hiperiondev/esp32idf_APRS/docs/en/internals/architecture.rst

.. _en-architecture:

============
Architecture
============

Boot sequence
=============

``app_main()`` runs on the system main task, whose stack is set by
``CONFIG_ESP_MAIN_TASK_STACK_SIZE`` and is not meant to host heavy work —
``esp_netif`` + ``esp_wifi`` + ``esp_http_server`` + cJSON can use several KB of
stack between them. So ``app_main()`` does only the three things that must
precede everything, then hands off to a dedicated task:

.. code-block:: text

   app_main()
    ├─ ptt_force_idle()          (PTT pad driven to its idle level; unconfigured from reset until here)
    ├─ nvs_flash_init()          (erase+retry on NO_FREE_PAGES / NEW_VERSION_FOUND)
    ├─ storage_init()            (mount LittleFS at /storage, auto-format on first boot)
    └─ xTaskCreate(app_task, 8192 B, prio 5)   ── and returns; FreeRTOS reclaims the main task

   app_task()
    ├─ app_config_load()                  ← one file per functionality under /storage, creating any that are missing
    ├─ cpu_freq_apply()                   ← 80/160/240 MHz from the System page
    ├─ net_state_init()                   ← "no internet yet"
    ├─ wifi_init()                        ← AP / STA / AP+STA per g_config.wifi_mode
    ├─ vTaskDelay(10 ms)                  ← yield so IDLE runs; avoids a false TWDT trip
    ├─ time_sync_start()                  ← arms the SNTP state machine (non-blocking)
    ├─ gps_apply_config()                 ← starts the GNSS reader task if enabled in config
    ├─ (confirm OTA image valid if pending-verify)
    ├─ aprs_service_start()               ← ⚠ MUST precede modem_init(): installs the RX callback
    ├─ if (audio_modem_en) modem_init()   ← ⏳ BLOCKS ~5 s calibrating the real ADC clock (once per boot)
    │      └─ aprs_service_notify_modem_ready()
    ├─ telegram_app_apply_config()        ← non-blocking; its own task waits for the network
    ├─ web_server_start_when_heap_ready() ← waits up to 5 s for a ≥24 KB largest free block, then
    │      └─ web_server_start()            starts regardless: esp_http_server, ~70 URI handlers, 20 KB stack
    └─ vTaskDelete(NULL)                  ← returns app_task's 8 KB stack to the heap

Three ordering rules are load-bearing and commented as such in the source:

#. **``aprs_service_start()`` before ``modem_init()``** — the modem starts
   delivering frames *from inside* ``modem_init()``; the RX callback must
   already be installed.
#. **Beacons start before the modem is ready** — they transmit immediately on
   entry, so ``aprs_service_send_tnc2()`` drops frames with a debug log until
   ``s_modemReady`` is set, rather than reaching the AX.25 writer before the
   AX.25 layer is initialised.
#. **The web admin server starts last** — every other service has already made
   its allocations by the time it runs, so its largest-contiguous-free-block
   check (``WEB_SERVER_MIN_LARGEST_FREE_BLOCK``, 24 KB, the httpd task's 20 KB
   stack plus headroom) sees the heap in the state the station will actually
   run in. A large total free heap does not guarantee this single allocation
   can be satisfied if the heap is fragmented, which is why the block size is
   checked rather than the total. It waits up to
   ``WEB_SERVER_HEAP_WAIT_MAX_MS`` (5 s) for a block that size to be free,
   polling every ``WEB_SERVER_HEAP_POLL_INTERVAL_MS`` (100 ms), then starts
   the server regardless of whether the threshold was reached: a reachable
   admin UI under memory pressure is more useful than none at all.

Inside ``aprs_service_start()``
===============================

.. code-block:: text

   aprs_service_start()
    ├─ trafficlog_init / lastheard_init / message_init
    ├─ message_set_tx_handler / igate_set_inet2rf_handler / igate_set_inet2rf_assoc_query
    ├─ xTaskCreate(rxTask "aprs_rx") + modem_set_rx_callback(on_rx_frame)
    │                                ← callback only queues; aprs_rx decodes and dispatches
    ├─ igate_start()                 ← always started; self-idles when nothing needs APRS-IS
    ├─ beacon_start() / weather_start() / bulletins_start() / objitems_start() / telemetry_start()
    ├─ beacon_scheduler_start()      ← ONE shared task drives all periodic TX and query answers
    └─ xTaskCreate(serviceTickTask)  ← 1 Hz: heap sample + weather refresh + message retry + time-sync SM

Task map
========

.. list-table::
   :header-rows: 1
   :widths: 20 12 8 10 22 28

   * - Task
     - Stack
     - Prio
     - Core
     - Created by
     - Role
   * - ``app_task``
     - 8192 B
     - 5
     - any
     - ``app_main``
     - boot, then deletes itself
   * - modem RX DSP
     - 4096 B
     - 10
     - **0**
     - ``AFSK_init()``
     - drains the ADC ring, runs the demodulators
   * - ``modem_svc``
     - 6144 B
     - 5
     - **0**
     - ``modem_init()``
     - drives TX (quiet time, DCD, persistence, key-up, teardown, TX time-out)
       and hands each RX frame to the callback, which only copies it into the
       ``aprs_rx`` queue; pinned to the same core as the RX DSP task, whose
       AX.25 ring it consumes
   * - ``aprs_rx``
     - 6144 B
     - 4
     - any
     - ``aprs_service_start()``
     - decodes each received frame and dispatches it: digipeater, IGate
       RF→INET, messages, queries, Winlink, Telegram routing, LAST HEARD,
       traffic log. Fed by an 8-frame queue, so a slow APRS-IS send never
       stalls transmit servicing
   * - ``modem_init``
     - 4096 B
     - high
     - **1**
     - ``AFSK_init()``
     - transient: runs the DAC sample-clock bring-up on the core that must own
       its interrupt, then deletes itself
   * - ADC DMA ISR
     - —
     - —
     - **0**
     - driver
     - conversion frames → ring buffer
   * - DAC sample clock (GPTimer, lvl 3)
     - —
     - —
     - **1**
     - ``AFSK_init()``
     - one DAC sample every 1/38400 s
   * - ``igate_task``
     - 6144 B
     - 5
     - any
     - ``igate_start()``
     - APRS-IS socket, login, RX pump, reconnect
   * - ``beacon_sched``
     - 14336 B
     - 4
     - any
     - ``beacon_scheduler_start()``
     - ONE shared task: all periodic own-station TX, plus the APRS query answers
       deferred to it
   * - ``aprs_svc_tick``
     - 10240 B
     - 4
     - any
     - ``aprs_service_start()``
     - 1 Hz: heap sample + weather refresh + message retry + time sync
   * - ``gps``
     - 4096 B
     - 4
     - any
     - ``gps_apply_config()``
     - reads the GNSS UART and parses NMEA; created only while the receiver is
       switched on, and deleted again when it is switched off
   * - ``telegram_service``
     - 8192 B
     - 5
     - any
     - ``telegram_app_apply_config()``
     - Telegram long polling over HTTPS and command dispatch; created only
       while the bot is switched on
   * - ``telegram_wk``
     - 8192 B
     - 4
     - any
     - ``telegram_app.c``
     - transient: runs one bot bring-up, teardown or send off the caller's
       stack, so a web POST never waits on TLS
   * - ``httpd``
     - 20480 B
     - —
     - any
     - ``web_server_start()``
     - web admin
   * - ``loop_diag``
     - 3072 B
     - 7
     - any
     - ``aprs_loop_test_run()``
     - transient: latches modem diagnostics for the duration of a LOOP TEST
   * - ``ota_reboot``
     - 2048 B
     - 5
     - any
     - the About page's OTA upload handler
     - transient: waits 1.5 s after a successful firmware upload — so the
       browser's XHR completes and the "rebooting..." message is actually
       seen — then calls ``esp_restart()``
   * - ``esp_timer``
     - —
     - —
     - —
     - IDF
     - Wi-Fi reconnect back-off

``beacon_sched`` and ``aprs_svc_tick`` are both created unconditionally inside
``aprs_service_start()``, i.e. before ``modem_init()``, the Telegram bot, and
``httpd`` — so their combined 24576 B is committed at boot regardless of
whether the operator has the modem or Telegram enabled for that boot. Both are
core, always-needed services, so starting them unconditionally is correct; only
their *sizes* are sized with headroom rather than trimmed to a measured
minimum, the same way ``GPS_TASK_STACK_BYTES`` and the ``httpd``
``config.stack_size`` are (see ``BEACON_SCHED_TASK_STACK_BYTES`` in
``beacon_scheduler.c`` and ``APRS_SVC_TICK_TASK_STACK_BYTES`` in
``aprs_service.c``). Both tasks log their ``uxTaskGetStackHighWaterMark()`` at
``ESP_LOGD`` every pass, which is the tool to right-size them against real
on-air traffic before lowering either constant.

Data flow
=========

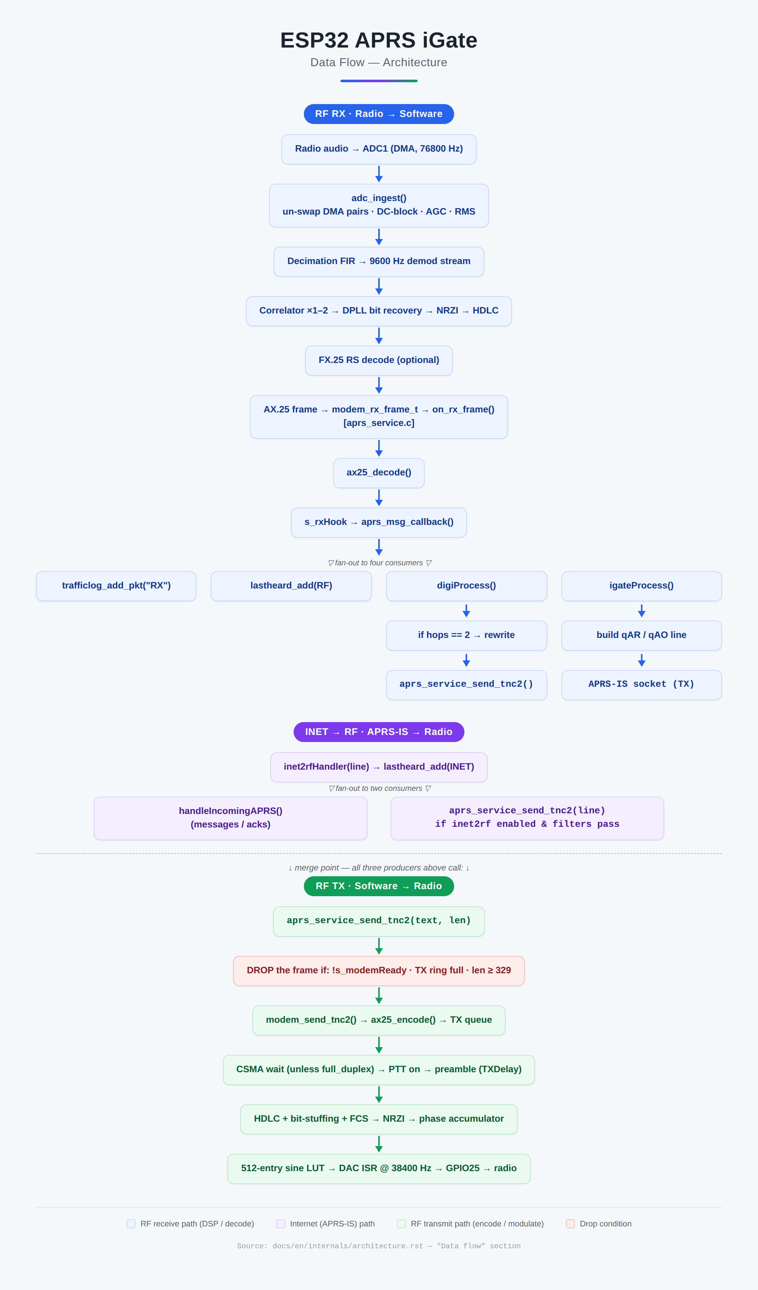
[picture p12: docs/dataflow/dataflow_en.png]
ESP32 APRS iGate data flow architecture diagram


The RF TX backlog cap
=====================

``aprs_service_send_tnc2()`` allows a small backlog rather than discarding the
moment one frame is in flight: up to ``g_config.rf_tx_buffers`` frames may sit in
the ring before a new packet is dropped. The value is read fresh on every call
(so the *TX buffers* setting applies to the very next packet, no reboot), and is
clamped to ``RF_TX_BUFFERS_MIN..RF_TX_BUFFERS_MAX`` — the max being derived from
``AX25_TX_FRAME_RING_MAX``, the ring's true usable depth, so the config layer can
never accept a value the ring could not hold. Only the beacon scheduler task is
allowed to *wait* for the ring to drain (see :ref:`en-beacons`); every other
caller drops immediately, so a busy RF leg never stalls RX decode or the APRS-IS
socket.

Building TNC2 lines
====================

Every module that assembles a TNC2 text line — ``beacon.c``, ``weather.c``,
``objects_items.c``, ``bulletins.c``, ``query.c`` and ``telemetry.c`` — follows
the same convention: the line is built into a buffer sized
``APRS_TNC2_BUF_SIZE`` (``main/include/aprs_service.h``), and a result at or
past that size, or past ``APRS_TNC2_MAX_LEN``, is refused with a warning log
rather than transmitted truncated. A half-written line is indistinguishable on air from a well-formed
one, so refusing it outright is the only outcome that never hands a receiving
station a plausible but wrong report. A new module that builds TNC2 lines
should follow the same convention.
