hiperiondev/esp32idf_APRS/docs/en/functionality/web-admin.rst

.. _en-web-admin:

=========
Web Admin
=========

The ``webconfig`` component (``components/webconfig/``) is an ``esp_http_server``
admin built from one file per page (``pages/*.c``), a route table
(``web_server.c``) and a set of shared helpers (``web_common.c``). It uses
**HTTP Basic auth** on every page — the exceptions being the static
``/style.css`` and ``/logo.png``, which carry no configuration or traffic
data — against either of two accounts, an administrator one and an optional
read-only one (see *Accounts and roles* below), plus wildcard URI matching, a
20 KB handler stack and LRU purge.

The logo at the left of the top bar is a PNG embedded in the firmware as a
``const`` array (``components/webconfig/include/web_logo.h``) and served by
``web_handle_logo()`` on ``GET /logo.png``. Keeping it in the application image
rather than in the LittleFS partition means the chrome of every page is
independent of a partition the Storage page can format, upload over and fill.
The stylesheet scales it by height alone (``height:32px;width:auto``, 26 px below
600 px), so the image's own proportions decide its width and a replacement of a
different shape needs no stylesheet change; the tag carries the PNG's intrinsic
size so the bar reserves the right width before the image arrives. The response
is cacheable for a day, since only an OTA update can change it.

Responsive layout
=================

One markup tree and one stylesheet serve desktop, tablet and phone. There is no
separate mobile page, no user-agent sniffing and no layout script: every page
carries a ``width=device-width`` viewport declaration, and ``web_handle_css()``
adapts the same components at three breakpoints.

.. list-table::
   :header-rows: 1
   :widths: 26 74

   * - Breakpoint
     - What changes
   * - **Above 900 px**
     - A fixed 220 px sidebar beside a content column capped at 1000 px.
   * - **900 px and below**
     - The sidebar becomes an off-canvas drawer opened by a burger button in
       the top bar, and the content column takes the full width. The top bar
       sticks to the top of the viewport, so the menu can be reached from
       anywhere in a long settings page without scrolling back up.
   * - **600 px and below**
     - Cards, headings and gutters tighten, and every ``.row`` of form fields
       collapses to a single column.
   * - **Coarse pointer**
     - Independently of width: buttons and menu entries grow to a 44 px touch
       target, checkboxes to 20 px, and text fields take a 16 px face — below
       that, a mobile browser zooms the page in when a field is focused and
       leaves it zoomed.

The drawer is CSS-only. ``web_send_header()`` emits a hidden checkbox as a
sibling of both the top bar and the layout, plus the burger and a backdrop that
are both labels for it, so the stylesheet reaches all three from the checkbox's
``:checked`` state. Nothing has to be initialised, nothing breaks if a script
fails to load, and an ordinary page load leaves the menu closed again.

Two details carry most of the horizontal behaviour:

* The content column is a flex item with ``min-width: 0``. Without it a flex
  item refuses to shrink below the width of its widest child, so a single wide
  table would widen the whole page instead of scrolling inside itself.
* Every table on every page is emitted inside a ``table-wrap`` frame. A table
  sizes itself to its own columns and cannot be narrowed without folding its
  cells, so the frame absorbs the difference: the eight-column telemetry and
  weather tables keep their full width and scroll sideways within the page. The
  dashboard's traffic table scrolls on both axes, since it also holds more rows
  than fit on screen.

Responses that are shown outside the admin chrome — the save interstitial, the
``401`` / ``403`` / ``429`` bodies, and a handler's page-level refusal — go
through ``web_send_standalone_page()``, which wraps a fragment in a minimal
document of its own. That document carries its own viewport declaration and its
own inline rules rather than linking ``/style.css``: it has to render the same
way when the stylesheet cannot be served, which is exactly what some of these
responses are reporting.

Why per-field helpers
=====================

HTML is emitted through small per-field helpers (``web_field_text``,
``web_field_int``, ``web_field_checkbox``, ``web_select_*``,
``web_field_symbol``, …) rather than one giant ``snprintf`` — deliberately, to
avoid ``-Werror=format-truncation`` and to keep each page readable.

The numeric helpers (``web_field_int``, ``web_field_float``) take the field's
accepted range and always emit it as the input's HTML ``min``/``max``, so every
numeric field on every page is validated by the browser before the form is
submitted. That is the first line of defence against a typo; the POST handler
still clamps what it stores, which is what holds against a crafted request.
Recurring domains (SSID, transmit interval, latitude, longitude, altitude) come
from the ``WEB_RANGE_*`` constants in ``web_common.h`` so a bound is defined
once for every page that shares it.

Contextual help
===============

Every option on every page ends its label with a small orange circled question
mark. Resting the pointer on it — or giving it keyboard focus, or tapping it on
a touch screen — opens a balloon with a short explanation of what that option
does, bounded at ``WEB_HELP_MAX_BYTES`` (253 bytes) so it stays readable at a
glance over the control it explains.

``web_help_markup()`` emits a focusable ``span.hlp`` holding the glyph and a
nested ``span.hlp-box``, and ``web_handle_css()`` draws the circle, colours it
and reveals the balloon from the marker's own ``:hover`` and ``:focus``. No
state survives a page load, and the ``:focus`` half is what makes the help
reachable without a mouse. A tap on the marker is stopped from also activating
the label it sits inside, so asking what a checkbox does never toggles it.

The balloon is drawn as a fixed layer over the whole page rather than as a box
inside the field's own card. Markers sit inside cards, accordions and table
frames, and several of those clip what leaves them — the accordion hides its
overflow so its rounded corners stay clean, and a table frame that scrolls
sideways clips vertically as well — so a balloon laid out inside one of them
would be cut off at its edge whenever the text is longer than the room left
above the field. Lifting it out of the flow is what lets every balloon be read
in full, over every card, table and control on the page.

Coordinates are the one thing the stylesheet cannot then supply, so the script
``web_send_footer()`` emits on every page provides them: it measures the marker,
centres the balloon over it, pulls it back inside whichever screen edge it would
cross, flips it under the field when there is not enough room above, and slides
the arrow along its edge so it keeps pointing at the marker after any of that.
An open balloon is placed again on scroll and on resize, the scroll listener
capturing so it also follows the log, chat and table frames that scroll inside
themselves. The handlers are bound to the document rather than to each marker,
so they equally cover rows a page's own script adds after load.

The help text is **looked up from the label, not passed in**. Pages call
``web_field_int(req, TR_F_SSID, …)`` exactly as they did before the feature
existed; ``web_help_for_label()`` matches that label against the table in
``web_help.c``, which pairs each ``TR_xxx`` label macro with its ``TR_H_xxx``
help macro. That keeps every existing call site untouched and means a label several
pages share is explained once and reads identically on all of them. An option
whose label has no row in the table simply renders without a marker.

A handful of labels are assembled at run time — ``Alias 2``, ``Callsign 3``, a
payload-type filter, a numbered path preset — and so match nothing. Those call
sites render the marker once with ``web_help_markup()`` outside their loop and
pass it to each row through the ``_h()`` variant of the helper
(``web_field_text_h``, ``web_field_int_h``, ``web_field_checkbox_plain_h``,
``web_select_open_h``).

Adding an option therefore means adding its ``TR_H_xxx`` string to all three
``lang_*.h`` files and one row to ``web_help.c``. Leaving the row out is not a
build error — the option renders with no question mark — so the table is worth
a glance whenever a page grows a field.

The pages
=========

.. list-table::
   :header-rows: 1
   :widths: 22 78

   * - Page
     - What it does
   * - **Dashboard**
     - Network Status pills (Wi-Fi, APRS-IS via ``igate_is_connected()``), a
       STATISTICS panel, a system-info strip refreshed once a second, and a live
       traffic table (DX / PACKET / DECODED / AUDIO) fed by sequence-based long
       polling. The traffic table is the only station list the page draws; the
       per-station LAST HEARD data is exposed as the ``/lastheard`` JSON feed
       and is consumed by the message gate, the ``?APRSD``/``?APRSH`` answers
       and the BrandMeister status count rather than being rendered here. DECODED holds what was read out of the payload itself - the
       packet's own timestamp, course, speed, altitude, radio range, PHG or
       DFS, and the bearing and NRQ of a DF report - and is empty for a payload
       that carries none of them. The column holds a whole summary line
       whatever the payload: the ring sizes its field from the same constant
       the formatter writes into, so a report that fills every field is shown
       entire rather than cut short.
   * - **Station**
     - The shared own-station identity read by every beacon, object and
       message: callsign, latitude, longitude, altitude (``g_config.my_*``),
       plus the station-wide on-air options - position ambiguity, the
       Maidenhead locator prefix for status reports, and the meteor-scatter
       beam heading and ERP that close them. Position can be typed in or
       taken live from the GNSS receiver via *Use GPS*, which disables the
       three fields and fills them from ``GET /gps/live`` once a second while
       checked, rounding latitude and longitude to 4 decimal places and
       altitude to 1 decimal place so the filled values always pass the
       fields' own validation.
   * - **IGate**
     - Enable, RF→INET / INET→RF, both filter bitmasks, budlist and range/prefix
       gates, callsign/SSID/passcode, four *APRS-IS Server* fieldsets (each an
       Enable checkbox plus host and port, used as a failover rotation),
       server-side filter string, the *Log after filters* switch that narrows the
       traffic table and the serial console to what the local filters accept,
       nine payload-type checkboxes per direction (the ninth, *Other*, covers
       station capabilities, user-defined formats, Agrelo direction finding,
       Maidenhead locator beacons and the reserved map feature),
       beacon on/off, position, interval, symbol picker, object, comment,
       status, PHG, and a frequency/repeater fieldset (frequency, duplex,
       offset, tone) whose block opens the beacon's comment and status text.
       *Message Gating* holds the INET→RF message criteria switch,
       the heard-locally window and the addressee hop limit. Position can be
       typed in, mirrored from *Use My Station Data* or taken live from the
       GNSS receiver via *Use GPS*; the three are mutually exclusive.
   * - **BrandMeister**
     - Interconnect enable switch, the worldwide monitor subscription, the
       Internet-only message routing switch for BrandMeister addressees, and
       four optional gateway callsigns. The monitor switch is refused while
       INET→RF gating is on and the INET→RF range filter on the *IGate* page is
       off, since APRS-IS filter terms are OR'd and nothing else would stand
       between a worldwide feed and the transmitter. A read-only status table
       reports the interconnect state, whether ``u/APBM*`` is present in the
       server filter, the range filter's setting and how many BrandMeister
       stations are currently in LAST HEARD. No DMR connection of any kind is
       involved; see :ref:`en-brandmeister`.
   * - **Digi**
     - Digipeater enable, callsign/SSID and beacon settings (position, symbol,
       interval, comment, status, path). *Data Extension* selects what the
       position beacon carries in the slot after the symbol code — PHG, RNG,
       DFS or a DF report — with the same sub-fields and the same *Use My
       Station Data* mirror the *IGate* page offers, and a frequency/repeater
       fieldset like that page's. *n-N Path Aliases* holds the four
       {alias, max N, mode} rows the digipeater repeats by, the fill-in-only
       switch, the choice of what to do with a trapped hop count and the
       *Digipeat by destination SSID (legacy)* switch, off by default. It also
       carries the four shared path presets ``path[0..3]`` that every
       transmitting service selects from. Duplicate suppression (switch, cache size
       and window) is set only on the *IGate* page. Position can also be taken live
       from the GNSS receiver via *Use GPS*, mutually exclusive with *Use My
       Station Data*.
   * - **Tracker**
     - Tracker enable, callsign/SSID, fixed interval, position, station symbol,
       comment, compressed-position, Mic-E-position (with its position-comment
       selector), PHG and altitude options. The fixed position can be typed in,
       mirrored from *Use My Station Data* or taken live from the GNSS
       receiver via *Use GPS*; the three are mutually exclusive. *Use live GPS
       fix* is separate from all three: it leaves the fixed position as the
       fallback and has each transmission read the receiver instead. The
       *SmartBeaconing* fieldset (slow/fast interval, low/high speed, turn
       angle, turn slope, minimum turn time) makes that interval
       speed-adaptive; it needs the live fix to have anything to work from.
       A status-beacon fieldset (interval and text) and a frequency/repeater
       fieldset (frequency, duplex, offset, tone) close the page.
   * - **Weather**
     - Enable, send-via-RF/-INET, timestamp, WX callsign/SSID/path, position,
       object name, comment, per-field *Averaged* checkboxes, and — for every
       on-air WX field — a **channel dropdown** populated live from the
       ``sensors_local`` registry and filtered by each driver's published
       capabilities. Live values via ``/wx/values``. Position can be typed in,
       mirrored from *Use My Station Data* or taken live from the GNSS
       receiver via *Use GPS*; the three are mutually exclusive.
   * - **Telemetry**
     - Beacon/report parameters, definition-message toggles, analog A1–A5 with
       source pickers and calibration, digital B1–B8 with source pickers and
       sense. Live values via ``/tlm/values``.
   * - **GPS**
     - *Enable GPS Receiver* is the single switch the rest of the firmware
       tests before using anything the module reports; with it off the UART is
       not installed at all and the reader task does not run. Moving it takes
       effect immediately, without a reboot. Below it, a read-only live view of
       the receiver, led by a colour-coded *Module Status* badge that turns a
       page of numbers into a single diagnosis: red *Disabled* when the switch
       is off or the UART failed to come up, red *No data (check wiring)* when
       the module is enabled but nothing has arrived on the receive pin within
       the link timeout, amber *Searching (no fix)* once sentences are
       arriving but no valid navigation solution has been reported yet, and
       green *Fix OK* once one has. Below the badge, link state, navigation
       status, fix quality and 2D/3D mode, position, altitude and geoid
       separation, ground speed, course and magnetic variation, UTC date and
       time, satellites used and in view, HDOP/PDOP/VDOP, the accepted and
       discarded sentence counters and the age of the last sentence and fix.
       The serial port and its pins are compile-time board wiring and are
       shown as text. Live values via ``/gps/values``, polled every second.
       The plain-numeric counterpart, ``/gps/live``, is what every other
       page's *Use GPS* checkbox polls to auto-fill its own position/motion
       fields (Station, IGate, Digi, Tracker, Weather); each page's script
       rounds the polled latitude, longitude and altitude to the precision
       its own fields accept (4 decimal places for position, 1 decimal place
       for altitude) before writing them in.
   * - **Telegram**
     - *Enable Telegram Bot* switches the whole subsystem; with it off nothing
       connects to Telegram and no polling task runs, and moving it takes
       effect immediately without a reboot. Below it the bot token (rendered as
       a masked field, handled like every other stored secret - see
       :ref:`en-config-allow-show-password`) and the administrator's numeric
       identifier, which is carried as a
       64-bit value and posted as text because today's Telegram user
       identifiers no longer fit in 32 bits. Below that, the Mini App address
       and the fixed-size authorized-user and allowed-group-chat tables (up to
       8 users and 4 group chats, each an identifier plus a display name).
       Everything on this page is stored in ``/storage/telegram.json``, its own
       file like every other page's, so it can also be downloaded and uploaded
       from the File Storage page. The status
       table below the form reports where the connection stands and, when it
       stands still, exactly which step failed and what to do about it - the
       settings file is missing or unparseable, the token is empty or not of
       the form ``<numbers>:<secret>``, the root certificate is not on the
       storage partition, there is no route to the Internet yet, the heap could
       not supply a TLS session, or Telegram itself answered and refused, in
       which case its own error code and wording are shown untranslated. Live
       values via ``/telegram/status``, polled every two seconds. The bot the
       page brings up answers ``/status`` with every service's on/off switch -
       IGate, digipeater, tracker, weather, telemetry, messaging, query
       responder, BrandMeister, GNSS receiver, AFSK modem, TX duty-cycle
       limiter and SNTP time sync - and ``/sensors`` with every weather field
       and telemetry channel enabled on the Weather and Telemetry pages, each
       with the sensor driver it is mapped to and its current reading. Both
       answers are built from the configuration as it stands when the command
       arrives, so a save takes effect on the next command without a restart.
   * - **Winlink**
     - The station's two Winlink roles, on one page. *Winlink Account* holds
       what a session of its own needs: the APRSLink service callsign, the
       identity the mailbox is keyed on (the base callsign, without its SSID),
       the password a login challenge is answered from, and the switches that
       decide whether a session opens by itself, how long it may live, whether
       its traffic is kept off the air and whether the beacon comment announces
       this station as a Winlink reader. The password is rendered as a masked
       field, handled like every other stored secret (see
       :ref:`en-config-allow-show-password`), and is never transmitted: a
       challenge names three character positions and only those characters are
       sent back. *Gateway for Local Stations* holds the
       single setting of the other role, relaying a neighbour's own session,
       together with a read-only view of the three IGate settings that decide
       the same question, so all four inputs to the message gate can be seen at
       once. Below the form, the session terminal: where the session stands and
       how long it has left, buttons for logging in and out and for listing
       mail, a free-form command field that takes the whole APRSLink command
       set, a three-step helper for writing a message, and the replies the
       service has sent back. Each stored reply that opens with a message
       number is a line of a mailbox listing and carries a *Read* / *Reply* /
       *Forward* / *Delete* row for that message; a *Message number* field
       under the mailbox carries the same four for a number typed by hand.
       Live values via
       ``/winlink/status`` and ``/winlink/list``, polled every three seconds;
       actions are posted to
       ``/winlink/cmd``, which is POST because it keys the transmitter.
   * - **Logs**
     - A viewer for the serial console, so what the station prints can be read
       without a cable attached. There is nothing to configure: one button,
       which reads *Start* while nothing is being captured and *Stop* while
       something is, and one window below it holding the last 50 lines. A
       console line longer than 255 characters is continued on the next row
       rather than cut, and the window scrolls in both directions - vertically
       because it holds more rows than fit on screen, horizontally because
       each line is kept whole. Pressing *Start* installs a mirror on the log
       writer; the serial output itself is unchanged either way, and the ring
       the mirror fills is allocated only while a capture is running.
       Capturing never outlives the page: the page asks the station to stop
       anything left running as it loads, so the button always comes up in its
       *Start* state; leaving it stops the capture from the browser; and a tab
       that is closed, put to sleep or cut off mid-session says nothing at
       all, which is why the mirror also stops itself once nothing has read it
       for ten seconds. Nothing is written to flash and nothing is recorded -
       only what arrives while the window is open is shown. Each line keeps
       every byte the console printed except the carriage return, so an
       ``RX:`` line shows a received frame's information field exactly as it
       arrived, Mic-E control bytes included. Live lines via
       ``/logs/read``, polled every second. The button is disabled for the
       length of a *Start* request and a status line beside it reports
       whether the station could not start capturing - the allocation for
       the window can lose out to heap pressure elsewhere on the station -
       or could not be reached at all.
   * - **Bulletins**
     - Up to five bulletins (addressee identifier and group, text, RF/INET,
       initial interval, decay ramp, expiry).
   * - **Objects and Items**
     - Up to five objects/items (name, position, symbol, course/speed, comment,
       RF/INET, interval, permanent flag, kill).
   * - **Snd/Rcv Msg**
     - The APRS inbox/compose UI (``/msgchat``): one thread of sent and
       received messages, five visible at a time and ten kept.
   * - **Message**
     - Configures the messaging engine (RF/INET enable, retry, digipeat path,
       alarm GPIO), plus the *Message Groups* fieldset: three operator-defined
       group addressees read in addition to the built-in ``ALL``/``QST``/``CQ``.
   * - **Query**
     - APRS query responder enable, which source is answered (RF / APRS-IS —
       an answer always goes back on the channel the question arrived on),
       general query types (``?APRS?``,
       and where built, ``?WX?``/``?IGATE?``), directed-query enable, extended
       directed query set, minimum reply interval (airtime/loop safety floor),
       and the periodic station-capabilities beacon: enable, interval, RF and
       APRS-IS channel selection, and any extra capability tokens to append.
   * - **Radiomodem**
     - FX.25 on receive; audio modem enable, modulation (300 / 1200 Bell202 /
       1200 V.23 / 9600 G3RUH), flat/discriminator audio input, preamble ms, TX
       tail ms, TX time-slot ms, TX buffers, extra PTT unkey hold, CSMA persistence, CSMA
       slot time, busy-channel max wait and the
       long-term duty-cycle limiter (enable plus ceiling percentage); plus an
       *Audio interface* fieldset (ADC input self-bias, receive over-range
       warning, transmit output swing, transmit sample rate, transmitter
       time-out) and the **LOOP TEST**, **RX LEVEL** and **TX TEST** buttons.
       Save re-applies the modem live — no reboot, except the audio modem
       enable and the transmit sample rate. Documented field by field in
       :ref:`en-radiomodem`.
   * - **Wireless**
     - Mode (off/STA/AP/AP+STA), AP SSID/pass/channel, 5 STA slots each with its
       own Enable checkbox, TX power in dBm, plus a live scan.
   * - **System**
     - Web login, CPU frequency (applied live) and a *Time* section: NTP
       enable, NTP hosts ×3, resync interval, and a timezone selector that sets
       the local date/time shown on the dashboard (the clock itself stays UTC).
       Also the factory-reset button.
   * - **Storage**
     - LittleFS browser: download, delete, multipart upload, usage, format.
   * - **About / Firmware**
     - Project name, version, build date/time, IDF version, running partition,
       and the **OTA Update** panel.

.. note::

   Every control on these pages drives runtime behaviour: a setting that reaches
   its page's file is read by the service that owns it. The digipeater always
   handles WIDEn-N and repeats without an added delay, so neither is offered as
   an option.

   Duplicate suppression has exactly one set of controls, on the *IGate*
   page: the *Enable duplicate suppression* switch (``dupCacheEn``) and, below
   it, *Dup cache size* (``dupCacheSize``) and *Dup cache timeout*
   (``dupCacheTimeoutMs``). They govern the digipeater as well as the IGate:
   both services share the one cache in ``components/igate``, each with its
   own scope. With the switch off, no frame is ever treated as a duplicate by
   either service, and the two numeric fields are greyed out and keep their
   stored values.

The dashboard statistics
========================

The statistics come from ``aprs_service_get_stats()``, tracked **independently**
of ``igate_en``/``digi_en``:

.. list-table::
   :header-rows: 1
   :widths: 24 76

   * - Counter
     - Meaning
   * - ``radio_rx``
     - Every frame the modem decoded off RF.
   * - ``radio_tx``
     - Every frame successfully transmitted on RF.
   * - ``rf2inet``
     - Frames the IGate actually uplinked.
   * - ``inet2rf``
     - APRS-IS lines actually transmitted on RF.
   * - ``digi``
     - Frames digipeated (path rewritten + retransmitted).
   * - ``drop`` / ``err``
     - Frames discarded / that failed to decode, at the RX/service level.
   * - ``tx_queue_depth`` / ``tx_queue_limit``
     - The current RF TX ring backlog and the effective *TX buffers* cap, so the
       dashboard reads like the console's "n/n pending" line.
   * - ``csma_busy_forced`` / ``csma_persist_forced``
     - How often a frame was transmitted anyway: over a channel still busy
       after the *Busy channel max wait*, or after eight consecutive missed
       persistence rolls on a clear channel. Shown as *CSMA FORCED
       (BUSY/PERSIST)*. These are transmissions, not drops.
   * - ``tx_duty_cycle_pct`` / ``duty_cycle_limit_pct``
     - Measured transmit duty cycle over the rolling 10-minute window against
       the configured ceiling, as *TX DUTY CYCLE*. The limit reads ``0`` when
       the limiter is off, while the measured figure is populated either way.

This is deliberate. With both features off (a common RX-only/monitor setup) the
dashboard would otherwise stay pinned at zero no matter how much traffic was
decoded.

Live feeds
==========

* ``/lastheard`` — the LAST HEARD table (JSON), fed from both RF and APRS-IS. A
  station last heard before NTP synced carries an empty ``time`` field: the
  clock was still counting from the epoch when the frame arrived, so there is no
  time of day to state and none is invented.
* ``/igate_traffic?since=<seq>`` — the traffic log delta (JSON). Each entry
  carries a direction tag (``RX``/``TX``/``DIGI``/``INET2RF``/``RX-IS``), the DX
  callsign, the raw packet, the decoded-fields summary (``dec``, empty when the
  payload carries none), and the audio level in mV RMS (or −1). With *Log after
  filters* set on the IGate page, the ``RX`` and ``RX-IS`` entries cover only the
  traffic this station's own filters accept — see :ref:`en-igate`. The body is
  streamed one entry per HTTP chunk, so a client that is far behind still gets
  every buffered line: the response has no size cap and the firmware never
  assembles the whole document in RAM. The ``seq`` it reports back is the
  sequence number of the last entry actually delivered, so the cursor can only
  advance past lines the client has received; a cursor ahead of the ring — the
  device rebooted, and numbering restarted at 1 — resends from the oldest entry
  still buffered.
* ``/dashinfo`` and ``/sidebarInfo`` — compact live info fragments, polled once
  a second by the dashboard and the sidebar respectively. ``/heapinfo`` serves
  the same free/min-free heap pair as a two-field JSON object for a client that
  wants only those two numbers.

See :ref:`en-http-routes` for the full route table.

Accounts and roles
==================

The admin UI knows two accounts, both configured on the *System* page and both
presented over the same HTTP Basic realm:

* **Administrator** — ``g_config.http_username`` / ``http_password``, the
  account the station has always had (``admin`` / ``admin`` out of the box).
  Full access.
* **Read-only** — ``g_config.http_ro_username`` / ``http_ro_password``,
  optional and unset out of the box. It exists only while its username is
  non-empty, and it can never be the administrator name: the two pairs are
  matched administrator-first, so a read-only username equal to the
  administrator one is dropped on save rather than left looking configured.

What separates the two is what a request may *do*, never what it may see. Every
page and every live JSON feed renders identically for both, so a read-only
operator has the whole station in front of them — dashboard, traffic log,
every settings page, the last-heard feed, the storage listing. What a read-only
session cannot do is change anything: no settings form saves, no file is
uploaded, downloaded, deleted or formatted, no firmware image is accepted, no
factory reset runs, nothing is transmitted and no transmitter test keys the
radio. The one thing it may operate is the log console, whose *Start* and
*Stop* switch a mirror of the station's own output and change nothing on the
station itself.

The boundary is enforced in the handlers, in ``web_common.c``:

* ``web_check_auth()`` admits either account and is what every ``GET`` page and
  live feed opens with.
* ``web_check_auth_admin()`` admits the administrator alone, answering a
  read-only session ``403 Forbidden``, and is what every writing handler opens
  with — every ``POST`` save, ``/upload``, ``/download``, ``/delete``,
  ``/format``, ``/default``, ``/ota_update``, the radio tests and the outgoing
  message routes. ``/logs/start``, ``/logs/stop`` and ``/logs/read`` are the
  deliberate exceptions and stay on ``web_check_auth()``.

The pages also *look* read-only for that role, but nothing rests on it. A
banner is rendered above every page; ``web_send_footer()`` appends a small
script that disables every form control except the navigation drawer and the
controls a page marks ``.ro-ok`` (the log console button, the dashboard's
traffic pause and clear — all browser-side view controls); and the Storage page
leaves out the upload form, the format button and the per-file download and
delete actions entirely, since an ``<a href>`` carries no disabled state for a
script to set. A control re-enabled from a browser console buys a ``403`` and
nothing else.

Secrets are masked for a read-only session regardless of the
``ALLOW_SHOW_PASSWORD`` build flag (``main/include/app_config.h``): the pages
carrying the Wi-Fi key, the APRS-IS passcode, the bot token and the
administrator password itself are readable by both roles, and a read-only
account is one that may look at the configuration, not one that may read the
keys out of it.

Login lockout policy
=====================

``web_check_auth()`` tracks failed Basic Auth attempts per source IPv4 address
in a small fixed-size table (``components/webconfig/web_common.c``). Only a
request that actually presented credentials and was rejected — a malformed
Basic payload, or a wrong username/password — counts as a failure. A request
with no ``Authorization`` header at all, or one that isn't ``Basic``, is the
challenge half of the HTTP Basic handshake that every browser performs on its
own, and is answered with a ``401`` without being charged against the budget;
this is what lets the dashboard's authenticated pollers (``/dashinfo``,
``/sidebarInfo``, ``/igate_traffic``, and the per-page feeds such as
``/wx/values`` or ``/gps/live``) sit behind a fresh login page without ever
tripping a lockout on their own.

After 5 consecutive rejected credentials from the same source, that source is
locked out and every further request gets ``429 Too Many Requests`` with a
``Retry-After`` header instead of a ``401``, for a window that starts at 5 s
and doubles on each further rejected attempt while still locked out, capped at
300 s. A window that elapses without a successful login rearms one failure
below the threshold rather than resuming from the accumulated count, so a
client that keeps retrying the same stale credentials after every window
expires re-triggers only the base 5 s lockout each time, instead of ratcheting
straight back to the 300 s cap. A successful login clears the source's slot
entirely.

Same-origin protection (CSRF)
==============================

``web_check_auth()`` also enforces a same-origin check on every ``HTTP_POST``
request, independently of whether ``g_config.http_username`` is set. The
check confirms the request's ``Origin`` header (falling back to ``Referer``)
names this device's own ``Host`` before anything else runs, and fails closed:
a request with neither header, or with a mismatching one, is rejected with
``403 Forbidden`` regardless of any credentials it carries.

This is deliberately independent of Basic Auth. Clearing the username on the
System page is a supported way to run the admin UI without a password, but
it only removes the login prompt — it does not
relax the same-origin requirement, because a browser-borne cross-site
request is a threat with or without a configured password: with no password
set there is no credential to steal, but the attacker's page can still make
the operator's own browser submit a state-changing request on their behalf.
Every state-changing route (``/ota_update``, ``/format``, ``/upload``,
``/delete``, ``/msgchat``, and every settings page's save handler) is
registered ``HTTP_POST`` for exactly this reason; no registered ``GET`` route
has a side effect, so this check never has to run against ordinary
navigation, bookmarks, or a typed-in URL.

.. seealso::

   :ref:`en-telegram` — the Telegram bot subsystem behind the *Telegram* page:
   its own configuration file, its supervised bring-up, and its built-in
   command set.
