hiperiondev/esp32idf_APRS/components/esp32idf_radioamateur_modem/test/host/README.md

# Host regression test — HDLC transmitter

🇬🇧 English · 🇪🇸 [Español](README.es.md) · 🇮🇹 [Italiano](README.it.md)

`test_ax25_tx_hdlc.c` compiles the real `src/ax25.c`, `src/crc_ccit.c` and the
FX.25 sources (`src/fx25.c`, `lwfec/rs.c`, `lwfec/gf.c`) for the host, against
the stand-in ESP-IDF headers in `stubs/`, under AddressSanitizer and
UndefinedBehaviorSanitizer.

It sends random AX.25 UI frames through `Ax25WriteTxFrame()` →
`Ax25TransmitCheck()` → `Ax25GetTxBit()` and checks every key-up:

- bit for bit against a reference HDLC encoder (frame + FCS stuffed as one
  field, including the stuffed 0 owed when a run of five 1s ends on the last
  FCS bit);
- through the in-tree receiver (`Ax25BitParse()` / `Ax25ReadNextRxFrame()`);
- through a strict receiver following Direwolf's `hdlc_rec.c` rules, which
  requires exactly seven data bits at the closing flag.
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
