hiperiondev/esp32idf_APRS/main/include/app_config.h

/**
 * @file app_config.h
 *
 * @author Emiliano Augusto Gonzalez ( lu3vea @ gmail . com)
 * @date 2026
 * @copyright GNU General Public License v3
 * @see https://github.com/hiperiondev/esp32idf_APRS
 *
 * @note
 * This is based on other projects:
 *     VP-Digi: https://github.com/sq8vps/vp-digi
 *     ESP32APRS: https://github.com/nakhonthai/ESP32APRS_Audio
 *     LibAPRS: https://github.com/markqvist/LibAPRS
 *
 *     please contact their authors for more information.
 *
 * @brief Global application configuration type (::app_config_t) and the
 * ::g_config instance, plus the compile-time module (@c ENABLE_*) and UI
 * language (@c LANGUAGE) selection macros.
 *
 * Every value the web admin shows or edits has its field here. The structure
 * persists to LittleFS as one file per web admin functionality - see
 * ::app_config_section_t for the list - under the JSON key names this header
 * documents field by field.
 *
 * The structure holds exactly the settings the firmware reads at runtime and
 * nothing else. That is a size decision as much as a tidiness one:
 * a save runs against a small, fragmented heap (see the streaming writer
 * there), so a key that no code consults is pure cost on every save.
 * Settings that are compile-time board wiring rather than operator choices are
 * therefore absent by design - the PTT pin and its active level, for instance,
 * are the ::MODEM_PTT_GPIO / ::MODEM_PTT_ACTIVE_HIGH constants and have no
 * field here.
 *
 * A section reader ignores any key it does not recognise, so a file carrying
 * keys this build has no field for still loads, and every field the file does
 * not mention keeps its default.
 *
 * Exactly one language is built into the firmware image at a time - there is no
 * runtime language switch and no other language's strings are compiled in. To
 * change the language, change @c LANGUAGE below to one of the @c LANG_* codes (or
 * override it from the build system, e.g. idf.py build -DLANGUAGE=LANG_ES, or
 * `set(LANGUAGE LANG_ES)` / target_compile_definitions in CMakeLists.txt) and
 * rebuild. See translations/translations.h for how the selection works and
 * translations/lang_en.h / translations/lang_es.h / translations/lang_it.h for the string tables.
 */

#ifndef APP_CONFIG_H
#define APP_CONFIG_H

#include <stdbool.h>
#include <stdint.h>

#include "aprs_bm.h"                     // APRS_BM_GATEWAYS_MAX / APRS_BM_GATEWAY_LEN: dimensions of the stored BrandMeister gateway list
#include "esp32idf_radioamateur_modem.h" // modem_rx_tuning_t: the stored receive-chain tuning
#include "must_check.h"                  // APRS_MUST_CHECK: the persistence entry points below may not have their result discarded

/**
 * @name Firmware UI language selection
 *
 * Exactly one language is built into the firmware image at a time - there is
 * no runtime language switch and no other language's strings are compiled in.
 * To change the language, change @c LANGUAGE to one of the @c LANG_* codes and
 * rebuild. See translations/translations.h for how the selection works and
 * translations/lang_*.h for the string tables.
 * @{
 */
#define LANG_EN 0 /**< English. */
#define LANG_ES 1 /**< Espanol (Spanish). */
#define LANG_IT 2 /**< Italiano (Italian). */

#ifndef LANGUAGE
#define LANGUAGE LANG_EN /**< Active UI language, one of the @c LANG_* codes. Overridable from the build system. */
#endif
/** @} */

/**
 * @name Compile-time module enables
 *
 * Each of these selects one web admin page / firmware feature into the build.
 * Modules that are not implemented are simply not defined here.
 * @{
 */
#define ENABLE_DASHBOARD      /**< Dashboard page. */
#define ENABLE_MSG_CHAT       /**< "Snd/Rcv Msg" chat page. */
#define ENABLE_BULLETINS      /**< APRS bulletins page. */
#define ENABLE_OBJECTS_ITEMS  /**< APRS Objects/Items page. */
#define ENABLE_STATION        /**< "My Station" page. */
#define ENABLE_RADIO_MODEM    /**< Radiomodem page. */
#define ENABLE_MESSAGE        /**< APRS Message service page. */
#define ENABLE_IGATE          /**< IGate page. */
#define ENABLE_BRANDMEISTER   /**< BrandMeister interconnect page. */
#define ENABLE_QUERY          /**< Query responder page. */
#define ENABLE_DIGIPEATER     /**< Digipeater page. */
#define ENABLE_TRACKER        /**< Tracker page. */
#define ENABLE_WEATHER        /**< Weather page. */
#define ENABLE_TELEMETRY      /**< Telemetry page. */
#define ENABLE_GPS            /**< GPS receiver page. */
#define ENABLE_TELEGRAM       /**< Telegram bot page. */
#define ENABLE_WINLINK        /**< Winlink (APRSLink) radio e-mail page. */
#define ENABLE_LOGS           /**< Console Logs page. */
#define ENABLE_SYSTEM         /**< System page. */
#define ENABLE_WIRELESS       /**< Wireless page. */
#define ENABLE_FILE_STORAGE   /**< File Storage page. */
#define ENABLE_ABOUT_FIRMWARE /**< About / Firmware page. */

/**
 * @brief Whether the web admin may hand a stored secret back to the browser in
 * clear text.
 *
 * Unlike the @c ENABLE_* switches above this one is a policy flag and is
 * spelled as a value, so it is set by editing the number rather than by
 * commenting the line out. It is @c 0 by default, which is the private
 * setting:
 *
 * - @c 0 - no secret ever leaves the device through an admin page. Every
 *   password, passcode and bearer token field is rendered holding the fixed
 *   @c WEB_PASSWORD_MASK placeholder when one is stored (and empty when none
 *   is), and the "Show password" checkbox is not emitted at all, neither on
 *   the pages nor as the script behind it. A field posted back still carrying
 *   the placeholder means "leave this secret alone"; any other value - the
 *   empty string included - replaces it, so a secret is changed and cleared
 *   exactly as it always was.
 * - @c 1 - the historical behaviour: fields are pre-filled with the stored
 *   secret and each carries a "Show password" checkbox that turns the masked
 *   input into a plain-text one.
 *
 * The one value this costs at @c 0 is the literal @c WEB_PASSWORD_MASK string
 * itself, which cannot be stored as a secret because it is indistinguishable
 * from an untouched field.
 */
#define ALLOW_SHOW_PASSWORD 0
/** @} */

/**
 * @name Winlink (APRSLink) accepted ranges
 *
 * Single source of truth for the bounds the Winlink page's form advertises and
 * for the clamps applied both in its POST handler and when the file is read,
 * so a hand-edited winlink.json cannot put a value on the device that the form
 * would have refused.
 * @{
 */
#define WL_SESSION_MAX_MIN_MIN     5    /**< Shortest local session lifetime, minutes. */
#define WL_SESSION_MAX_MIN_MAX     180  /**< Longest local session lifetime, minutes. */
#define WL_SESSION_MAX_MIN_DEFAULT 110  /**< Default local session lifetime, minutes, comfortably inside the service's own two-hour expiry. */
#define WL_POLL_MIN_MIN            0    /**< Never ask the service for a listing unprompted. */
#define WL_POLL_MIN_MAX            1440 /**< Longest interval between unprompted listings, minutes (24 h). */
/** @} */

/**
 * @brief Default APRSLink service callsign: the CMS-hosted gateway between
 * APRS and the Winlink radio e-mail system.
 */
#define WL_SERVICE_CALL_DEFAULT "WLNK-1"

/**
 * @brief Size of the comment buffers (IGate/Digipeater/Tracker/Weather):
 * 128 bytes of comment text + NUL terminator.
 */
#define COMMENT_SIZE 129
/**
 * @brief Size of the status-text buffers.
 */
#define STATUS_SIZE 50

/**
 * @brief Size of the free-form Station Capabilities token buffer: 63 bytes of
 * operator text + NUL terminator. The two mandatory tokens and the enclosing
 * "<IGATE" and ">" bytes leave this much of an information field that still
 * fits any hop count a beacon path can carry.
 */
#define QUERY_CAP_EXTRA_SIZE 64

/**
 * @brief Weather station "Sensor Mapping" rows: the canonical on-air list of
 * every quantity an APRS Weather Report can carry, one row per mappable
 * measurement.
 *
 * @details This is the on-air list defined by APRS101 ch.12 plus the APRS 1.2
 * flood proposals. Each row corresponds 1:1 to a field the WX encoder in
 * weather.c emits and is used to index the per-field mapping arrays
 * (@c wx_sensor_* in ::app_config_t).
 *
 * The list is limited to quantities that have a Weather Report token on-air.
 * Extended measurements such as UV, soil moisture, water level or battery
 * voltage have no such token and are carried as Telemetry instead, so they are
 * deliberately absent here.
 *
 * New rows go immediately before ::WX_SENSOR_NUM, which keeps every existing
 * row at the position a stored @c weather.json already uses. The loader reads
 * the persisted arrays element by element and leaves anything the stored array
 * is too short to cover at its default, so a file written by an earlier build
 * loads with the new field disabled and every other field mapped as before.
 */
typedef enum {
    WX_FIELD_WIND_DIRECTION = 0, /**< Wind direction, deg     -> "ddd/" (aprs_wind_t.direction_deg). */
    WX_FIELD_WIND_SPEED,         /**< Sustained wind, mph     -> "/sss" (aprs_wind_t.sustained_mph). */
    WX_FIELD_WIND_GUST,          /**< Peak gust, mph          -> "gXXX" (aprs_wind_t.gust_mph). */
    WX_FIELD_TEMPERATURE,        /**< Air temperature, deg F  -> "tXXX". */
    WX_FIELD_RAIN_1H,            /**< Rain last hour, 1/100 in-> "rXXX". */
    WX_FIELD_RAIN_24H,           /**< Rain last 24h, 1/100 in -> "pXXX". */
    WX_FIELD_RAIN_MIDNIGHT,      /**< Rain since midnight      -> "PXXX". */
    WX_FIELD_SNOW_24H,           /**< Snow last 24h, 1/10 in  -> "sXXX" or "sX.X" below 10 in (see aprs.org/aprs11/spec-wx.txt). */
    WX_FIELD_HUMIDITY,           /**< Relative humidity, %    -> "hXX". */
    WX_FIELD_PRESSURE,           /**< Barometric pressure     -> "bXXXXX" (tenths of mb). */
    WX_FIELD_LUMINOSITY,         /**< Solar luminosity, W/m^2 -> "LXXX"/"lXXX" (APRS 1.2). */
    WX_FIELD_FLOOD_HEIGHT_FT,    /**< Flood/water gauge, feet -> "FXXXX.X" (APRS 1.2). */
    WX_FIELD_FLOOD_HEIGHT_M,     /**< Flood/water gauge, m    -> "fXXXX.X" (APRS 1.2). */
    WX_FIELD_RAIN_RAW,           /**< Raw tip-bucket counter  -> "#XXXX" (APRS101 ch.12), un-reset running count. */
    WX_SENSOR_NUM                /**< Sentinel: number of mappable WX fields. Not a real field. */
} wx_field_id_t;

/** @brief Number of stored WiFi station (STA) profiles. */
#define WIFI_STA_NUM 5
/** @brief Number of configurable NTP host slots. */
#define NTP_HOST_NUM 3
/** @brief Minimum NTP resync interval, in seconds. */
#define NTP_RESYNC_MIN_SEC 30

/**
 * @name SoftAP channel range
 * @brief Accepted range and fallback for ::app_config_t::wifi_ap_ch.
 *
 * esp_wifi_set_config() rejects an AP channel outside this range with
 * ESP_ERR_INVALID_ARG, so the stored value is clamped both when a form is
 * saved and when wireless.json is loaded, and the AP setup in main.c never
 * treats a driver rejection as fatal.
 * @{
 */
#define WIFI_AP_CH_MIN     1  /**< Lowest usable SoftAP channel. */
#define WIFI_AP_CH_MAX     13 /**< Highest usable SoftAP channel. */
#define WIFI_AP_CH_DEFAULT 1  /**< Fallback SoftAP channel, used whenever the stored one is out of range. */
/** @} */

/**
 * @name WiFi interface selector
 * @brief Accepted values and factory value for ::app_config_t::wifi_mode.
 *
 * The stored value selects which of the two WiFi interfaces are brought up; it
 * is this project's own numbering, chosen to match the order of the Wireless
 * page's drop-down, and is mapped to the IDF's ::wifi_mode_t in main.c. The
 * factory value keeps the SoftAP up on a device that has never been
 * configured, which is the only way to reach the web admin of a station whose
 * station credentials are unknown or wrong.
 *
 * wifi_init() brings the SoftAP up for ::WIFI_MODE_CFG_OFF as well as for any
 * value above ::WIFI_MODE_CFG_MAX, so no stored value leaves a headless
 * station without a web admin to correct it from.
 * @{
 */
#define WIFI_MODE_CFG_OFF     0                   /**< The Wireless page's "off" entry. */
#define WIFI_MODE_CFG_STA     1                   /**< Station only (::WIFI_MODE_STA). */
#define WIFI_MODE_CFG_AP      2                   /**< SoftAP only (::WIFI_MODE_AP). */
#define WIFI_MODE_CFG_APSTA   3                   /**< SoftAP and station together (::WIFI_MODE_APSTA). */
#define WIFI_MODE_CFG_MAX     WIFI_MODE_CFG_APSTA /**< Highest accepted value; anything above it falls back to the SoftAP. */
#define WIFI_MODE_CFG_DEFAULT WIFI_MODE_CFG_AP    /**< Factory interface selection. */
/** @} */

/**
 * @name WiFi transmit power range
 * @brief Accepted range and factory value for ::app_config_t::wifi_power, in dBm.
 *
 * esp_wifi_set_max_tx_power() takes quarter-dBm and refuses anything below 8
 * of them, so 2 dBm is the lowest setting the driver will actually apply; a
 * lower one is rejected, logged by the driver as a warning and leaves the
 * previous power in force, which reads to an operator as "minimum power" while
 * being "no change". The upper end is the maximum the ESP32 radio is rated
 * for. The stored value is therefore clamped both when the form is saved and
 * when wireless.json is loaded, so the value main.c multiplies by four is
 * always one the driver accepts.
 * @{
 */
#define WIFI_TX_POWER_DBM_MIN     2  /**< Lowest power the WiFi driver accepts (8 quarter-dBm). */
#define WIFI_TX_POWER_DBM_MAX     20 /**< Highest power the radio is rated for. */
#define WIFI_TX_POWER_DBM_DEFAULT 20 /**< Factory WiFi transmit power. */
/** @} */

/**
 * @name APRS-IS server port range
 * @brief Accepted range and fallback for ::app_config_t::aprs_port.
 *
 * Port 0 fits in a uint16_t but is not a connectable TCP port: getaddrinfo()
 * accepts the service string "0" and the following connect() then fails, so
 * the IGate would sit in a reconnect loop reporting a destination it could
 * never have reached. The value is therefore clamped both when the form is
 * saved and when igate.json is loaded.
 * @{
 */
#define APRS_PORT_MIN     1     /**< Lowest connectable TCP port. */
#define APRS_PORT_MAX     65535 /**< Highest TCP port. */
#define APRS_PORT_DEFAULT 14580 /**< Fallback APRS-IS port (the filtered-feed port), used whenever the stored one is out of range. */
/** @} */

/**
 * @name SmartBeaconing bounds and defaults
 * @brief Accepted ranges and factory defaults for the Tracker beacon's
 * SmartBeaconing fields (::app_config_t::trk_sb_*), following the standard
 * algorithm published by Hans-Gunnar Lundahl / HamHUD (aprs.org's
 * "SmartBeaconing" description). The two-layer clamp policy every other
 * bounded field in this project follows applies here too: the web form
 * bounds what the operator can enter, and app_config_load() bounds what a
 * hand-edited tracker.json can carry into the beacon builder.
 * @{
 */
#define TRK_SB_SLOW_INTERVAL_S_MIN 30    /**< Lowest selectable slow-rate (stationary) interval, seconds. */
#define TRK_SB_SLOW_INTERVAL_S_MAX 65535 /**< Highest selectable slow-rate interval, seconds (uint16_t width). */
#define TRK_SB_FAST_INTERVAL_S_MIN 5     /**< Lowest selectable fast-rate (moving at/above the high-speed threshold) interval, seconds. */
#define TRK_SB_FAST_INTERVAL_S_MAX 65535 /**< Highest selectable fast-rate interval, seconds (uint16_t width). */
#define TRK_SB_SPEED_KMH_MIN       0     /**< Lowest selectable low/high speed threshold, km/h. */
#define TRK_SB_SPEED_KMH_MAX       999   /**< Highest selectable low/high speed threshold, km/h. */
#define TRK_SB_TURN_ANGLE_MIN      1     /**< Lowest selectable minimum turn angle, degrees. */
#define TRK_SB_TURN_ANGLE_MAX      180   /**< Highest selectable minimum turn angle, degrees. */
#define TRK_SB_TURN_SLOPE_MIN      0     /**< Lowest selectable turn slope, degrees. A slope of 0 makes the turn threshold speed-independent. */
#define TRK_SB_TURN_SLOPE_MAX      3600  /**< Highest selectable turn slope, degrees. */
#define TRK_SB_MIN_TURN_TIME_S_MIN 0     /**< Lowest selectable minimum turn time, seconds. */
#define TRK_SB_MIN_TURN_TIME_S_MAX 3600  /**< Highest selectable minimum turn time, seconds. */

#define TRK_SB_SLOW_INTERVAL_S_DEFAULT 600 /**< Factory slow-rate interval, seconds: 10 minutes, the classic SmartBeaconing "stationary" cadence. */
#define TRK_SB_FAST_INTERVAL_S_DEFAULT 60  /**< Factory fast-rate interval, seconds: 1 minute, the classic SmartBeaconing "moving fast" cadence. */
#define TRK_SB_LOW_SPEED_KMH_DEFAULT   4   /**< Factory low-speed threshold, km/h: at or below this the beacon uses the slow-rate interval. */
#define TRK_SB_HIGH_SPEED_KMH_DEFAULT  100 /**< Factory high-speed threshold, km/h: at or above this the beacon uses the fast-rate interval. */
#define TRK_SB_TURN_ANGLE_DEFAULT      25  /**< Factory minimum turn angle, degrees: the classic SmartBeaconing corner-pegging threshold at speed. */
#define TRK_SB_TURN_SLOPE_DEFAULT      255 /**< Factory turn slope, degrees: widens the turn threshold at low speed (see beacon.c's corner-pegging note). */
#define TRK_SB_MIN_TURN_TIME_S_DEFAULT 15  /**< Factory minimum turn time, seconds: the classic SmartBeaconing corner-pegging re-arm guard. */
/** @} */

/**
 * @name Mic-E position comment selection
 * @brief Accepted range and fallback for ::app_config_t::trk_mice_msg.
 *
 * The A/B/C bits of a Mic-E destination address select one of fifteen
 * position comments (APRS101 Chapter 10, "Mic-E Message Types"): seven
 * Standard values M0-M6, seven locally defined Custom values C0-C6, and
 * Emergency when all three bits are clear. This setting maps them onto a
 * single contiguous range so one @c <select> can carry it: 0-6 are the
 * Standard values in order, 7-13 the Custom ones.
 *
 * Emergency has deliberately no value here. Transmitting it asks other
 * operators, and in some regions dispatchers, to respond to a real
 * emergency, which is not something a settings page should be able to arm
 * with one mis-click and leave armed for every beacon afterwards. A received
 * Emergency is fully decoded and raised to the operator; see
 * ::aprs_mice_message_name and the receive path in aprs_service.c.
 * @{
 */
#define MICE_POS_COMMENT_CUSTOM_BASE 7  /**< First value of the Custom C0-C6 block. */
#define MICE_POS_COMMENT_MAX         13 /**< Highest selectable value (Custom C6). */
#define MICE_POS_COMMENT_DEFAULT     0  /**< Factory default: M0 Off Duty, the conventional value for a station that does not move. */
/** @} */

/**
 * @brief Number of stored APRS-IS server slots (see ::app_config_t::aprs_server).
 *
 * The IGate task cycles through the enabled slots in order and wraps back to
 * the first one, so any slot left disabled is simply skipped rather than
 * shortening the rotation to fewer than ::APRS_SERVER_NUM entries.
 */
#define APRS_SERVER_NUM 4

/**
 * @brief Factory value of every per-service path selector
 * (::app_config_t::igate_path, ::app_config_t::digi_path,
 * ::app_config_t::trk_path, ::app_config_t::wx_path).
 *
 * Those fields are bitmasks over the four shared path presets
 * ::app_config_t::path[0..3]: bit N selects preset N, and
 * aprs_path_build_suffix() silently skips a bit whose slot is empty. Only
 * ::app_config_t::path[0] carries a factory string (::PATH_PRESET_DEFAULT), so
 * bit 0 is the only selection that puts a digipeater path on the air on a
 * factory-fresh station; any other single bit would beacon with a bare
 * destination call until the operator filled the matching preset in.
 *
 * The selector is a mask over path preset slots, not over services: a bit
 * names one of the four shared presets and nothing else.
 */
#define PATH_PRESET_MASK_DEFAULT (1 << 0)

/**
 * @brief Factory string of path preset slot 0, the generic New n-N Paradigm
 * path every service selects out of the box via ::PATH_PRESET_MASK_DEFAULT.
 *
 * Named rather than written inline because two factory values are derived from
 * it: the preset slot itself, and the reach of the INET->RF message gate
 * (::app_config_t::igate_msg_max_hops), which defaults to the number of hops
 * this path travels.
 */
#define PATH_PRESET_DEFAULT "WIDE1-1,WIDE2-1"

/**
 * @name IGate [Filter] section bit flags
 * @brief Shared payload-type bits for rf2inetFilter / inet2rfFilter (see
 * aprs_filter.h). A set bit means "relay this payload type".
 * @{
 */
#define IGATE_FILT_MESSAGE   (1 << 0) /**< APRS messages. */
#define IGATE_FILT_STATUS    (1 << 1) /**< Status reports. */
#define IGATE_FILT_TELEMETRY (1 << 2) /**< Telemetry reports. */
#define IGATE_FILT_WEATHER   (1 << 3) /**< Weather reports. */
#define IGATE_FILT_OBJECT    (1 << 4) /**< Object reports. */
#define IGATE_FILT_ITEM      (1 << 5) /**< Item reports. */
#define IGATE_FILT_QUERY     (1 << 6) /**< Queries. */
#define IGATE_FILT_BUOY      (1 << 7) /**< Buoy position reports. */
#define IGATE_FILT_POSITION  (1 << 8) /**< Plain position reports. */
/**
 * @brief Payload kinds that have no bit of their own: station capabilities
 * ('<'), user-defined formats ('{'), Agrelo direction finding ('%'),
 * Maidenhead locator beacons ('[') and the reserved map feature ('&').
 *
 * They share one checkbox because each is rare on its own and none has a
 * setting a gateway operator would want to turn on or off independently of
 * the others; what matters is that they are gateable at all, since a
 * classification of 0 means "never relay" whatever the mask says. Third-party
 * traffic ('}') and test data (',') are deliberately left out of this bit and
 * keep their zero classification - re-gating third-party traffic is how IGate
 * loops start, and test data is not meant to leave the channel it was sent on.
 */
#define IGATE_FILT_OTHER (1 << 9)
/** @} */

/**
 * @name INET->RF message gating window
 * @brief Accepted range and factory default for
 * ::app_config_t::igate_local_window_sec.
 *
 * The window is how far back the IGate looks in the last-heard table when it
 * decides whether a station counts as "heard locally": an APRS message read
 * from APRS-IS is only put on the air when its addressee was heard on RF
 * inside this many seconds. One hour is the upper bound the APRS-IS IGate
 * design notes recommend, and is also the factory default; shortening it makes
 * the gateway more conservative on a busy channel.
 * @{
 */
#define IGATE_LOCAL_WINDOW_SEC_MIN     60   /**< Shortest accepted "heard locally" window, seconds. */
#define IGATE_LOCAL_WINDOW_SEC_MAX     3600 /**< Longest accepted "heard locally" window, seconds. */
#define IGATE_LOCAL_WINDOW_SEC_DEFAULT 3600 /**< Factory default "heard locally" window, seconds. */
/** @} */

/**
 * @name Gateway range-gate bounds
 * @brief Accepted range, in kilometres, for both directions' local distance
 * gate: ::app_config_t::rf2inet_range_km and ::app_config_t::inet2rf_range_km.
 *
 * The ceiling is half the Earth's circumference along a meridian - the
 * greatest distance aprs_filter_haversine_km() can ever return - so anything
 * at or above it means "no limit" as surely as the 0 sentinel does, and
 * nothing between the two is unreachable.
 * @{
 */
#define APRS_RANGE_KM_MIN 0.0f     /**< Lowest accepted range-gate radius; 0 disables the limit. */
#define APRS_RANGE_KM_MAX 20038.0f /**< Highest accepted range-gate radius, kilometres. */
/** @} */

/**
 * @name INET->RF message gating hop limit
 * @brief Accepted range for ::app_config_t::igate_msg_max_hops.
 *
 * The window above says how recently the addressee was heard; this says how far
 * away it was when it was. The IGate design notes measure a gateway's coverage
 * area in digipeater hops and ask that it be set to the minimum number of hops
 * it needs, because a station whose frames only arrive through several
 * digipeaters is very likely out of reach of a transmission from here. 0 gates
 * only to stations heard direct, which is the strictest reading of that rule;
 * 8 is the longest path AX.25 can carry at all (the same via-address limit
 * app_config_path_mask_clamp() enforces on this station's own paths) and
 * therefore the widest setting that means anything.
 *
 * The factory default is not a constant: app_config_set_defaults() takes it
 * from the hop count of the default IGate transmit path, so out of the box the
 * gateway offers to reach exactly as far as it can transmit.
 * @{
 */
#define IGATE_MSG_MAX_HOPS_MIN 0 /**< Strictest accepted hop limit: addressee must have been heard direct. */
#define IGATE_MSG_MAX_HOPS_MAX 8 /**< Widest accepted hop limit, the AX.25 via-address maximum. */
/** @} */

/**
 * @name INET->RF per-source spacing
 * @brief Accepted range and factory default for
 * ::app_config_t::inet2rf_min_interval_sec.
 *
 * The APRS-IS feed can offer traffic far faster than a 1200 Bd channel clears
 * it: one 120-byte frame occupies the air for about a second, while a single
 * server-side subscription term can deliver tens of lines per second. This
 * spacing bounds how often any one source callsign may key the transmitter
 * through the gateway, so no single station - and no single injector behind
 * it - can take the channel for itself however the payload-type filter is set.
 *
 * Message traffic is exempt: a conversation is exactly the traffic an IGate
 * exists to carry, and it is already bounded by the message gate's own
 * locally-heard test.
 * @{
 */
#define INET2RF_MIN_INTERVAL_SEC_MIN     0    /**< Shortest accepted spacing; 0 disables the limiter. */
#define INET2RF_MIN_INTERVAL_SEC_MAX     3600 /**< Longest accepted spacing, seconds. */
#define INET2RF_MIN_INTERVAL_SEC_DEFAULT 30   /**< Factory default spacing, seconds. */
/** @} */

/**
 * @brief Number of source callsigns the INET->RF spacing limiter remembers.
 *
 * One slot per callsign gated to RF, reused oldest-first once full. The ring
 * only has to cover the sources active inside one
 * ::app_config_t::inet2rf_min_interval_sec window, which on a channel shared
 * with a gateway's own beacons is a handful of stations; a source pushed out
 * of the ring by a busier one is simply free to transmit again.
 */
#define INET2RF_RATE_RING_SIZE 16

/**
 * @brief Number of addressees remembered for the associated-position rule
 * (see the message gate in aprs_service.c's inet2rfHandler()).
 *
 * Every station this gateway puts a message on the air for takes one slot; the
 * next position report seen for that station on the APRS-IS feed is gated once
 * so the local operator has something to plot, and the slot is released. The
 * ring is deliberately small: it is a courtesy follow-up for conversations
 * happening right now, not a station database.
 */
#define IGATE_MSG_ASSOC_MAX 8

/**
 * @brief Maximum number of entries in the local callsign whitelist/blacklist
 * (see g_config.budlist / aprs_filter_budlist_pass()).
 */
#define IGATE_BUDLIST_MAX 8

/**
 * @brief Maximum number of entries in the satellite/ISS digipeater gate-call
 * list (see g_config.satgate / igateProcess()'s satellite-gate check).
 */
#define IGATE_SATGATE_MAX 8

/**
 * @brief Duplicate-suppression cache bounds shared by the IGate and
 * digipeater ::dup_scope_t windows (see igate.h).
 *
 * These bounds only matter while @c app_config_t.dup_cache_en is set; with it
 * cleared no frame is ever suppressed and neither value is consulted.
 *
 * @c DUP_CACHE_SIZE_MIN/MAX bound @c app_config_t.dup_cache_size (the number
 * of recent frames kept) and @c DUP_CACHE_TIMEOUT_MS_MIN/MAX bound
 * @c app_config_t.dup_cache_timeout_ms (the window, in milliseconds, after
 * which an entry stops counting as a duplicate). The cache array itself is
 * still allocated at the fixed compile-time capacity DUP_CACHE_SIZE_MAX (see
 * igate.c); dup_cache_size only selects how much of that capacity is
 * actually used at runtime.
 * @{
 */
#define DUP_CACHE_SIZE_MAX           40     /**< Compile-time capacity of the duplicate cache array (igate.c). */
#define DUP_CACHE_SIZE_MIN           4      /**< Lowest g_config.dup_cache_size accepted from the web form / igate.json. */
#define DUP_CACHE_SIZE_DEFAULT       20     /**< Factory default for g_config.dup_cache_size. */
#define DUP_CACHE_TIMEOUT_MS_MIN     1000   /**< Lowest g_config.dup_cache_timeout_ms accepted from the web form / igate.json. */
#define DUP_CACHE_TIMEOUT_MS_MAX     120000 /**< Highest g_config.dup_cache_timeout_ms accepted from the web form / igate.json. */
#define DUP_CACHE_TIMEOUT_MS_DEFAULT 30000  /**< Factory default for g_config.dup_cache_timeout_ms, in milliseconds. */
/** @} */

/**
 * @brief Per-direction mode for the local callsign whitelist/blacklist
 * (g_config.rf2inet_budlist_mode / g_config.inet2rf_budlist_mode). Composes
 * with (ANDs against) the existing rf2inetFilter/inet2rfFilter payload-type
 * filters: a packet must pass both.
 */
typedef enum {
    BUDLIST_OFF = 0,   /**< Callsign filter disabled for this direction. */
    BUDLIST_WHITELIST, /**< Only callsigns in g_config.budlist[] are allowed through. */
    BUDLIST_BLACKLIST, /**< Callsigns in g_config.budlist[] are blocked; everyone else passes. */
} budlist_mode_t;

/**
 * @name Digipeater alias table
 * @brief Bounds and text conventions for ::app_config_t::digi_alias.
 *
 * The digipeater recognises no path aliases of its own: every alias it honours
 * is a row of this table, which is what makes the New n-N Paradigm's local
 * conventions (a fill-in ``WIDE1-1``, a two-hop ``WIDE2-2``, a regional
 * ``SSn-N``) an operator setting rather than a firmware constant.
 *
 * An alias is written as the repeater callsign without its SSID - the SSID is
 * the hop count @c N and is handled separately - and may contain
 * ::DIGI_ALIAS_WILDCARD in any position, which matches exactly one decimal
 * digit. That is how one row covers a whole family: @c "WIDE#" matches
 * @c WIDE1 through @c WIDE9 but never @c WIDE, @c WIDEN or @c WIDE12, because
 * the match also requires equal length. Rows are consulted in order and the
 * first one that matches wins, so a specific row placed above a wildcard row
 * gives that one alias its own hop limit.
 * @{
 */
#define DIGI_ALIAS_MAX 4 /**< Rows in the digipeater alias table. */
#define DIGI_ALIAS_LEN 7 /**< Storage for one alias: 6 AX.25 callsign characters + NUL. */
#define DIGI_ALIAS_WILDCARD                                                                                                                                    \
    '#'                    /**< Alias character matching exactly one decimal digit. Not a legal AX.25 callsign character, so it can never be ambiguous.        \
                            */
#define DIGI_ALIAS_MAX_N 7 /**< Highest hop limit selectable for one alias row. */
/** @} */

/**
 * @brief How one ::digi_alias_t row is repeated.
 *
 * The distinction is the one the New n-N Paradigm was introduced to make: a
 * traced hop is identifiable afterwards, a flooded hop is not.
 */
typedef enum {
    DIGI_ALIAS_OFF = 0, /**< Row unused: the alias is ignored, exactly as if it were not listed. */
    DIGI_ALIAS_TRACE, /**< Tracing: this station's callsign is inserted ahead of the remaining alias and marked used, so every hop of the path is identifiable.
                         This is what @c WIDEn-N is required to do. */
    DIGI_ALIAS_FLOOD, /**< Flooding: the hop count is decremented without inserting a callsign, so the route cannot be reconstructed. Only appropriate for a
                         regional @c SSn-N alias an operator deliberately runs untraced. */
} digi_alias_mode_t;

/**
 * @brief One digipeater path alias and the rules for repeating it.
 */
typedef struct {
    char alias[DIGI_ALIAS_LEN]; /**< Repeater callsign without SSID, ::DIGI_ALIAS_WILDCARD allowed. Empty disables the row. */
    uint8_t max_n;              /**< Highest hop count honoured for this alias, 1 to ::DIGI_ALIAS_MAX_N. A larger @c N received on air is trapped. */
    uint8_t mode;               /**< ::digi_alias_mode_t for this row. */
} digi_alias_t;

/**
 * @brief How the digipeater treats an explicit path that names this station
 *        further down than the first unused address.
 *
 * Preemptive digipeating (http://www.aprs.org/aprs12/preemptive-digipeating.txt)
 * scans from the first unused address to the end of the path for one of this
 * station's own identities, and repeats the frame on that match instead of
 * waiting to be reached one address at a time. It is what makes an explicit
 * route such as @c WIDE1-1,CITYA,WIDE2-1,CITYB work: without it a digipeater
 * named in such a path simply drops out of it, and the operator is pushed back
 * onto a @c WIDEn-N flood that loads the channel far more heavily.
 *
 * The two indicator modes differ only in what is left of the addresses that
 * were skipped, and neither applies to generic @c XXXXn-N aliases, which the
 * scan never claims.
 */
typedef enum {
    DIGI_PREEMPT_OFF = 0, /**< No scan: only the first unused address can route the frame. */
    DIGI_PREEMPT_DROP, /**< The matched address is moved to the head of the path and everything before it is discarded, so the frame goes out with the shortest
                          path that still describes what is left to do. */
    DIGI_PREEMPT_MARK, /**< The skipped addresses are kept and marked as used, so the path still shows the route that was requested. */
} digi_preempt_mode_t;

/**
 * @brief One stored WiFi station (STA) profile.
 */
typedef struct {
    bool enable;        /**< Whether this STA profile is used. */
    char wifi_ssid[33]; /**< SSID: 32 chars max (IEEE 802.11 SSID limit) + NUL. */
    char wifi_pass[64]; /**< PSK: 63 chars max (WPA/WPA2/WPA3 limit) + NUL. */
} wifi_sta_t;

/**
 * @brief One stored APRS-IS server slot for IGate failover (see
 * ::app_config_t::aprs_server and ::APRS_SERVER_NUM).
 *
 * All slots share the login identity (aprs_mycall/aprs_ssid/aprs_passcode/
 * aprs_filter) - only the destination host/port differs between them, since
 * they represent the same station connecting to alternative APRS-IS servers.
 */
typedef struct {
    bool enable;   /**< Whether this server slot takes part in the failover rotation. A disabled slot is skipped. */
    char host[20]; /**< APRS-IS server hostname or IP address for this slot. */
    uint16_t port; /**< APRS-IS server TCP port for this slot, clamped to ::APRS_PORT_MIN .. ::APRS_PORT_MAX on save and on load. */
} aprs_server_t;

/**
 * @brief The resident application configuration, loaded at boot and edited by
 * the web POST handlers.
 *
 * @details The single ::g_config instance is the live copy every subsystem
 * reads. It persists to one file per web admin functionality (see
 * ::app_config_section_t and app_config_save_sections()). Fields
 * are grouped by web admin page: system/time, "My Station" identity, WiFi,
 * IGate, Digipeater, Tracker, Weather, the AFSK/TNC modem, System/HTTP auth,
 * the audio-modem PTT timing, and Message. Access to string/array fields must
 * be serialized with app_config_lock()/app_config_unlock() (see below).
 *
 * @note Telemetry configuration is deliberately NOT here: it lives in its own
 * /storage/telemetry.json (see telemetry.h). The audio-modem PTT GPIO and its
 * active level are also not here - they are fixed compile-time constants
 * (MODEM_PTT_GPIO / MODEM_PTT_ACTIVE_HIGH); only @c ptt_min_unkey_ms is
 * user-configurable.
 */
/**
 * @brief Which 7-byte APRS Data Extension a fixed-position beacon carries in
 * the slot immediately after the symbol code (APRS101 chapter 7).
 *
 * They are mutually exclusive on air - they all occupy the same slot, the one
 * a moving station uses for CSE/SPD - so the beacon carries at most one of
 * them, selected here and gated by the beacon's own "enable data extension"
 * flag (@c app_config_t.igate_phg_enable for the IGate beacon,
 * @c app_config_t.digi_phg_enable for the digipeater beacon). The tracker
 * beacon has no selector of its own: it carries ::APRS_EXT_PHG alone, gated by
 * @c app_config_t.trk_phg_enable.
 *
 * ::APRS_EXT_DF is the one that is wider than the slot: the DF report of
 * chapter 8 puts its course/speed pair in the slot and appends the bearing
 * and NRQ bytes after it. That is why it, like PHG and DFS, cannot travel in
 * a compressed position report, and why the same chapter transmits it only
 * with the DF symbol (::APRS_DF_SYMBOL_TABLE / ::APRS_DF_SYMBOL_CODE): a
 * receiver seeing any other symbol reads the extra bytes as the start of the
 * comment field. Selecting it for a beacon whose symbol is anything else
 * leaves the slot empty.
 */
typedef enum {
    APRS_EXT_PHG = 0, /**< "PHGphgd": transmitter power, antenna height/gain and directivity. */
    APRS_EXT_RNG = 1, /**< "RNGrrrr": pre-calculated omnidirectional radio range, statute miles. */
    APRS_EXT_DFS = 2, /**< "DFSshgd": Omni-DF signal strength, with the same height/gain/directivity codes as PHG. */
    APRS_EXT_DF = 3, /**< "CSE/SPD/BRG/NRQ": DF report, the bearing to a signal and the NRQ triplet describing it (APRS101 chapter 8); transmitted only with the
                        DF symbol. */
} aprs_ext_type_t;

#define APRS_EXT_RANGE_MILES_MIN  0    /**< Lowest "RNGrrrr" pre-calculated radio range, statute miles. */
#define APRS_EXT_RANGE_MILES_MAX  9999 /**< Highest "RNGrrrr" pre-calculated radio range: the field is 4 digits wide. */
#define APRS_EXT_DFS_STRENGTH_MIN 0    /**< Lowest "DFSshgd" signal-strength code (0 = this station does NOT hear the signal). */
#define APRS_EXT_DFS_STRENGTH_MAX 9    /**< Highest "DFSshgd" signal-strength code, in S-points. */
#define APRS_EXT_DF_BEARING_MIN   0    /**< Lowest DF report bearing, degrees. */
#define APRS_EXT_DF_BEARING_MAX   359  /**< Highest DF report bearing, degrees: the field is three digits and 360 is expressed as 0. */
#define APRS_EXT_DF_NRQ_MIN       0    /**< Lowest value of each DF report NRQ digit. */
#define APRS_EXT_DF_NRQ_MAX       9    /**< Highest value of each DF report NRQ digit: N, R and Q are one decimal digit each. */

/**
 * @brief Highest beacons-per-hour value the single-character PHGR "probes"
 * rate field can carry (1.2 addition, aprs.org/aprs12/probes.txt): '0'-'9'
 * for 0-9, then 'A' upward for 10 and above, up to 'Z' for this value. A
 * beacon cadence that would compute to a higher rate is clamped to this
 * ceiling rather than wrapped into an unrelated byte.
 */
#define APRS_EXT_PHG_RATE_MAX 35

/**
 * @brief Highest position-ambiguity level selectable on the Station page
 * (0 = full precision, 4 = nearest degree). Mirrors
 * ::APRS_COORD_AMBIGUITY_MAX, kept here so the web page and the JSON clamp
 * do not have to pull in aprs_coord.h.
 */
#define POS_AMBIGUITY_MAX 4

/**
 * @name Meteor-scatter beam heading and ERP (APRS101 chapter 16)
 *
 * The two characters a status report may carry after a @c '^' as its last
 * field: the beam heading in units of 10 degrees, and a code standing for the
 * effective radiated power. Both halves have to be configured for the block to
 * be emitted at all - a heading with no power, or the reverse, says nothing.
 * @{
 */
#define STATUS_BEAM_DEG_OFF                                                                                                                                    \
    (-1) /**< ::app_config_t::status_beam_deg value meaning "no beam heading configured": 0 degrees is itself a legal heading, so "off" needs a value of its   \
            own. */
#define STATUS_BEAM_DEG_MAX  350 /**< Highest beam heading the single character can encode ('Z'); the field steps in ::STATUS_BEAM_DEG_STEP degrees. */
#define STATUS_BEAM_DEG_STEP 10  /**< Beam-heading quantisation: the character carries the heading divided by ten. */

#define STATUS_ERP_CODE_MIN   1    /**< Lowest ERP code in the chapter 16 table, character '1', standing for 10 W. */
#define STATUS_ERP_CODE_MAX   27   /**< Highest ERP code in the chapter 16 table, character 'K', standing for 7290 W. */
#define STATUS_ERP_WATTS_STEP 10   /**< Multiplier of the ERP table: the power is this many watts times the square of the code. */
#define STATUS_ERP_WATTS_MAX  7290 /**< Highest ERP the table can express, i.e. ::STATUS_ERP_WATTS_STEP times the square of ::STATUS_ERP_CODE_MAX. */
/** @} */

/**
 * @brief The whole runtime configuration of the station, in one structure.
 *
 * A single instance, ::g_config, is the live copy every subsystem reads. It is
 * populated at boot by app_config_load() - defaults first, then whatever the
 * section files override - and rewritten field by field by the web admin's
 * POST handlers, which call app_config_save_section() to persist the file they
 * edited.
 *
 * The fields are grouped in the order the web admin presents them: system and
 * "My Station" identity first, then one block per service (IGate, BrandMeister,
 * Digipeater, Tracker, Weather, Telemetry, GPS, Telegram, Winlink), then the
 * radio/modem and wireless settings. Each field's own comment names the JSON
 * key it persists under and the page it is edited on.
 *
 * @note Not every setting the firmware uses lives here: values that are board
 *       wiring rather than operator choices are compile-time constants (the
 *       modem's ADC/DAC/PTT pins, the sensor I2C bus, the GNSS UART), and the
 *       telemetry, bulletin and object/item sets have their own files and
 *       structures.
 *
 * @note Readers that need a consistent view across several fields must take
 *       ::app_config_lock, since a web save rewrites fields in place from the
 *       httpd task while the service tasks are reading them.
 */
typedef struct {
    bool synctime;        /**< Enable SNTP time sync. */
    uint8_t cpuFreq;      /**< CPU clock frequency selection (80/160/240 MHz); see cpu_freq.h. */
    uint8_t timezone_idx; /**< Selected entry in the built-in timezone table (see ::time_sync_tz_t / time_sync_tz_count() in time_sync.h), used only to
                             render local date/time in the web admin (System page select, dashboard). The system clock itself (time(NULL)/gmtime_r())
                             stays UTC everywhere else in the firmware; see time_sync.h. */

    char my_callsign[10]; /**< "My Station" callsign, entered once on the Station page and reused by every page's "Use My Station Data". */
    bool my_use_gps;      /**< "Use GPS": mirror the live GNSS fix into my_lat/my_lon/my_alt on every save and lock those fields against manual editing. */
    float my_lat;         /**< "My Station" latitude, decimal degrees. APRS defines no on-air "position unknown" coordinate, so this project treats the exact
                             pair (0.0, 0.0) - Null Island, not a real amateur station site - as its own convention for "not yet configured": every
                             position report built from it (buildPositionPacket() in beacon.c) and the Maidenhead locator of a status report
                             (buildStatusPacket()) is withheld while both my_lat and my_lon, or the per-service position that mirrors them, are still at
                             that default, rather than putting a false fix in the Gulf of Guinea on the air. Set this, or enable "Use GPS", before enabling
                             any beacon. */
    float my_lon;         /**< "My Station" longitude, decimal degrees. Same 0.0 default and the same "not yet configured" convention as
                             ::app_config_t::my_lat. */
    float my_alt;         /**< "My Station" altitude. */

    uint16_t my_phg_power;  /**< "My Station" PHG sub-field: radio TX power, Watts (persisted so the form redisplays the selections). */
    float my_phg_gain;      /**< "My Station" PHG sub-field: antenna gain, dBi. */
    uint16_t my_phg_height; /**< "My Station" PHG sub-field: antenna height. Stored in feet (the unit the APRS PHG code table itself is defined in); the Station
                               page displays/edits this in meters and converts. */
    uint8_t my_phg_dir;     /**< "My Station" PHG sub-field: directivity, 0=Omni, 1-8 = N,NE,E,SE,S,SW,W,NW. */

    uint8_t pos_ambiguity;    /**< Position ambiguity applied to every uncompressed own-station position report, 0 (full precision) to ::POS_AMBIGUITY_MAX
                                 (nearest degree). See aprs_coord_format_ambiguous(). */
    bool status_grid_en;      /**< Prefix every own-station status report with the Maidenhead grid locator of the beacon's position, its symbol table byte
                                 and its symbol code, immediately after the '>' data type identifier (APRS101 chapter 16). Takes precedence over
                                 ::status_timestamp_en: the spec allows only one of the two leading fields, so when both are set the timestamp is left
                                 out of the report. */
    bool status_timestamp_en; /**< Prefix every own-station status report with the optional "DDHHMMz" zulu timestamp (APRS101 chapter 16), immediately
                                 after the '>' data type identifier, unless ::status_grid_en is also set, in which case the grid locator is sent instead. */
    int16_t
        status_beam_deg; /**< Beam heading advertised at the end of every own-station status report, degrees, quantised to ::STATUS_BEAM_DEG_STEP and at most
                            ::STATUS_BEAM_DEG_MAX; ::STATUS_BEAM_DEG_OFF leaves the block out. Paired with ::status_erp_watts - the block needs both. */
    uint16_t status_erp_watts; /**< Effective radiated power advertised alongside ::status_beam_deg, watts, rounded to the nearest entry of the APRS101 chapter
                                  16 table (::STATUS_ERP_WATTS_STEP times the square of a code of 1 to ::STATUS_ERP_CODE_MAX); 0 leaves the block out. */
    bool my_no_archive;        /**< Prepend the APRS-IS "!x!" no-archive marker (APRS101 ch.17) to every own-station free-text field this station
                                  originates - Tracker / IGate / Digipeater position comments and status texts, the weather report comment, object and
                                  item comments and bulletin text - asking the databases behind APRS-IS not to store those packets. A station-wide
                                  privacy choice rather than a per-service one, so it lives here next to the other station-wide reporting fields, and
                                  every originator applies it through the one shared builder, aprs_free_text_build() in `main/include/aprs_free_text.h`.
                                  Message text, telemetry definition packets and query responses are deliberately outside its reach: the first is text a
                                  correspondent reads in a message addressed to them, the second is fixed-layout metadata with no free-text slot, and the
                                  third answers another station's question rather than reporting this station. Purely advisory to the archives: it does
                                  not withhold a packet from RF or from APRS-IS itself, and packets this station relays are passed through unchanged
                                  regardless of this setting - a relayed frame's marker, if any, is the originating station's own choice. */
    bool pos_dao_en; /**< Append the WGS-84 human-readable "!DAO!" precision/datum extension (aprs12/datum.txt) to every uncompressed own-station position
                        report and to the Mic-E text field, recovering the third decimal minute digit of latitude/longitude that the plain
                        "DDMM.mmN"/"DDDMM.mmW" fields and the Mic-E position bytes stop short of. See aprs_dao_build(). Only applied when pos_ambiguity is 0:
                        a station deliberately obscuring its position must not have that precision handed back via the extension. Never applied to the
                        compressed layout, which already carries full resolution. */

    uint8_t wifi_mode;                 /**< Which WiFi interfaces to bring up: one of the ::WIFI_MODE_CFG_OFF .. ::WIFI_MODE_CFG_APSTA selectors. */
    int8_t wifi_power;                 /**< WiFi transmit power in dBm, clamped to ::WIFI_TX_POWER_DBM_MIN .. ::WIFI_TX_POWER_DBM_MAX on save and on load. */
    wifi_sta_t wifi_sta[WIFI_STA_NUM]; /**< The ::WIFI_STA_NUM stored STA profiles. */
    uint8_t wifi_ap_ch;                /**< SoftAP channel, clamped to ::WIFI_AP_CH_MIN .. ::WIFI_AP_CH_MAX on save and on load. */
    char wifi_ap_ssid[33];             /**< SoftAP SSID: 32 chars max + NUL. */
    char wifi_ap_pass[64];             /**< SoftAP PSK: 63 chars max + NUL. */

    bool igate_en;                       /**< IGate service enabled. */
    bool rf2inet;                        /**< Gateway RF -> APRS-IS. */
    bool inet2rf;                        /**< Gateway APRS-IS -> RF. */
    bool igate_loc2rf;                   /**< Beacon the IGate's own position on RF. */
    bool igate_loc2inet;                 /**< Beacon the IGate's own position to APRS-IS. */
    uint16_t rf2inetFilter;              /**< RF->INET payload-type filter (IGATE_FILT_* bitmask). */
    uint16_t inet2rfFilter;              /**< INET->RF payload-type filter (IGATE_FILT_* bitmask). */
    budlist_mode_t rf2inet_budlist_mode; /**< RF->INET local callsign whitelist/blacklist mode. */
    budlist_mode_t inet2rf_budlist_mode; /**< INET->RF local callsign whitelist/blacklist mode. */
    char budlist[IGATE_BUDLIST_MAX][10]; /**< Shared callsign list (base call, no SSID) used by both directions' whitelist/blacklist. */

    char satgate[IGATE_SATGATE_MAX][10]; /**< Satellite/ISS digipeater gate-call list (base call, no SSID) checked against the repeater path in igateProcess();
                                            an empty slot is simply skipped. Web-configurable (IGate page, parallel to budlist); the factory default fills
                                            the first six slots with the common amateur satellite digipeater calls. */
    bool dup_cache_en;                   /**< Duplicate suppression enabled (IGate RF->INET and digipeater RF->RF alike). When false,
                                            isDuplicatePacketScoped() never reports a duplicate, never records a frame, and dup_cache_size /
                                            dup_cache_timeout_ms are ignored. Factory default true. */
    uint8_t dup_cache_size;              /**< Number of recent frames kept for duplicate suppression (shared by every ::dup_scope_t). Clamped to
                                            DUP_CACHE_SIZE_MIN..DUP_CACHE_SIZE_MAX; see igate.c. */
    uint32_t dup_cache_timeout_ms;       /**< Duplicate-suppression window, in milliseconds. Clamped to DUP_CACHE_TIMEOUT_MS_MIN..DUP_CACHE_TIMEOUT_MS_MAX;
                                            see igate.c. */

    bool rf2inet_range_en;  /**< Enable the local RF->INET range gate (see aprs_filter_haversine_km()). Independent of, and composed with (AND semantics),
                               rf2inetFilter/the budlist. */
    float rf2inet_range_km; /**< Max allowed distance from "My Station" (my_lat/my_lon), km. 0 = unlimited (gate has no effect even if enabled). Packets whose
                               position can't be decoded are not evaluated (pass this check). */
    bool rf2inet_prefix_en; /**< Enable the local RF->INET callsign-prefix gate. */
    char rf2inet_prefixes[40]; /**< Comma-separated callsign-prefix whitelist for rf2inet_prefix_en, e.g. "EA,EB,EC". Case-insensitive. */

    bool inet2rf_range_en;  /**< Enable the local INET->RF range gate, the mirror image of @c rf2inet_range_en. Independent of, and composed with (AND
                               semantics), inet2rfFilter/the budlist. Required before any worldwide subscription (such as the BrandMeister monitor term) may
                               be gated to the transmitter: APRS-IS server filter terms are OR'd, never AND'd, so a range restriction cannot be expressed
                               server-side alongside one. */
    float inet2rf_range_km; /**< Max allowed distance from "My Station" (my_lat/my_lon), km. 0 = unlimited (gate has no effect even if enabled). Clamped to
                               ::APRS_RANGE_KM_MIN .. ::APRS_RANGE_KM_MAX. Lines whose position can't be decoded carry no distance to measure and are
                               governed by @c inet2rf_position_required instead. */
    bool inet2rf_position_required;    /**< On by default. Refuse any non-message INET->RF line that carries no decodable position of its own - a status report,
                                          a telemetry frame, an unclassifiable payload. Independent of @c inet2rf_range_en, and the one gate that bounds a
                                          server-side subscription whose terms reach past the local area: APRS-IS filter terms are OR'd, never AND'd, so a
                                          traffic-class term such as the BrandMeister worldwide monitor (::APRS_BM_MONITOR_FILTER_TERM) delivers position-less
                                          lines from the whole network that no geographic term ever narrowed. Message traffic is exempt - a message has no
                                          position of its own and is gated on its addressee instead. */
    bool inet2rf_heard_only;           /**< On by default. Gate a non-message INET->RF line only when its source callsign was itself heard on the local RF
                                          channel inside @c igate_local_window_sec, which is the same test the message gate applies to an addressee. Traffic
                                          from a station nobody in earshot has ever heard is traffic the local channel has no use for. Message traffic is
                                          exempt: its own gate already tests the addressee. */
    uint16_t inet2rf_min_interval_sec; /**< Shortest interval between two non-message INET->RF frames gated for the same source callsign, seconds; 0 disables
                                          the limiter. Clamped to ::INET2RF_MIN_INTERVAL_SEC_MIN .. ::INET2RF_MIN_INTERVAL_SEC_MAX on save and on load.
                                          Message traffic is exempt. */

    bool bm_en;            /**< BrandMeister interconnect enabled (web admin "BrandMeister" page). Master switch: with it off, no line is classified, no BM
                              marker is recorded and message routing is untouched. Purely an APRS-IS feature - nothing here opens a DMR connection. */
    bool bm_monitor;       /**< Operator intends to run the worldwide BrandMeister monitor subscription (::APRS_BM_MONITOR_FILTER_TERM in the IGate server
                              filter). Refused by the page while @c inet2rf is on and @c inet2rf_range_en is off. */
    bool bm_msg_inet_only; /**< On by default. Send a message addressed to a station last heard as BrandMeister traffic over APRS-IS only, never on RF: such a
                              station is reachable through the network, not on the local channel. May only ever remove the RF leg, never add the Internet one.
                            */
    char bm_gateways[APRS_BM_GATEWAYS_MAX][APRS_BM_GATEWAY_LEN]; /**< Optional BrandMeister gateway/master callsigns matched against the entry station after
                                                                    the q construct (third classifier test, see aprs_bm.h). A trailing '*' matches by prefix;
                                                                    an empty list skips the test, which is the factory state. */

    bool igate_msg_gate_en;          /**< On by default. Apply the APRS-IS message-gating criteria before putting a message read from APRS-IS on the air: the
                                        addressee must have been heard on RF inside @c igate_local_window_sec over at most @c igate_msg_max_hops digipeater
                                        hops, the sender must not have been heard on RF, the sender's header must carry no TCPXX/NOGATE/RFONLY, and the
                                        addressee must not be Internet-connected. */
    uint16_t igate_local_window_sec; /**< How far back the message gate looks in the last-heard table, seconds. Clamped to ::IGATE_LOCAL_WINDOW_SEC_MIN ..
                                        ::IGATE_LOCAL_WINDOW_SEC_MAX on save and on load. */
    uint8_t igate_msg_max_hops;      /**< Longest path, in used digipeater addresses, over which the message gate still counts an addressee as reachable from
                                        here; 0 gates only to stations heard direct. Clamped to ::IGATE_MSG_MAX_HOPS_MIN .. ::IGATE_MSG_MAX_HOPS_MAX on save
                                        and on load, and defaulted to the hop count of the IGate transmit path. */
    bool inet2rf_3rdparty_unwrap_en; /**< Off by default. Selective INET->RF opt-in: unwrap one level of third-party ('}') traffic and re-classify/relay the
                                        inner packet, but ONLY when inet2rf_budlist_mode is BUDLIST_WHITELIST and the inner packet's source callsign is itself
                                        on budlist[] - see aprs_filter_classify_thirdparty_inner(). Never a general "relay all third-party" switch; misuse (or
                                        use without a whitelist) risks re-introducing an IGate loop. */
    uint8_t aprs_ssid;               /**< SSID for the IGate callsign. */
    char aprs_mycall[10];            /**< IGate callsign. */
    bool igate_use_station;          /**< "Use My Station Data": mirror My Station identity/position into the IGate fields and lock them. */
    bool igate_use_gps;              /**< "Use GPS": mirror the live GNSS fix into igate_lat/igate_lon/igate_alt on every save and lock those fields against
                                        manual editing. Mutually exclusive with igate_use_station on the page itself; both write the same three fields. */
    aprs_server_t aprs_server[APRS_SERVER_NUM]; /**< The ::APRS_SERVER_NUM stored APRS-IS server slots the IGate task fails over between; see igate.c. */
    char aprs_passcode[6];                      /**< APRS-IS login passcode. */
    char aprs_filter[128];                      /**< APRS-IS server-side filter string. Sized for several terms at once: a single range or area term already
                                                    runs past 20 characters, and a subscription that names both a local radius and a traffic class needs two
                                                    or three of them. See aprs_filter_validate_server_string(). */
    bool igate_log_after_filters;               /**< Off by default. Log display gate: while set, the "RX" and "RX-IS" entries of the web traffic log and their
                                                    matching serial console lines are only emitted for a frame/line that passes this station's own IGate
                                                    filters - the Satellite Gate List and the RF->INET set (type mask, range, prefix) plus the Callsign Filter
                                                    for RF, the INET->RF set (type mask, range) plus the Callsign Filter for APRS-IS - instead of every frame
                                                    received. Purely a display choice: a frame left out of both views is still digipeated, gated, parsed and
                                                    counted exactly as it is with this option off. See igate_log_accepts_frame() / igate_log_accepts_line(). */
    bool igate_bcn;                             /**< Enable the IGate position beacon. */
    bool igate_timestamp;                       /**< Include a timestamp in the IGate beacon. */
    float igate_lat;                            /**< IGate beacon latitude. Same "not yet configured" convention as ::app_config_t::my_lat: while
                                                    igate_lat/igate_lon are still (0.0, 0.0), the IGate position beacon and the Maidenhead locator of its
                                                    status report are withheld rather than sent. */
    float igate_lon;                            /**< IGate beacon longitude. See ::app_config_t::igate_lat. */
    float igate_alt;                            /**< IGate beacon altitude. */
    uint16_t igate_interval;                    /**< IGate beacon interval, seconds. */
    char igate_symbol[3];                       /**< IGate APRS symbol ("<table><code>" + NUL). */
    uint8_t igate_path;                         /**< IGate digipeat-path selection (bitmask over g_config.path[0..3]). */
    char igate_comment[COMMENT_SIZE];           /**< IGate beacon comment. */
    uint16_t igate_sts_interval;                /**< IGate status-beacon interval, seconds. */
    char igate_status[STATUS_SIZE];             /**< IGate status text. */
    bool igate_compress;                        /**< Use APRS compressed position format for the IGate position beacon. */
    bool igate_phg_enable;                      /**< Enable transmitting the PHG data extension in the IGate position beacon. */
    bool igate_phg_use_station; /**< "Use My Station Data": mirror the shared "My Station" PHG sub-fields into the IGate PHG fields and lock them. */
    uint16_t igate_phg_power;   /**< PHG sub-field: radio TX power, Watts (persisted so the form redisplays the selections). */
    float igate_phg_gain;       /**< PHG sub-field: antenna gain, dBi. */
    uint16_t igate_phg_height;  /**< PHG sub-field: antenna height, feet. */
    uint8_t igate_phg_dir;      /**< PHG sub-field: directivity, 0=Omni, 1-8 = N,NE,E,SE,S,SW,W,NW. */
    uint8_t igate_ext_type;     /**< Which ::aprs_ext_type_t the IGate position beacon carries when @c igate_phg_enable is set. */
    uint16_t igate_range_miles; /**< "RNGrrrr" pre-calculated radio range, statute miles (::APRS_EXT_RNG only). */
    uint8_t igate_dfs_strength; /**< "DFSshgd" signal-strength code 0-9 (::APRS_EXT_DFS only; height/gain/directivity come from the PHG sub-fields). */
    uint16_t igate_df_bearing;  /**< DF report bearing to the signal, degrees (::APRS_EXT_DF only). */
    uint8_t igate_df_nrq_n;     /**< DF report N digit: 0 = the NRQ triplet carries no meaning, 1-8 = relative number of hits per sampling period, 9 = manual
                                    report (::APRS_EXT_DF only). */
    uint8_t igate_df_nrq_r;     /**< DF report R digit: range code, standing for 2^R miles (::APRS_EXT_DF only). */
    uint8_t igate_df_nrq_q;     /**< DF report Q digit: bearing accuracy, 0 (useless) through 9 (better than one degree) (::APRS_EXT_DF only). */

    float igate_freq_mhz;       /**< Recommended travelers' voice repeater frequency this digipeater advertises, MHz; 0 => no frequency block emitted. Built
                                   with objitem_build_freq_block() and prepended as the first 10 bytes of the IGate beacon comment (freqspec.txt); the same
                                   block is also carried in the IGate status report, the spec's documented fallback for radios that decode neither the
                                   frequency Object form nor a position comment. */
    uint16_t igate_tone_tenths; /**< Repeater CTCSS subaudible tone, tenths of Hz (e.g. 1000 = 100.0 Hz); 0 => "Toff". */
    int8_t igate_duplex;        /**< Repeater duplex direction: 0 = simplex (offset omitted), +1 = "+", -1 = "-". */
    uint16_t igate_offset_khz;  /**< Repeater duplex shift magnitude, kHz (e.g. 600); used only when igate_duplex != 0. */

    bool digi_en;                            /**< Digipeater service enabled. */
    bool digi_loc2rf;                        /**< Beacon the digipeater's own position on RF. */
    bool digi_loc2inet;                      /**< Beacon the digipeater's own position to APRS-IS. */
    bool digi_timestamp;                     /**< Include a timestamp in the digipeater beacon. */
    uint8_t digi_ssid;                       /**< SSID for the digipeater callsign. */
    char digi_mycall[10];                    /**< Digipeater callsign. */
    bool digi_use_station;                   /**< "Use My Station Data": mirror My Station into the digipeater fields and lock them. */
    bool digi_use_gps;                       /**< "Use GPS": mirror the live GNSS fix into digi_lat/digi_lon/digi_alt on every save and lock those fields
                                                against manual editing. Mutually exclusive with digi_use_station on the page itself; both write the same
                                                three fields. */
    uint8_t digi_path;                       /**< Digipeater beacon digipeat-path selection (bitmask over g_config.path[0..3]). */
    digi_alias_t digi_alias[DIGI_ALIAS_MAX]; /**< The only path aliases this digipeater honours; see ::digi_alias_t. */
    bool digi_fillin_only;                   /**< Fill-in (home) digipeater role: honour only single-hop rows, so the station serves stations that cannot reach
                                                the backbone directly and leaves multi-hop traffic to the wide digipeaters. */
    bool digi_trap_n_clamp;                  /**< What to do with a hop count above the matched row's @c max_n: true clamps it down to @c max_n and repeats,
                                                false drops the frame (@c DROP_DIGI_N_TRAPPED). */
    bool digi_dest_ssid_en;                  /**< Honour the pre-New-N convention that carries the hop count in the AX.25 destination SSID (1-7) instead of in
                                                the path. Off by default: it repeats on the strength of that SSID alone, ahead of and instead of the operator's
                                                alias table, so it is only appropriate where a legacy neighbour still needs it. */
    uint8_t digi_preempt;                    /**< ::digi_preempt_mode_t: whether the path is scanned past its first unused address for one of this station's own
                                                identities, and what is left of the addresses skipped when it is. ::DIGI_PREEMPT_OFF by default. */
    bool digi_bcn;                           /**< Enable the digipeater position beacon. */
    bool digi_compress;                      /**< Use APRS compressed position format for the digipeater position beacon. */
    float digi_lat;                          /**< Digipeater beacon latitude. Same "not yet configured" convention as ::app_config_t::my_lat: while
                                                digi_lat/digi_lon are still (0.0, 0.0), the Digipeater position beacon and the Maidenhead locator of its
                                                status report are withheld rather than sent. */
    float digi_lon;                          /**< Digipeater beacon longitude. See ::app_config_t::digi_lat. */
    float digi_alt;                          /**< Digipeater beacon altitude. */
    uint16_t digi_interval;                  /**< Digipeater beacon interval, seconds. */
    char digi_symbol[3];                     /**< Digipeater APRS symbol. */
    char digi_comment[COMMENT_SIZE];         /**< Digipeater beacon comment. */
    uint16_t digi_sts_interval;              /**< Digipeater status-beacon interval, seconds. */
    char digi_status[STATUS_SIZE];           /**< Digipeater status text. */

    bool digi_phg_enable;      /**< Enable transmitting a data extension in the digipeater position beacon; @c digi_ext_type picks which one. PHG is the
                                  extension a digipeater is expected to publish (APRS101 chapter 7), since it is the coverage circle other stations reason
                                  about when they choose a path. */
    bool digi_phg_use_station; /**< "Use My Station Data": mirror the shared "My Station" PHG sub-fields into the digipeater PHG fields and lock them. */
    uint16_t digi_phg_power;   /**< PHG sub-field: radio TX power, Watts (persisted so the form redisplays the selections). */
    float digi_phg_gain;       /**< PHG sub-field: antenna gain, dBi. */
    uint16_t digi_phg_height;  /**< PHG sub-field: antenna height, feet. */
    uint8_t digi_phg_dir;      /**< PHG sub-field: directivity, 0=Omni, 1-8 = N,NE,E,SE,S,SW,W,NW. */
    uint8_t digi_ext_type;     /**< Which ::aprs_ext_type_t the digipeater position beacon carries when @c digi_phg_enable is set. */
    uint16_t digi_range_miles; /**< "RNGrrrr" pre-calculated radio range, statute miles (::APRS_EXT_RNG only). */
    uint8_t digi_dfs_strength; /**< "DFSshgd" signal-strength code 0-9 (::APRS_EXT_DFS only; height/gain/directivity come from the PHG sub-fields). */
    uint16_t digi_df_bearing;  /**< DF report bearing to the signal, degrees (::APRS_EXT_DF only). */
    uint8_t digi_df_nrq_n;     /**< DF report N digit: 0 = the NRQ triplet carries no meaning, 1-8 = relative number of hits per sampling period, 9 = manual
                                   report (::APRS_EXT_DF only). */
    uint8_t digi_df_nrq_r;     /**< DF report R digit: range code, standing for 2^R miles (::APRS_EXT_DF only). */
    uint8_t digi_df_nrq_q;     /**< DF report Q digit: bearing accuracy, 0 (useless) through 9 (better than one degree) (::APRS_EXT_DF only). */

    float digi_freq_mhz;       /**< Recommended travelers' voice repeater frequency this digipeater advertises, MHz; 0 => no frequency block emitted. See
                                  igate_freq_mhz; freqspec.txt calls this out as specifically the digipeater's responsibility. */
    uint16_t digi_tone_tenths; /**< Repeater CTCSS subaudible tone, tenths of Hz; 0 => "Toff". */
    int8_t digi_duplex;        /**< Repeater duplex direction: 0 = simplex, +1 = "+", -1 = "-". */
    uint16_t digi_offset_khz;  /**< Repeater duplex shift magnitude, kHz; used only when digi_duplex != 0. */

    bool trk_en;           /**< Tracker service enabled. */
    bool trk_loc2rf;       /**< Beacon the tracker position on RF. */
    bool trk_loc2inet;     /**< Beacon the tracker position to APRS-IS. */
    bool trk_timestamp;    /**< Include a timestamp in the tracker beacon. */
    uint8_t trk_ssid;      /**< SSID for the tracker callsign. */
    char trk_mycall[10];   /**< Tracker callsign. */
    bool trk_use_station;  /**< "Use My Station Data": mirror My Station into the tracker fields and lock them. */
    bool trk_use_gps;      /**< "Use GPS": mirror the live GNSS fix into trk_lat/trk_lon/trk_alt on every save and lock those fields against manual editing.
                              Mutually exclusive with trk_use_station on the page itself; both write the same three fields. */
    bool trk_use_live_gps; /**< "Use live GPS fix": read the GNSS receiver at every beacon transmission instead of at save time. When set and
                              ::gps_snapshot reports a valid fix, the tracker beacon carries the live latitude/longitude/altitude/course/speed instead of
                              trk_lat/trk_lon/trk_alt; a disabled receiver or a momentary loss of fix falls back to those fixed values for that beacon,
                              same as when this is off. Independent of trk_use_gps, which only copies the fix into the fixed fields once, on save. */
    uint8_t trk_path;      /**< Tracker digipeat-path selection (bitmask over g_config.path[0..3]). */
    float trk_lat;         /**< Tracker beacon latitude. Same "not yet configured" convention as ::app_config_t::my_lat, applied to whichever position the
                              beacon actually transmits: the live GNSS fix while trk_use_live_gps is on and current, this fixed value otherwise. While that
                              position is (0.0, 0.0), the Tracker position beacon and the Maidenhead locator of its status report are withheld rather than
                              sent. */
    float trk_lon;         /**< Tracker beacon longitude. See ::app_config_t::trk_lat. */
    float trk_alt;         /**< Tracker beacon altitude. */
    uint16_t trk_interval; /**< Fixed tracker beacon period in seconds (see beacon.c). */
    bool trk_compress;     /**< Use APRS compressed position format. */
    bool trk_altitude;     /**< Include altitude in the beacon. */
    bool trk_phg_enable;   /**< Carry the "PHGphgd" data extension in the tracker beacon, built from the station-wide @c my_phg_* antenna data. In the Mic-E
                                layout the token rides in the text field, which is where APRS 1.2 puts an ordinary position comment field. */
    bool trk_mice;         /**< Use Mic-E position encoding (APRS101 ch.10) instead of uncompressed/compressed; excludes trk_timestamp. */
    uint8_t trk_mice_msg;  /**< Mic-E position comment: 0-6 = Standard M0-M6, 7-13 = Custom C0-C6. See ::MICE_POS_COMMENT_MAX. */
    char trk_symbol[3];    /**< Tracker APRS symbol. */
    char trk_comment[COMMENT_SIZE]; /**< Tracker beacon comment. */
    uint16_t trk_sts_interval;      /**< Tracker status-beacon interval, seconds. */
    char trk_status[STATUS_SIZE];   /**< Tracker status text. */

    float trk_freq_mhz;       /**< Recommended travelers' voice repeater frequency this station advertises, MHz; 0 => no frequency block emitted. See
                                 igate_freq_mhz. */
    uint16_t trk_tone_tenths; /**< Repeater CTCSS subaudible tone, tenths of Hz; 0 => "Toff". */
    int8_t trk_duplex;        /**< Repeater duplex direction: 0 = simplex, +1 = "+", -1 = "-". */
    uint16_t trk_offset_khz;  /**< Repeater duplex shift magnitude, kHz; used only when trk_duplex != 0. */

    bool trk_sb_enable; /**< Enable SmartBeaconing (Hans-Gunnar Lundahl / HamHUD algorithm): the Tracker beacon interval varies between trk_sb_slow_interval
                              and trk_sb_fast_interval with current speed, and a heading change beyond the corner-pegging threshold forces an early beacon.
                              Only has an effect while trk_use_live_gps is also set - SmartBeaconing has no speed/course input without a live GNSS fix, and
                              falls back to the fixed trk_interval cadence whenever one is not currently available. See trackerBeaconService() in
                              main/beacon.c. */
    uint16_t trk_sb_slow_interval;  /**< SmartBeaconing slow-rate interval, seconds: the beacon period used at or below trk_sb_low_speed_kmh (including
                                          stationary). */
    uint16_t trk_sb_fast_interval;  /**< SmartBeaconing fast-rate interval, seconds: the beacon period used at or above trk_sb_high_speed_kmh. */
    uint16_t trk_sb_low_speed_kmh;  /**< SmartBeaconing low-speed threshold, km/h: at or below this speed the interval is trk_sb_slow_interval. */
    uint16_t trk_sb_high_speed_kmh; /**< SmartBeaconing high-speed threshold, km/h: at or above this speed the interval is trk_sb_fast_interval. Between the
                                          two thresholds the interval is linearly interpolated. */
    uint16_t trk_sb_turn_angle;     /**< SmartBeaconing corner-pegging minimum turn angle, degrees: the heading change (at or above the high-speed threshold)
                                          that forces an early beacon. */
    uint16_t trk_sb_turn_slope;     /**< SmartBeaconing corner-pegging turn slope, degrees: added to trk_sb_turn_angle, scaled inversely with current speed, so
                                          the effective turn threshold widens at low speed - see the corner-pegging note in beacon.c. */
    uint16_t trk_sb_min_turn_time;  /**< SmartBeaconing minimum turn time, seconds: the shortest gap allowed between two corner-pegged beacons, so a
                                          stationary or slow-moving station with a noisy course reading cannot re-trigger corner-pegging every pass. */

    bool gps_en; /**< GNSS receiver enabled. When false the receiver's UART is never installed, the reader task does not run and every consumer of
                      ::gps_snapshot sees "no receiver". This is the single switch the rest of the firmware tests before using anything the module reports. */

    bool wx_en;                           /**< Weather service enabled. */
    bool wx_2rf;                          /**< Transmit the WX report on RF. */
    bool wx_2inet;                        /**< Transmit the WX report to APRS-IS. */
    bool wx_timestamp;                    /**< Include a timestamp in the WX report. */
    uint8_t wx_ssid;                      /**< SSID for the WX callsign. */
    char wx_mycall[10];                   /**< WX callsign. */
    bool wx_use_station;                  /**< "Use My Station Data": mirror My Station into the WX fields and lock them. */
    bool wx_use_gps;                      /**< "Use GPS": mirror the live GNSS fix into wx_lat/wx_lon on every save and lock those fields against manual
                                             editing. Mutually exclusive with wx_use_station on the page itself; both write the same two fields. */
    uint8_t wx_path;                      /**< WX digipeat-path selection (bitmask over g_config.path[0..3]). */
    float wx_lat;                         /**< WX report latitude. Same "not yet configured" convention as ::app_config_t::my_lat, but the weather report has
                                             a positionless layout to fall back to (build_wx_packet() in weather.c) instead of being withheld outright: while
                                             wx_lat/wx_lon are still (0.0, 0.0) the report carries no position field. */
    float wx_lon;                         /**< WX report longitude. See ::app_config_t::wx_lat. */
    uint16_t wx_interval;                 /**< WX report interval, seconds. */
    char wx_object[10];                   /**< WX object name (if beaconing as an object). */
    char wx_comment[COMMENT_SIZE];        /**< WX report comment. */
    bool wx_sensor_enable[WX_SENSOR_NUM]; /**< Per-field enable, indexed by ::wx_field_id_t. */
    bool wx_sensor_avg[WX_SENSOR_NUM];    /**< Per-field averaging enable, indexed by ::wx_field_id_t. */
    uint8_t wx_sensor_ch[WX_SENSOR_NUM];  /**< Per-field source sensor channel, indexed by ::wx_field_id_t (::SENSOR_LOCAL_CH_NONE = "(none)"); persisted by
                                             driver name. */

    bool audio_modem_en;      /**< Enable the audio ADC/DAC AFSK modem. */
    bool audio_lpf;           /**< Flat (discriminator) audio input. Set when the receive audio comes from a data/discriminator jack, which is unfiltered and
                                 carries no de-emphasis, and cleared when it comes from a speaker or headphone output, which is already de-emphasized. Selects
                                 the prefilter tilt and slicer weight tables of the demodulator presets (see modem_rx_eq_preset_t) and, for the legacy
                                 set, which fixed prefilter demodulator 0 runs. Stored under the JSON key "audioLPF". */
    uint16_t preamble;        /**< TXDelay (preamble) length, ms. */
    uint16_t tx_tail;         /**< TXTail length, ms: how long the transmitter stays keyed, sending flags, after the closing flag of each frame, so the
                                 radio's audio chain and its switch back to receive do not cut the end of the frame. Web-configurable (Radiomodem page),
                                 applied live via aprs_service_apply_modem_config(). Range RF_TX_TAIL_MS_MIN..RF_TX_TAIL_MS_MAX (aprs_service.h), default
                                 RF_TX_TAIL_MS_DEFAULT. Stored under the JSON key "rfTxTail". */
    uint8_t afsk_modem_type;  /**< Audio AFSK modulation (::modem_mode_t: 0=AFSK300, 1=Bell202, 2=V.23, 3=G3RUH); used for both RX and TX. */
    uint8_t fx25_mode;        /**< FX.25 mode: 0=off, 1=RX only, 2=RX+TX. */
    uint16_t tx_timeslot;     /**< CSMA quiet time, ms: how long a queued frame waits before channel access begins at all. The interval between the individual
                                 persistence rolls that follow is csma_slot_ms, not this value. */
    uint16_t csma_slot_ms;    /**< CSMA slot time, ms (standard AX.25/KISS "SlotTime"): the interval between persistence rolls on a clear channel and between
                                 re-checks of a busy one. Web-configurable (Radiomodem page), applied live via aprs_service_apply_modem_config(). Range
                                 CSMA_SLOT_MS_MIN..CSMA_SLOT_MS_MAX (aprs_service.h), default CSMA_SLOT_MS_DEFAULT. Stored under the JSON key "csmaSlotTime". */
    uint16_t csma_busy_max_s; /**< Longest time, s, a queued frame waits for a busy channel to clear before it is transmitted anyway, measured from the first
                                 busy slot; 0 waits for as long as the channel stays busy, as a standard KISS TNC does. A frame sent this way is counted as
                                 the first CSMA figure on the dashboard. Web-configurable (Radiomodem page), applied live. Range
                                 CSMA_BUSY_MAX_S_MIN..CSMA_BUSY_MAX_S_MAX (aprs_service.h), default CSMA_BUSY_MAX_S_DEFAULT. Stored under the JSON key
                                 "csmaBusyMax". */
    uint8_t csma_persist;     /**< CSMA/p-persistent channel-access probability (standard AX.25/KISS "Persist"): once the quiet time has elapsed and the
                                 channel is heard clear, the modem transmits immediately with probability csma_persist/256 on every slot and otherwise waits
                                 one more csma_slot_ms before rolling again. 255 transmits on the first clear slot every time (equivalent to plain
                                 non-persistent CSMA); lower values spread contending stations' key-ups further apart. Eight consecutive missed rolls on a
                                 clear channel transmit anyway so a frame is never held indefinitely, which at the default of 63 happens on roughly one
                                 key-up in ten and is reported as the second CSMA figure on the dashboard. A busy slot restarts that count. Web-configurable
                                 (Radiomodem page, Audio/AFSK section), applied live via aprs_service_apply_modem_config(). Range 1..255. */

    uint8_t rf_tx_buffers; /**< Max frames allowed to sit in the RF TX ring before aprs_service_send_tnc2() starts discarding new packets. Web-configurable and
                              applied live (read on every transmit). Range RF_TX_BUFFERS_MIN..RF_TX_BUFFERS_MAX (aprs_service.h), default 1. */

    bool duty_cycle_en;     /**< Long-term TX duty-cycle limiter enabled. Off by default. When on, aprs_service.c holds back non-critical RF TX (own-station
                                beacons, objects/items, weather, telemetry, bulletins, and the bulk IGate INET->RF relay) once this station's own measured
                                transmit airtime over its rolling window reaches duty_cycle_pct; APRS messages/acks and digipeat repeats are always exempt.
                                Independent of, and in addition to, the CSMA channel-access checks (tx_timeslot/csma_persist above), which only prevent
                                collisions and have no memory of this station's own past transmissions. */
    uint8_t duty_cycle_pct; /**< Duty-cycle ceiling, as a percentage of the rolling window aprs_service.c measures it over, enforced only while
                                duty_cycle_en is on. Web-configurable and applied live (read on every non-critical transmit, no reboot needed). Range
                                DUTY_CYCLE_PCT_MIN..DUTY_CYCLE_PCT_MAX (aprs_service.h), default 25. */

    char ntp_host[NTP_HOST_NUM][20]; /**< Up to ::NTP_HOST_NUM NTP server hostnames. */
    uint16_t ntp_resync_sec;         /**< NTP resync interval, seconds (floored at ::NTP_RESYNC_MIN_SEC). */

    char http_username[32];    /**< Web admin HTTP Basic auth username. Grants the administrator role: every page, every form and every file operation. */
    char http_password[64];    /**< Web admin HTTP Basic auth password, paired with ::app_config_t::http_username. */
    char http_ro_username[32]; /**< Web read-only HTTP Basic auth username, or the empty string when no read-only account exists. Grants the read-only role:
                                  every page renders, no form saves, no file is uploaded or downloaded, and only the log console can be started and stopped. */
    char http_ro_password[64]; /**< Web read-only HTTP Basic auth password, paired with ::app_config_t::http_ro_username. */
    char path[4][72];          /**< The four shared digipeat-path presets selected by the per-service path bitmasks. */

    uint16_t ptt_min_unkey_ms; /**< Extra minimum PTT-off (unkeyed) hold time between transmissions, ms, on top of the fixed one-service-tick (~10 ms) release
                                  the modem always applies. 0 disables the extra hold. Web-configurable and applied live via aprs_service_apply_modem_config().
                                  Range 0..5000 ms. */

    bool adc_self_bias;          /**< Bias the receive audio pin from the ADC pad's own pull-up and pull-down in series, for an AC-coupled input whose interface
                                    carries no bias network. Off by default, which is what an interface board with its own bias divider needs - the internal
                                    pulls would load it. Only GPIO32/33 carry internal pull resistors. Web-configurable (Radiomodem page, Audio interface
                                    section), applied live via aprs_service_apply_modem_config(). */
    bool rx_clip_warn;           /**< Log a rate-limited warning whenever a processed block of receive samples reaches the ends of the ADC's conversion range.
                                    Off by default. Worth enabling on an interface without input clamp diodes, where an over-range block also means the pin is
                                    being driven past the supply rails. Web-configurable and applied live. */
    uint8_t dac_amplitude_pct;   /**< Peak-to-peak swing of the transmit audio output, as a percentage of the full 0..3.3 V range. Web-configurable and applied
                                    live. Range DAC_AMPL_PCT_MIN..DAC_AMPL_PCT_MAX (aprs_service.h), default MODEM_DAC_AMPLITUDE_PCT. The 30 to 40 dB of
                                    attenuation a microphone input needs belongs in an external attenuator: the 8-bit DAC draws a sine period with fewer and
                                    fewer codes as this is lowered. */
    uint32_t dac_samplerate;     /**< Transmit sample rate, Hz: DAC_SAMPLERATE_LOW or DAC_SAMPLERATE_HIGH (aprs_service.h). The higher rate moves the DAC
                                    reconstruction images an octave further from the audio band, which is worth its extra interrupt rate when the interface
                                    carries no reconstruction low-pass filter. Web-configurable, applied at the next reboot: the sample-clock period and every
                                    phase step derived from it are programmed while the modem is stopped. */
    uint32_t tx_max_keyed_ms;    /**< Transmitter time-out, ms, or 0 to disable it. When a key-up lasts longer than this the modem releases PTT, stops the
                                    modulator and discards the transmission, so a stalled transmit path cannot hold the channel. Off by default.
                                    Web-configurable and applied live. Range TX_MAX_KEYED_MS_MIN..TX_MAX_KEYED_MS_MAX (aprs_service.h). */
    modem_rx_tuning_t rx_tuning; /**< Receive-chain tuning: demodulator preset and custom tilts, prefilter band and length, receive gate, high-pass, gain
                                    control and bit repair. Web-configurable (Radiomodem page, Receive demodulator section) and applied live via
                                    aprs_service_apply_modem_config(). Stored in radio.json under the rx* keys and clamped with
                                    modem_rx_tuning_sanitize() on load and on Save; default MODEM_RX_TUNING_DEFAULT(). */

    bool msg_enable;       /**< APRS Message service enabled. */
    char msg_mycall[10];   /**< Message service callsign. */
    bool msg_use_station;  /**< "Use My Station Data": mirror My Station callsign into @c msg_mycall and lock it. */
    uint8_t msg_path;      /**< Message digipeat-path selection (bitmask over g_config.path[0..3]). */
    bool msg_rf;           /**< Send messages on RF. */
    bool msg_inet;         /**< Send messages to APRS-IS. */
    uint8_t msg_retry;     /**< Number of message retries before giving up. */
    uint16_t msg_interval; /**< Message retry interval, seconds. */
    bool msg_alarm_enable; /**< "Message Alarm": drive a GPIO on incoming message (disabled by default). */
    int8_t msg_alarm_gpio; /**< Message-alarm GPIO; -1 = disabled/unset (see message_alarm_gpio_is_valid()). */

    bool wl_enable;              /**< Winlink client enabled. */
    char wl_service_call[10];    /**< APRSLink service callsign the commands are addressed to. Defaults to "WLNK-1". */
    char wl_password[17];        /**< Winlink account password. Never transmitted: only the characters a challenge names are quoted back. */
    bool wl_use_msg_call;        /**< Use @c msg_mycall as the Winlink identity, instead of @c wl_mycall. */
    char wl_mycall[10];          /**< Winlink identity when @c wl_use_msg_call is off. The service keys the mailbox on its base callsign. */
    bool wl_auto_login;          /**< Open a session automatically when a command is queued while idle. */
    uint16_t wl_session_max_min; /**< Local session lifetime, minutes. Kept below the service's own expiry so this station gives a session up first. */
    uint16_t wl_poll_min;        /**< Interval between unprompted listings of pending mail, minutes. 0 never asks. */
    bool wl_comment_en;          /**< Append the Winlink notification marker to the beacon comment, so the service knows this station reads its mail. */
    bool wl_inet_only;           /**< Keep traffic addressed to the service off the air while this station has an APRS-IS uplink. */
    bool wl_gate_exempt;         /**< Let a reply from the service reach RF even when its addressee is also seen on APRS-IS (see messageGatePass()). */

    char msg_group[3][10]; /**< Up to 3 operator-defined message group names (APRS101 ch.14 "Message Groups"), in addition to the built-in "ALL"/"QST"/"CQ"
                               set every station reads. Each slot holds a bare group name, upper case, up to 9 characters wide (the addressee field width);
                               an empty slot ("") is unused. A message addressed to one of these names is stored and shown like any other, but - same as
                               "ALL"/"QST"/"CQ" - is never acknowledged, retransmitted or auto-replied to, since a group name is not this station's own
                               callsign. */

    bool query_en;                   /**< Query responder master enable. */
    bool query_rf;                   /**< Answer queries heard on RF; the answer goes back out on RF. */
    bool query_inet;                 /**< Answer queries read from the APRS-IS feed; the answer goes back to APRS-IS. */
    bool query_aprs_en;              /**< Enable "?APRS?" responses. */
    bool query_wx_en;                /**< Enable "?WX?" responses. */
    bool query_igate_en;             /**< Enable "?IGATE?" responses. */
    bool query_directed_en;          /**< Enable directed "CALL:?query?" responses. */
    bool query_ext_en;               /**< Enable the extended directed query set (?APRSD/?APRSH/?APRSM/?APRSO/?APRSP/?APRSS/?APRST/?PING?). */
    uint16_t query_min_interval_sec; /**< Per-type broadcast query rate limit, seconds (floored at 5). */

    bool query_cap_beacon_en;        /**< Transmit the Station Capabilities line periodically, not only in reply to "?IGATE?". Disabled by default. */
    uint32_t query_cap_interval_sec; /**< Interval between periodic Station Capabilities beacons, seconds. */
    bool query_cap_rf;               /**< Send the periodic capabilities beacon on RF. */
    bool query_cap_inet;             /**< Send the periodic capabilities beacon to APRS-IS. */
    char query_cap_extra[QUERY_CAP_EXTRA_SIZE]; /**< Free-form capability tokens appended to the two mandatory ones; empty leaves the line as the
                                                   specification's minimum. Sanitized of CR/LF and of the ',' and '>' bytes that delimit the line itself. */

} app_config_t;

/** @name Periodic Station Capabilities beacon
 *  Bounds for the optional periodic transmission of the
 *  "<IGATE,MSG_CNT=n,LOC_CNT=n>" line. APRS101 chapter 15 allows a station to
 *  send its capabilities at any time; the floor keeps a mistyped interval from
 *  spending the channel on a packet nobody asked for.
 *  @{
 */
#define QUERY_CAP_INTERVAL_S_MIN     300   /**< Shortest interval between periodic capabilities beacons. */
#define QUERY_CAP_INTERVAL_S_MAX     86400 /**< Longest interval between periodic capabilities beacons: 24 h, which is why the field is a uint32_t. */
#define QUERY_CAP_INTERVAL_S_DEFAULT 1800  /**< Interval a station gets when it enables the beacon without choosing one. */
/** @} */

/**
 * @brief Global live configuration instance (loaded at boot, edited by web
 * handlers, saved to flash).
 */
extern app_config_t g_config;

/**
 * @brief Fill @p c with the same defaults esp32idf_APRS ships with.
 * @param c Destination configuration (must be non-NULL).
 */
void app_config_set_defaults(app_config_t *c);

/**
 * @brief One stored configuration section: the settings of a single web admin
 * functionality, and the file on LittleFS that holds exactly those.
 *
 * @details The sidebar of the web admin is the index of this list: every page
 * that owns persistent settings has one entry here and one file of its own
 * under /storage, named after the page. A page's save handler rewrites only
 * its own file (app_config_save_section()), so a change to the digipeater
 * never rewrites the IGate's settings and a file that fails to write cannot
 * take another functionality's configuration down with it.
 *
 * The values themselves stay in the one resident ::app_config_t: this
 * enumeration partitions the persistence, not the structure, so every
 * subsystem still reads ::g_config exactly as before.
 *
 * The order is the order app_config_load() reads the files in, and it matters
 * in one place: ::APP_CONFIG_SECTION_BRANDMEISTER re-applies the worldwide
 * monitor interlock against the INET->RF gating that
 * ::APP_CONFIG_SECTION_IGATE carries, so the IGate file is read first.
 *
 * Pages with no persistent settings of their own (Dashboard, Snd/Rcv Msg,
 * Console Logs, File Storage, About) have no entry, and the four subsystems
 * that keep their own structures rather than fields of ::app_config_t
 * (bulletins, objects/items, telemetry, Telegram) own their files directly -
 * see bulletins.h, objects_items.h, telemetry.h and telegram_app.h.
 */
typedef enum {
    APP_CONFIG_SECTION_SYSTEM = 0,   /**< System page -> /storage/system.json. */
    APP_CONFIG_SECTION_STATION,      /**< My Station page -> /storage/station.json. */
    APP_CONFIG_SECTION_WIRELESS,     /**< Wireless page -> /storage/wireless.json. */
    APP_CONFIG_SECTION_RADIO,        /**< Radiomodem page -> /storage/radio.json. */
    APP_CONFIG_SECTION_IGATE,        /**< IGate page -> /storage/igate.json. */
    APP_CONFIG_SECTION_BRANDMEISTER, /**< BrandMeister page -> /storage/brandmeister.json. */
    APP_CONFIG_SECTION_DIGIPEATER,   /**< Digipeater page -> /storage/digi.json, including the four shared path presets edited there. */
    APP_CONFIG_SECTION_TRACKER,      /**< Tracker page -> /storage/tracker.json. */
    APP_CONFIG_SECTION_WEATHER,      /**< Weather page -> /storage/weather.json. */
    APP_CONFIG_SECTION_GPS,          /**< GPS page -> /storage/gps.json. */
    APP_CONFIG_SECTION_MESSAGE,      /**< Message page -> /storage/message.json. */
    APP_CONFIG_SECTION_WINLINK,      /**< Winlink page -> /storage/winlink.json (the account settings; the mailbox is winlink_mail.json). */
    APP_CONFIG_SECTION_QUERY,        /**< Query page -> /storage/query.json. */
    APP_CONFIG_SECTION_NUM           /**< Sentinel: number of stored sections. Not a section. */
} app_config_section_t;

/** @brief Select-mask bit of one ::app_config_section_t, for app_config_save_sections(). */
#define APP_CONFIG_SECTION_BIT(section) (1u << (section))

/** @brief Mask selecting every section, i.e. the whole stored configuration. */
#define APP_CONFIG_SECTIONS_ALL ((1u << APP_CONFIG_SECTION_NUM) - 1u)

/**
 * @brief Full path of one section's file on LittleFS.
 *
 * @param section Section to name.
 * @return The path, or NULL if @p section is not a valid section.
 */
const char *app_config_section_path(app_config_section_t section);

/**
 * @brief Load every section file into ::g_config.
 *
 * The factory defaults are applied to the whole structure first, then each
 * section file is read over them, so a key a file does not carry keeps its
 * documented default. A file that is absent, empty or unparseable is rewritten
 * from those defaults before this returns - which is what guarantees that
 * every functionality has a file on flash from the first boot onward, without
 * an operator ever having to visit its page.
 *
 * A read that fails for want of memory is the one case that writes nothing:
 * the file is very probably intact, so the whole load reports failure and
 * leaves flash untouched rather than overwriting a good configuration on the
 * strength of a failed allocation. main.c retries once before falling back to
 * the factory set.
 *
 * @return true if the configuration is now consistent on flash, false if a
 *         section could not be read this pass or a rewrite failed.
 */
bool app_config_load(void);

/**
 * @brief Rewrite the files of the sections selected by @p mask from
 * ::g_config.
 *
 * @details Every selected file is written to its own temp file and renamed
 * over the live one, so each lands atomically. A page's save handler passes
 * only what it edits; a handler that mirrors "My Station" data into other
 * services' fields passes every section it touched, since a partial save would
 * leave the station's identity split across files that no longer agree.
 *
 * Every selected section is attempted even after one has failed, so a single
 * full filesystem does not leave the remaining files holding settings the
 * operator has already replaced in RAM.
 *
 * @param mask Bitwise OR of ::APP_CONFIG_SECTION_BIT() values, or
 *             ::APP_CONFIG_SECTIONS_ALL.
 * @return true if every selected file now holds its new content.
 *
 * @note Declared ::APRS_MUST_CHECK: a call site that discards the result
 * reports success to the user for a write that may never have reached
 * flash, so ignoring it fails the build.
 */
bool app_config_save_sections(uint32_t mask) APRS_MUST_CHECK;

/**
 * @brief Rewrite one section's file from ::g_config.
 *
 * @param section Section to persist.
 * @return true on success; false if @p section is not a valid section or the
 *         write failed.
 *
 * @note Declared ::APRS_MUST_CHECK, for the reason given on
 * app_config_save_sections().
 */
bool app_config_save_section(app_config_section_t section) APRS_MUST_CHECK;

/**
 * @brief Rewrite every section's file from ::g_config.
 *
 * Used where the whole configuration changed at once - the factory reset, and
 * the boot fallback that puts the factory set on flash after a failed load.
 * A page's save handler should name what it edited instead.
 *
 * @return true if every file now holds its new content.
 *
 * @note Declared ::APRS_MUST_CHECK, for the reason given on
 * app_config_save_sections().
 */
bool app_config_save(void) APRS_MUST_CHECK;

/**
 * @brief Wipe the configuration back to factory defaults and persist.
 * @return true on success.
 */
bool app_config_factory_reset(void);

/**
 * @brief Acquire the ::g_config concurrency lock.
 *
 * @details ::g_config is written field-by-field by the web POST handlers (a
 * single settings save rewrites many fields, several of them strings/arrays,
 * one at a time) while long-running tasks (beacon builders, IGate login,
 * digipeater, message, weather) read those same fields. A reader that samples
 * a string mid-strcpy can see a torn or transiently non-NUL-terminated value
 * and walk off the end of the buffer. This lock serializes those two sides.
 *
 * It is DISTINCT from the internal save mutex (held across the whole flash
 * serialization): this one is a strict LEAF lock, held only long enough to
 * copy the needed fields into locals - never across a blocking call, I/O,
 * transmit, or another lock. Writers hold it around the block that mutates
 * ::g_config (releasing it before the save/restart); readers of
 * string/array fields hold it just long enough to memcpy a local snapshot.
 * Scalar (single-word) fields are word-atomic on this MCU and may be read
 * lock-free. The lock is created lazily on first use, so there is no
 * init-order dependency.
 */
void app_config_lock(void);

/**
 * @brief Release the ::g_config concurrency lock acquired with
 * app_config_lock().
 */
void app_config_unlock(void);

/**
 * @brief Count the AX.25 path hops that @p pathBitmask would produce from
 * @p pathPreset[0..3].
 *
 * Each selected preset slot may itself hold several comma-separated hops
 * (e.g. "WIDE1-1,WIDE2-1" counts as 2, not 1), so simply counting set bits
 * undercounts the real on-air path length. Empty/unselected slots contribute
 * 0. This is the single source of truth for "how many hops does this
 * bitmask produce", shared by the webconfig POST handlers (which enforce it
 * at save time via app_config_path_mask_clamp()) and
 * aprs_path_build_suffix() (which enforces it again at transmit time, for
 * every service that originates traffic), so the two can never drift out of
 * sync.
 *
 * @param pathBitmask Bitmask over @p pathPreset (bit N selects pathPreset[N]).
 * @param pathPreset  The four shared path presets, i.e. a copy of/reference
 *                    to ::g_config.path[0..3] taken while holding
 *                    app_config_lock().
 * @return Total number of comma-separated hops the selection would emit.
 */
uint8_t app_config_path_hop_count(uint8_t pathBitmask, const char pathPreset[4][72]);

/**
 * @brief Count the AX.25 path hops one preset string produces.
 *
 * A preset holds a comma-separated path (e.g. @c "WIDE1-1,WIDE2-1" is 2 hops,
 * not 1), so this is the per-slot half of app_config_path_hop_count(), which
 * calls it once per selected slot. Available on its own so a hop count can be
 * taken from a path that is not (yet) in a ::app_config_t, such as
 * ::PATH_PRESET_DEFAULT while the factory defaults are still being filled in.
 *
 * @param preset One path preset string; NULL or empty counts as 0 hops.
 * @return Number of comma-separated hops in @p preset.
 */
uint8_t app_config_path_preset_hops(const char *preset);

/**
 * @brief Clamp @p pathBitmask so the path it produces never exceeds AX.25's
 * 8-via limit.
 *
 * Bits are kept low-to-high (preset 1, then 2, then 3, then 4) only as long
 * as adding the next preset's hops would not push the running total past 8;
 * any bit that would exceed the budget, and every bit after it, is dropped.
 * If @p pathBitmask already produces 8 or fewer hops it is returned
 * unchanged. A dropped bit is logged as a warning so an over-long save is
 * visible in the device log even though the web form has no
 * validation-error plumbing to surface it to the browser.
 *
 * @param pathBitmask Raw bitmask read back from the web form (or NVS/restore).
 * @param pathPreset  The four shared path presets (see
 *                    app_config_path_hop_count()).
 * @return @p pathBitmask, with the minimum number of high bits cleared to
 *         bring the total hop count to 8 or fewer.
 */
uint8_t app_config_path_mask_clamp(uint8_t pathBitmask, const char pathPreset[4][72]);

/**
 * @brief Strip from a free-form Station Capabilities token string every byte
 * that would break the line carrying it.
 *
 * The capabilities line is a comma-separated list enclosed in "<" and ">", so
 * a ',' or '>' typed by the operator would either invent a token or close the
 * list early; CR and LF would end the frame itself. Each of them is removed
 * in place, leaving the rest of the text as typed.
 *
 * Called by both clamp layers - the web POST handler and the Query section
 * reader - so a hand-edited query.json is held to the same rule as the form.
 *
 * @param extra NUL-terminated buffer, edited in place. NULL is a no-op.
 */
void app_config_query_cap_extra_sanitize(char *extra);

#endif // APP_CONFIG_H
