hiperiondev/esp32idf_APRS/components/sensors_local/sensors_local.c

// @file sensors_local.c
//
// @author Emiliano Augusto Gonzalez ( lu3vea @ gmail . com)
// @date 2026
// @copyright GNU General Public License v3
// @see https://github.com/hiperiondev/esp32idf_APRS
//
// @note
// This is based on other projects:
//     VP-Digi: https://github.com/sq8vps/vp-digi
//     ESP32APRS: https://github.com/nakhonthai/ESP32APRS_Audio
//     LibAPRS: https://github.com/markqvist/LibAPRS
//
//     please contact their authors for more information.
//
// @brief Run-time registry of dynamically loaded local sensor drivers and the
//        common ::sensors_local_save aggregation entry. See sensors_local.h.

#include "sensors_local.h"

#include <stdlib.h>
#include <string.h>

#include "esp_log.h"
#include "freertos/FreeRTOS.h"
#include "freertos/semphr.h"

static const char *TAG = "sensors_local";

// --------------------------------------------------------------------------
// The "dynamic functions pointer" table: a heap array of driver pointers that
// grows on demand. Each slot points at a caller-owned sensor_local_driver_t
// (a bundle of function pointers), never a copy.
//
// REGISTRATION LIFETIME CONTRACT: drivers register (via the AUTOREGISTER
// constructors) during the single-threaded boot/init phase, and the registry
// only ever grows. Callers therefore rely on a registered driver pointer
// staying valid and stable for the program's lifetime: sensors_local_get()
// hands back a bare pointer, and sensors_local_init_all()/sensors_local_save()
// snapshot pointers under the lock and then use them after releasing it. Both
// assumptions would have to be revisited (e.g. refcounting the driver objects)
// before any removal path could be added.
// --------------------------------------------------------------------------
static sensor_local_driver_t **s_registry = NULL; // < Dynamic array of driver pointers.
static size_t s_count = 0;                        // < Number of live entries.
static size_t s_capacity = 0;                     // < Allocated slots in s_registry.

// Upper bound on drivers serviced in one sensors_local_init_all() or
// sensors_local_save() pass. Sized well above any realistic local-sensor
// count; the snapshot lets the (blocking) bus I/O run without the registry
// lock held.
#define SENSORS_LOCAL_MAX_SNAPSHOT 32

// Guards the registry. Created in sensors_local_init(); NULL means "not yet
// created", which happens during the C-constructor phase (single threaded,
// scheduler not running) where locking is neither possible nor needed.
static SemaphoreHandle_t s_lock = NULL;

static inline void registry_lock(void) {
    if (s_lock != NULL)
        xSemaphoreTake(s_lock, portMAX_DELAY);
}

static inline void registry_unlock(void) {
    if (s_lock != NULL)
        xSemaphoreGive(s_lock);
}

// Find index of a driver by name. Caller must hold the lock. Returns SIZE_MAX
// when not present.
static size_t registry_index_of(const char *name) {
    for (size_t i = 0; i < s_count; i++) {
        if (s_registry[i] != NULL && s_registry[i]->name != NULL && strcmp(s_registry[i]->name, name) == 0)
            return i;
    }
    return (size_t)-1;
}

// Lazily run a driver's init() exactly once. Must be called either with the
// registry lock held, or on a stable snapshot pointer with no concurrent
// (un)registration (see the registration-lifetime contract above); it mutates
// only the driver's own initialized/failed flags, not the registry array.
static esp_err_t ensure_initialized(sensor_local_driver_t *d) {
    if (d->failed)
        return ESP_FAIL;
    if (d->initialized)
        return ESP_OK;

    if (d->init != NULL) {
        esp_err_t err = d->init(d);
        if (err != ESP_OK) {
            d->failed = true;
            ESP_LOGW(TAG, "driver '%s' init failed: %s", d->name ? d->name : "?", esp_err_to_name(err));
            return err;
        }
    }
    d->initialized = true;
    return ESP_OK;
}

esp_err_t sensors_local_init(void) {
    if (s_lock == NULL) {
        s_lock = xSemaphoreCreateMutex();
        if (s_lock == NULL) {
            ESP_LOGE(TAG, "could not create registry mutex");
            return ESP_ERR_NO_MEM;
        }
    }
    ESP_LOGI(TAG, "initialised (%u driver(s) already registered)", (unsigned)s_count);
    return ESP_OK;
}

esp_err_t sensors_local_register(sensor_local_driver_t *driver) {
    if (driver == NULL || driver->save == NULL || driver->name == NULL || driver->name[0] == '\0') {
        ESP_LOGE(TAG, "rejected malformed driver descriptor");
        return ESP_ERR_INVALID_ARG;
    }

    // Every driver must declare what kind of sensor it is (Weather,
    // Telemetry, or any future ::sensor_local_data_kind_t bit) so that
    // consumers of the registry - e.g. the Weather "Sensor Mapping" channel
    // picker - can filter it by type instead of listing every registered
    // sensor regardless of what it actually produces.
    if (driver->capabilities == SENSOR_LOCAL_DATA_NONE) {
        ESP_LOGE(TAG,
                 "rejected driver '%s': capabilities not set (must declare SENSOR_LOCAL_DATA_WEATHER and/or "
                 "SENSOR_LOCAL_DATA_TELEMETRY, or a future sensor kind)",
                 driver->name);
        return ESP_ERR_INVALID_ARG;
    }

    registry_lock();

    if (registry_index_of(driver->name) != (size_t)-1) {
        registry_unlock();
        ESP_LOGE(TAG, "driver '%s' already registered", driver->name);
        return ESP_ERR_INVALID_STATE;
    }

    if (s_count == s_capacity) {
        size_t new_cap = (s_capacity == 0) ? 4 : s_capacity * 2;
        sensor_local_driver_t **grown = realloc(s_registry, new_cap * sizeof(*grown));
        if (grown == NULL) {
            registry_unlock();
            ESP_LOGE(TAG, "out of memory growing registry to %u", (unsigned)new_cap);
            return ESP_ERR_NO_MEM;
        }
        s_registry = grown;
        s_capacity = new_cap;
    }

    driver->initialized = false;
    driver->failed = false;
    s_registry[s_count++] = driver;

    registry_unlock();
    ESP_LOGI(TAG, "registered driver '%s' (caps=0x%02x)", driver->name, (unsigned)driver->capabilities);
    return ESP_OK;
}

size_t sensors_local_count(void) {
    registry_lock();
    size_t n = s_count;
    registry_unlock();
    return n;
}

sensor_local_driver_t *sensors_local_get(size_t index) {
    registry_lock();
    sensor_local_driver_t *d = (index < s_count) ? s_registry[index] : NULL;
    registry_unlock();
    return d;
}

// Sensor-channel persistence: config stores driver names, runtime uses registry
// positions (see the contract in sensors_local.h). Both directions resolve
// under the registry lock; the returned name is owned by the driver descriptor,
// which outlives every caller.
const char *sensors_local_channel_name(uint8_t ch) {
    if (ch == SENSOR_LOCAL_CH_NONE)
        return "";
    registry_lock();
    const char *name = ((size_t)ch < s_count && s_registry[ch] != NULL && s_registry[ch]->name != NULL) ? s_registry[ch]->name : "";
    registry_unlock();
    return name;
}

uint8_t sensors_local_channel_from_name(const char *name) {
    if (name == NULL || name[0] == '\0')
        return SENSOR_LOCAL_CH_NONE;
    registry_lock();
    size_t idx = registry_index_of(name);
    registry_unlock();
    // A registry big enough to reach the "(none)" sentinel would make the two
    // indistinguishable, so anything from there up is reported as unmapped.
    if (idx == (size_t)-1 || idx >= SENSOR_LOCAL_CH_NONE)
        return SENSOR_LOCAL_CH_NONE;
    return (uint8_t)idx;
}

esp_err_t sensors_local_init_all(void) {
    // Snapshot the driver pointers under the lock, then release it BEFORE
    // running any init(), for the same reason as sensors_local_save() below:
    // a driver's init() does blocking bus I/O (e.g. BME280 I2C conversions
    // take tens of ms) and holding the registry lock across the whole sweep
    // would stall every other registry caller for the sum of them. Driver
    // objects are stable for the program's lifetime (see the note at the top
    // of this file), so the snapshotted pointers stay valid.
    sensor_local_driver_t *sel[SENSORS_LOCAL_MAX_SNAPSHOT];
    size_t sel_n = 0;
    bool truncated = false;

    registry_lock();
    for (size_t i = 0; i < s_count; i++) {
        if (s_registry[i] == NULL)
            continue;
        if (sel_n >= SENSORS_LOCAL_MAX_SNAPSHOT) {
            // More drivers than the snapshot can hold: this pass cannot cover
            // them all, so the caller must not be told it succeeded.
            truncated = true;
            break;
        }
        sel[sel_n++] = s_registry[i];
    }
    registry_unlock();

    if (truncated)
        ESP_LOGE(TAG, "more than %d drivers registered; the rest are not initialised this pass", SENSORS_LOCAL_MAX_SNAPSHOT);

    // A driver that fails is logged and skipped so the others still come up,
    // but the aggregate return says whether every driver did initialise.
    esp_err_t result = truncated ? ESP_FAIL : ESP_OK;

    for (size_t i = 0; i < sel_n; i++) {
        if (ensure_initialized(sel[i]) != ESP_OK)
            result = ESP_FAIL; // already logged; keep going
    }
    return result;
}

esp_err_t sensors_local_save(weather_telemetry_data_t *data, sensor_local_data_kind_t kind) {
    if (data == NULL) {
        ESP_LOGE(TAG, "sensors_local_save: NULL data container");
        return ESP_ERR_INVALID_ARG;
    }
    if (kind == SENSOR_LOCAL_DATA_NONE)
        return ESP_OK;

    // Snapshot the matching driver pointers under the lock, then release it
    // BEFORE touching the hardware. ensure_initialized()/d->save() do blocking
    // bus I/O (e.g. BME280 I2C conversions take tens of ms); holding the
    // registry lock across them would stall every other registry caller
    // (sensors_local_count/get from the web sensor page, etc.) for the whole
    // transaction. Driver objects are stable for the program's lifetime
    // (drivers only (un)register during single-threaded boot - see the note at
    // the top of this file), so the snapshotted pointers stay valid.
    sensor_local_driver_t *sel[SENSORS_LOCAL_MAX_SNAPSHOT];
    size_t sel_n = 0;
    bool truncated = false;

    registry_lock();
    for (size_t i = 0; i < s_count; i++) {
        sensor_local_driver_t *d = s_registry[i];
        if (d == NULL || (d->capabilities & (uint32_t)kind) == 0)
            continue;
        if (sel_n >= SENSORS_LOCAL_MAX_SNAPSHOT) {
            // More capable drivers than the snapshot can hold: the pass cannot
            // cover them all, so the caller must not be told it succeeded.
            truncated = true;
            break;
        }
        sel[sel_n++] = d;
    }
    registry_unlock();

    if (truncated)
        ESP_LOGE(TAG, "more than %d capable drivers registered; the rest are not serviced this pass", SENSORS_LOCAL_MAX_SNAPSHOT);

    // Outcome of the whole pass, same convention as sensors_local_init_all():
    // a driver that fails is logged and skipped so the others still run, but
    // the aggregate return says whether every selected driver did contribute.
    esp_err_t result = truncated ? ESP_FAIL : ESP_OK;

    for (size_t i = 0; i < sel_n; i++) {
        sensor_local_driver_t *d = sel[i];

        if (ensure_initialized(d) != ESP_OK) {
            result = ESP_FAIL; // already logged; keep going
            continue;
        }

        // Only ask the driver for the families it actually advertises.
        sensor_local_data_kind_t ask = (sensor_local_data_kind_t)(d->capabilities & (uint32_t)kind);

        esp_err_t err = d->save(d, data, ask);
        if (err != ESP_OK) {
            ESP_LOGW(TAG, "driver '%s' save failed: %s", d->name ? d->name : "?", esp_err_to_name(err));
            result = ESP_FAIL;
        }
    }
    return result;
}

esp_err_t sensors_local_save_one(size_t index, weather_telemetry_data_t *data, sensor_local_data_kind_t kind) {
    if (data == NULL || kind == SENSOR_LOCAL_DATA_NONE)
        return ESP_ERR_INVALID_ARG;

    // Snapshot the single driver pointer under the lock (see the locking note
    // on sensors_local_save() above), then do the (possibly blocking) init and
    // read outside it.
    registry_lock();
    sensor_local_driver_t *d = (index < s_count) ? s_registry[index] : NULL;
    registry_unlock();

    if (d == NULL)
        return ESP_ERR_NOT_FOUND;

    esp_err_t err = ensure_initialized(d);
    if (err != ESP_OK)
        return err;

    sensor_local_data_kind_t ask = (sensor_local_data_kind_t)(d->capabilities & (uint32_t)kind);
    if (ask == SENSOR_LOCAL_DATA_NONE)
        return ESP_ERR_INVALID_ARG; // driver doesn't support any of the requested kinds

    return d->save(d, data, ask);
}
