hiperiondev/esp32idf_APRS/components/esp32idf_radioamateur_modem/src/afsk.c

// @file afsk.c
//
// @author Emiliano Augusto Gonzalez ( lu3vea @ gmail . com)
// @date 2026
// @copyright GNU General Public License v3
// @see https://github.com/hiperiondev/esp32idf_APRS
//
// @note
// This is based on other projects:
//     VP-Digi: https://github.com/sq8vps/vp-digi
//     ESP32APRS: https://github.com/nakhonthai/ESP32APRS_Audio
//     LibAPRS: https://github.com/markqvist/LibAPRS
//
//     please contact their authors for more information.
//
// @brief ESP-IDF hardware abstraction layer implementation for the AFSK modem:
// free-running continuous ADC (DMA) receive path, GPTimer-driven one-shot DAC
// transmit path, and PTT / TX / RX GPIO handling.

#include <inttypes.h>
#include <math.h>
#include <stdlib.h>
#include <string.h>

#include "driver/dac_oneshot.h"
// driver/gpio.h for gpio_config()/gpio_set_level()/gpio_num_t, used by the
// MODEM_PTT_GPIO / MODEM_LED_TX_GPIO / MODEM_LED_RX_GPIO blocks below. Those
// three pins default to -1 in esp32idf_radioamateur_modem_config.h, so each
// #if MODEM_*_GPIO >= 0 block that touches the GPIO API is compiled in only
// when its pin is assigned a real value - as this project does for PTT, from
// the top-level CMakeLists.txt.
//
// MODEM_PTT_GPIO in particular is a fixed, compile-time-only board wiring
// choice - an internal radiomodem feature, exactly like MODEM_ADC_GPIO /
// MODEM_DAC_GPIO - and is not exposed as a runtime/web-admin setting.
#include "driver/gpio.h"
#include "driver/gptimer.h"
// driver/rtc_io.h for rtc_gpio_pullup_en()/rtc_gpio_pulldown_en(): the ADC pad's
// internal bias, selectable at runtime through afskSetAdcSelfBias(), is an RTC
// IO feature and is not reachable through the ordinary GPIO driver.
#include "driver/rtc_io.h"
#include "esp_adc/adc_cali.h"
#include "esp_adc/adc_cali_scheme.h"
#include "esp_adc/adc_continuous.h"
#include "esp_attr.h"
// esp_private/esp_gpio_reserve.h for esp_gpio_revoke(). gpio_config() claims
// every pin it configures, and warns when it finds one already claimed. The
// PTT pad is deliberately configured twice - once by the application as early
// as it can, to keep the keying line from floating out of reset, and once here
// when the modem starts - so this file hands the claim back before taking it
// again. The header is an internal one, so its absence is tolerated: without
// it the second configuration still applies, it merely logs a conflict.
#if __has_include("esp_private/esp_gpio_reserve.h")
#include "esp_private/esp_gpio_reserve.h"
#define AFSK_HAVE_GPIO_RESERVE 1
#endif
#include "esp_idf_version.h"
#include "esp_log.h"
#include "esp_timer.h"
#include "freertos/FreeRTOS.h"
#include "freertos/task.h"
// hal/gpio_ll.h provides gpio_ll_set_level(): a direct out-register write,
// always-inline and therefore IRAM-safe. gpio_set_level() from driver/gpio.h
// lives in flash, so it must never be called from setPtt()/LED_Status2(),
// which run in the DAC ISR while the flash cache can be disabled by a
// concurrent flash read.
#include "hal/gpio_ll.h"
#include "sdkconfig.h"
#include "soc/soc_caps.h"

#include "afsk.h"
#include "ax25.h"
#include "esp32idf_radioamateur_modem_config.h"
#include "impulse_blanker.h"
#include "modem.h"
#include "rx_agc.h"
#include "rx_dc_block.h"
#include "rx_hpf.h"

#ifdef ENABLE_FX25
#include "fx25.h"
#endif

static const char *TAG = "afsk";

// ------------------------------------------------------------------
// RX sample ring buffer
// ------------------------------------------------------------------

// Reassembly buffer between adc_ingest() and AFSK_Poll(). Both run in
// afsk_rx_task, so this is a plain single-threaded queue; it exists only
// because adc_continuous_read() may hand back a partial frame and AFSK_Poll()
// wants whole MODEM_BLOCK_SIZE blocks.
//
// The sample copy runs entirely at task priority, out of interrupt context:
// the ADC callback does nothing but count samples (see adc_conv_done_cb), and
// afsk_rx_task blocks in adc_continuous_read() and does the work where taking
// as long as it likes costs the modulator nothing. Keeping the copy off the
// DAC clock's interrupt level (level 3) matters: a contiguous blackout of that
// timer longer than about 4-6 sample periods (~100-150 us) freezes the
// modulator mid-symbol at every baud rate, because the phase accumulator and
// the symbol counter both stop and the resulting step in the waveform is not
// something a tracking loop can follow. A uniform rate of missed DAC alarms,
// by contrast, is harmless - the demodulator's DPLL tracks it and every frame
// still decodes.
//
// MODEM_RX_FIFO_SIZE must be a power of two so the index is a mask, not a
// modulo of a wrapping counter.
_Static_assert((MODEM_RX_FIFO_SIZE & (MODEM_RX_FIFO_SIZE - 1)) == 0, "MODEM_RX_FIFO_SIZE must be a power of two");

#define RB_MASK (MODEM_RX_FIFO_SIZE - 1)

typedef struct {
    int16_t buffer[MODEM_RX_FIFO_SIZE];
    volatile uint32_t head; // written by adc_ingest() only
    volatile uint32_t tail; // written by AFSK_Poll() only
} RingBuffer;

static RingBuffer s_fifo;

// Deferred flush. AFSK_FlushFifo() is called from the service task and from
// afskSetModem(), neither of which is the consumer; letting them write tail
// directly would put two writers on it and break the single-consumer invariant.
// They raise a flag instead and AFSK_Poll() does the work between blocks.
static volatile bool s_flushReq = false;

// Deferred carrier-detect reset. The DCD state belongs to the demodulators and
// is only written from afsk_rx_task, so the transmit teardown in
// AFSK_ServiceTx(), which runs in the service task, raises this flag and
// AFSK_Poll() calls ModemResetDcd() between blocks.
static volatile bool s_dcdResetReq = false;

static inline void rb_init(RingBuffer *rb) {
    rb->head = 0;
    rb->tail = 0;
}

static inline uint32_t rb_size(const RingBuffer *rb) {
    return rb->head - rb->tail; // unsigned: correct across the wrap
}

static bool rb_pop(RingBuffer *rb, int16_t *data) {
    uint32_t tail = rb->tail;

    if ((rb->head - tail) == 0)
        return false;

    *data = rb->buffer[tail & RB_MASK];
    __sync_synchronize(); // read the sample before publishing the new tail
    rb->tail = tail + 1;
    return true;
}

void AFSK_FlushFifo(void) {
    s_flushReq = true;
}

// ------------------------------------------------------------------
// State
// ------------------------------------------------------------------

static adc_continuous_handle_t s_adc = NULL;
static adc_cali_handle_t s_cali = NULL;
static dac_oneshot_handle_t s_dac = NULL;
static gptimer_handle_t s_dacTimer = NULL;
static TaskHandle_t s_rxTask = NULL;
static volatile bool s_rxStop = false;   // asks afsk_rx_task to exit
static volatile bool s_rxExited = false; // set by afsk_rx_task on the way out
// Receive-task hold used by afskSetModem(). The requester raises
// s_rxPauseReq; afsk_rx_task acknowledges with s_rxPaused at the top of its
// loop, between two conversion frames, and waits there until the request is
// withdrawn. A task held this way is never in the middle of demodulating or of
// writing a frame into the AX.25 receive ring, which is what the rebuild
// relies on.
static volatile bool s_rxPauseReq = false;
static volatile bool s_rxPaused = false;

// Transmit state shared by the service task and the DAC ISR, which runs on
// the other core. Stores are release and loads acquire (see setTransmit()):
// the order in which a key-down publishes them is what the service task
// relies on to never key up inside the previous key-down.
static volatile bool s_txActive = false;
static volatile bool s_txStopPending = false;
static volatile bool s_fullDuplex = true;
static bool s_dacTimerRunning = false;
static bool s_inited = false;

static volatile uint32_t s_adcSamples = 0; // total samples produced by the ADC
static volatile uint32_t s_fifoDrops = 0;  // samples dropped on a full RX FIFO
static volatile uint32_t s_poolOvf = 0;    // ADC driver pool overflow events
static float s_dacAlarmRateHz = 0.0f;      // rate the alarm really fires at

// Diagnostic capture tap (raw ADC samples, still used by main/aprs_service.c).
//
// The buffer is owned by this file and never handed out: afskDiagCaptureRaw()
// copies out of it once the capture window closes. The producer runs in
// afsk_rx_task (possibly on the other core) and the consumer in the caller's
// task, so a caller-supplied destination pointer could be revoked in the
// instructions between the producer's bounds test and its store. With a
// statically owned buffer there is no pointer to revoke: the only shared state
// is the arm/disarm length, and a store that slips through after disarming
// still lands inside s_capBuf.
#define AFSK_DIAG_CAP_SAMPLES 512

// Blocking timeout of one adc_continuous_read() call, in milliseconds. It is a
// safety net rather than a rate limit: at the configured sample rate a frame is
// always ready far sooner, and the bounded wait is what lets the receive task
// notice a stop request.
#define ADC_READ_TIMEOUT_MS 100

static int16_t s_capBuf[AFSK_DIAG_CAP_SAMPLES];
static volatile int s_capRawLen = 0; // > 0 arms the tap; also the write bound
static volatile int s_capRawIdx = 0;

static float s_audio[MODEM_BLOCK_SIZE];
static float s_agcGain = 1.0f;

static int s_offset = 0; // DC offset of the input, in mV
static int s_mVrms = 0;  // last RMS reading, in mV
static uint8_t s_dcdCnt = 0;
static bool s_gateOpen = false; // receive gate state of the previous block

// Raw ADC extremes of the last completed block, before DC removal, AGC and
// decimation. Written by AFSK_Poll() and read by afskGetRawMinMax() from
// another task; both halves are 16 bit, so a reader can only ever observe one
// block boundary in the middle of the pair, which is what a level display of
// this kind is expected to tolerate.
static int16_t s_rawMin = 0;
static int16_t s_rawMax = 0;

// Over-range reporting. s_clipWarn is the operator's selection; s_clipNextWarnMs
// is the millisecond timestamp before which no further warning is emitted, kept
// as a deadline rather than a countdown so the comparison stays correct across
// the 32-bit wrap. The raw thresholds are AFSK_RAW_CLIP_LOW/HIGH in afsk.h.
static bool s_clipWarn = false;
static uint32_t s_clipNextWarnMs = 0;
#define CLIP_WARN_HOLD_MS 5000

// Tone-band level meter: two identical second-order band-passes in cascade on
// the decimated signal, centred at the geometric mean of 900 and 2600 Hz with
// Q = 0.9, and the millivolts one ADC count is worth, taken from the
// calibration curve when the ADC starts.
#define BAND_METER_LO_HZ 900.0f
#define BAND_METER_HI_HZ 2600.0f
#define BAND_METER_Q     0.9f
static float s_bandB0, s_bandB2, s_bandA1, s_bandA2;
static float s_bandX1[2], s_bandX2[2], s_bandY1[2], s_bandY2[2];
static float s_mvPerCount = 0.806f;
static int s_bandMvRms = 0;

// Receive DSP load: wall-clock time AFSK_Poll() spends on each block, against
// the MODEM_BLOCK_SIZE / MODEM_ADC_SAMPLERATE seconds of audio the block
// holds. The window figures (sum, count, peak) are cleared by the receive task
// itself on the first block after afskGetDspLoad() asks for it, so the reader
// never writes them; the maximum only restarts with afskResetRxCounters().
#define DSP_BLOCK_US ((uint32_t)((1000000ULL * MODEM_BLOCK_SIZE) / MODEM_ADC_SAMPLERATE))
static volatile uint32_t s_dspBusySumUs = 0;
static volatile uint32_t s_dspBlocks = 0;
static volatile uint32_t s_dspPeakUs = 0;
static volatile uint32_t s_dspMaxUs = 0;
static volatile bool s_dspWindowReset = false;

// Receive capture (afskCaptureStart()): a ring of records written by the
// receive task and read by one other task. s_capHead counts records written,
// s_capTail records read; each side only moves its own counter, so the ring
// needs no lock. s_capRing is published last on start and cleared first on
// stop, and the ring is freed only after the receive task has had time to
// finish any block that still holds the old pointer.
static afsk_capture_block_t *volatile s_capRing = NULL;
static uint32_t s_capSlots = 0;
static volatile uint32_t s_capHead = 0;
static volatile uint32_t s_capTail = 0;
static uint32_t s_capSeq = 0;
static volatile uint32_t s_capDropped = 0;

static void capture_block(const float *audio, int16_t rawMin, int16_t rawMax, uint32_t busyUs, bool gateOpen, bool blanked);

// A window nobody reads is restarted after one hour of blocks, which keeps the
// busy-time sum far inside 32 bits at any load.
#define DSP_WINDOW_MAX_BLOCKS ((uint32_t)(3600ULL * MODEM_ADC_SAMPLERATE / MODEM_BLOCK_SIZE))

// DAC sample rate the modulator is programmed for. Fixed while the modem runs:
// AFSK_init() turns it into the sample-clock alarm period and ModemInit() turns
// it into the tone phase steps and the baud-rate divider, so it is only writable
// while the hardware is stopped.
static uint32_t s_dacRate = MODEM_DAC_SAMPLERATE;

// Selection state of the ADC pad's internal input bias.
static bool s_adcSelfBias = false;

// DC tracker of the raw ADC stream, used to re-centre the samples before
// demodulation (see rx_dc_block.h).
static rx_dc_block_t s_dcBlock;

// DAC idle/centre code and amplitude scaling.
//
// IRAM_ATTR: called directly from dac_timer_isr(), which is itself IRAM_ATTR.
// A plain "static inline" is only a hint - at CONFIG_COMPILER_OPTIMIZATION_DEBUG
// (-Og), GCC frequently declines it, and an un-inlined static function is
// placed in flash by default. That introduces the exact XIP-fetch jitter the
// other ISR-path functions on the transmit side (dac_write_isr() here,
// calculateCRC() in ax25.c) are IRAM_ATTR to avoid.
#define DAC_MID 128

// Peak-to-peak swing of the DAC output, in percent of the full range. Written
// only by afskSetDacAmplitude() (task context) and read by dac_scale() in the
// DAC timer ISR: a single-byte load, so the ISR either sees the old value or
// the new one and never a torn intermediate. A change therefore takes effect
// on the next sample, without stopping the modulator.
static uint8_t s_dacAmplitudePct = MODEM_DAC_AMPLITUDE_PCT;

static inline uint8_t IRAM_ATTR dac_scale(uint8_t s) {
    int v = DAC_MID + (((int)s - DAC_MID) * (int)s_dacAmplitudePct) / 100;
    if (v < 0)
        v = 0;
    if (v > 255)
        v = 255;
    return (uint8_t)v;
}

// ------------------------------------------------------------------
// Receive front end: gate, gain control, high-pass, resampler
// ------------------------------------------------------------------

// Gain control: the law and its constants are in rx_agc.h, shared with the
// PC replay.

// Receive gate. s_gateOnMv is the opening threshold (0 = no gate), compared
// with the tone-band level of each block; the gate closes below half of it,
// and s_dcdCnt counts blocks above the threshold. The
// pending values are written by afskSetRxFrontEnd() and copied into the live
// ones by afskSetModem() while the receive task is held.
static uint16_t s_gateOnMv = 10;
static uint16_t s_gateOffMv = 5;
static uint16_t s_pendGateMv = 10;

// Impulse blanker on the raw ADC stream of the AFSK profiles (see
// impulse_blanker.h). s_pendBlank is written by afskSetRxFrontEnd() and
// copied into s_blankOn by afskSetModem() while the receive task is held.
static impulse_blanker_t s_blanker;
static bool s_blankOn = true;
static bool s_pendBlank = true;

// Receive gain: automatic, or fixed at s_fixedGain.
static bool s_agcFixed = false;
static float s_fixedGain = 1.0f;
static bool s_pendAgcFixed = false;
static int8_t s_pendFixedGainDb = 0;

// Fourth-order Butterworth high-pass on the decimated AFSK signal (see
// rx_hpf.h); s_pendHpfHz is its corner as stored by afskSetRxFrontEnd().
static uint16_t s_pendHpfHz = 0;
static rx_hpf_t s_hpf;

// Decimated blocks received while the gate was closed, oldest first once the
// ring has wrapped. When the gate opens these are demodulated ahead of the
// block that opened it, so the start of a transmission - the blocks that
// were needed to decide the gate should open - still reaches the
// demodulators. RX_HOLD_BLOCKS matches the number of blocks the gate needs.
#define RX_HOLD_BLOCKS   3
#define RX_DECIM_SAMPLES (MODEM_BLOCK_SIZE / MODEM_RESAMPLE_RATIO)
static float s_hold[RX_HOLD_BLOCKS][RX_DECIM_SAMPLES];
static uint8_t s_holdHead = 0;  // slot the next closed block is written to
static uint8_t s_holdCount = 0; // valid slots

// @brief Track the input level on the block about to be demodulated.
//
// Measures the in-band (decimated, for the AFSK profiles) signal rather than
// the raw ADC stream, so out-of-band noise - the bulk of a discriminator
// output's energy above 5 kHz - does not set the gain. Only called while the
// gate is open. See rx_agc.h for the law and for why a block below
// AGC_SQUELCH_RMS holds the gain.
static void update_agc(const float *buf, size_t len) {
    s_agcGain = rx_agc_update(s_agcGain, buf, len);
}

// @brief Build the tone-band meter coefficients and clear its state.
//
// Constant-peak-gain band-pass from the bilinear transform, at the demodulator
// sample rate the decimated signal runs at.
static void band_meter_setup(void) {
    const float f0 = sqrtf(BAND_METER_LO_HZ * BAND_METER_HI_HZ);
    const float w0 = 2.0f * (float)M_PI * f0 / (float)MODEM_DEMOD_SAMPLERATE;
    const float alpha = sinf(w0) / (2.0f * BAND_METER_Q);
    const float a0 = 1.0f + alpha;

    s_bandB0 = alpha / a0;
    s_bandB2 = -alpha / a0;
    s_bandA1 = -2.0f * cosf(w0) / a0;
    s_bandA2 = (1.0f - alpha) / a0;
    memset(s_bandX1, 0, sizeof(s_bandX1));
    memset(s_bandX2, 0, sizeof(s_bandX2));
    memset(s_bandY1, 0, sizeof(s_bandY1));
    memset(s_bandY2, 0, sizeof(s_bandY2));
}

// @brief RMS of a decimated block through the tone-band meter, in ADC counts.
//
// Reads buf without changing it; only the meter's own filter state advances.
static float band_meter_run(const float *buf, int len) {
    float sumSq = 0.0f;

    for (int i = 0; i < len; i++) {
        float v = buf[i];
        for (int st = 0; st < 2; st++) {
            float y = s_bandB0 * v + s_bandB2 * s_bandX2[st] - s_bandA1 * s_bandY1[st] - s_bandA2 * s_bandY2[st];
            s_bandX2[st] = s_bandX1[st];
            s_bandX1[st] = v;
            s_bandY2[st] = s_bandY1[st];
            s_bandY1[st] = y;
            v = y;
        }
        sumSq += v * v;
    }

    return (len > 0) ? sqrtf(sumSq / (float)len) * 2048.0f : 0.0f;
}

// @brief Hand one block to the demodulators at the current gain.
//
// demodulate() is documented for <= 13 bit input, and filterRun() accumulates
// coeff*sample in an int32 across up to MODEM_RX_BPF_TAPS_MAX taps. Clamping
// here keeps both safe no matter what the gain or a hot input does.
static void demod_feed(const float *buf, int len) {
    const float scale = s_agcGain * 2048.0f;

    for (int i = 0; i < len; i++) {
        float v = buf[i] * scale;
        if (v > 2047.0f)
            v = 2047.0f;
        else if (v < -2047.0f)
            v = -2047.0f;
        MODEM_DECODE((int16_t)v, (uint16_t)s_mVrms);
    }
}

// @brief Keep a decimated block received while the gate was closed.
static void hold_push(const float *buf, int len) {
    memcpy(s_hold[s_holdHead], buf, (size_t)len * sizeof(float));
    s_holdHead = (uint8_t)((s_holdHead + 1) % RX_HOLD_BLOCKS);
    if (s_holdCount < RX_HOLD_BLOCKS)
        s_holdCount++;
}

// @brief Demodulate the held blocks, oldest first, and empty the ring.
static void hold_flush(int len) {
    uint8_t slot = (uint8_t)((s_holdHead + RX_HOLD_BLOCKS - s_holdCount) % RX_HOLD_BLOCKS);

    for (uint8_t n = 0; n < s_holdCount; n++) {
        demod_feed(s_hold[slot], len);
        slot = (uint8_t)((slot + 1) % RX_HOLD_BLOCKS);
    }
    s_holdCount = 0;
}

// Anti-alias FIR for the MODEM_ADC_SAMPLERATE -> 9600 Hz decimation.
//
// What sets the requirement is where the out-of-band noise lands after the
// decimation, not the 4800 Hz Nyquist frequency. At 9600 Hz everything
// between 7000 and 12200 Hz folds straight onto the 900-2600 Hz band the
// demodulators work in - 7400 Hz onto the 2200 Hz space tone, 8400 Hz onto the
// 1200 Hz mark tone - and the demodulators' own band-pass runs after the
// decimation, so it cannot tell the folded noise from signal. A discriminator
// output makes this the dominant noise term: FM noise density rises with the
// square of the frequency, so the 7-12 kHz region carries far more noise than
// the tone band does.
//
// The filter is therefore a Blackman-windowed sinc with its cutoff at 3500 Hz,
// normalized to unity gain at DC: -0.5 dB at 1200 Hz, -1.8 dB at 2200 Hz,
// -2.7 dB at 2600 Hz, and at least 44 dB of rejection from 7000 Hz upwards
// (54 dB at 7400 Hz). A band-pass after the decimation removes what remains
// between 2600 and 4800 Hz; the 1.4 dB of tilt between the two tones is well
// inside what the demodulator set absorbs.
//
// The rejection depends on the length of the filter in samples, which is why
// every ratio has its own set: at 76800 Hz it takes 48 taps, at 38400 Hz the
// same response needs 24. Host simulation of the whole receive chain with
// discriminator noise puts the decoder within the frame-count scatter of
// Direwolf's multi-slicer demodulator down to 6 dB of in-band SNR with the
// 48-tap set, where an 8:1 filter with 10 dB of rejection at 7400 Hz already
// fails at 9 dB.
//
// Only every MODEM_RESAMPLE_RATIO-th output is computed, so the cost is
// FILTER_TAPS multiplies per 9600 Hz output sample.
#if MODEM_RESAMPLE_RATIO == 8
#define FILTER_TAPS 48
static const float resample_coeffs[FILTER_TAPS] = {
    0.000000000f,  0.000003683f,  -0.000012507f, -0.000096507f, -0.000300537f, -0.000670188f, -0.001227254f, -0.001947246f, -0.002735303f, -0.003406689f,
    -0.003679415f, -0.003185913f, -0.001507891f, 0.001766157f,  0.006966981f,  0.014265589f,  0.023604266f,  0.034653204f,  0.046805534f,  0.059217534f,
    0.070892558f,  0.080798540f,  0.088001577f,  0.091793827f,  0.091793827f,  0.088001577f,  0.080798540f,  0.070892558f,  0.059217534f,  0.046805534f,
    0.034653204f,  0.023604266f,  0.014265589f,  0.006966981f,  0.001766157f,  -0.001507891f, -0.003185913f, -0.003679415f, -0.003406689f, -0.002735303f,
    -0.001947246f, -0.001227254f, -0.000670188f, -0.000300537f, -0.000096507f, -0.000012507f, 0.000003683f,  0.000000000f,
};
#elif MODEM_RESAMPLE_RATIO == 4
#define FILTER_TAPS 24
static const float resample_coeffs[FILTER_TAPS] = {
    0.000000000f, -0.000056586f, -0.000751303f, -0.002751272f, -0.005664650f, -0.006679907f, -0.000180160f, 0.020181109f,
    0.057093324f, 0.105480602f,  0.152206614f,  0.181122228f,  0.181122228f,  0.152206614f,  0.105480602f,  0.057093324f,
    0.020181109f, -0.000180160f, -0.006679907f, -0.005664650f, -0.002751272f, -0.000751303f, -0.000056586f, 0.000000000f,
};
#elif MODEM_RESAMPLE_RATIO == 1
#define FILTER_TAPS 1
static const float resample_coeffs[FILTER_TAPS] = { 1.0f };
#else
#error "No decimation FIR for this MODEM_RESAMPLE_RATIO. Design one with at least 40 dB of rejection from 7000 Hz upwards at the new input rate."
#endif

#if FILTER_TAPS > 1
// The last FILTER_TAPS - 1 raw samples of the previous block, prepended
// ahead of this one so the filter has real data to draw on instead of
// zeros at the join. A decimator fed block-by-block must carry this
// history between calls.
static float s_resampleTail[FILTER_TAPS - 1];

// Staging area for the two history runs resample_audio() reads (see below).
// Static rather than automatic: at 48 taps it is 376 bytes, which the receive
// task's stack does not need to carry.
static float s_resampleHist[2 * (FILTER_TAPS - 1)];
#endif

// The decimator filters buf[] into the front of buf[] itself: output i lands in
// buf[i] while the taps read the window that ends at buf[i *
// MODEM_RESAMPLE_RATIO]. Almost none of that overlaps, and the proof is worth
// spelling out because it is what keeps a whole block out of .bss.
//
// The samples output i reads from buf[] sit at indices
// [i * MODEM_RESAMPLE_RATIO - (FILTER_TAPS - 1) .. i * MODEM_RESAMPLE_RATIO].
// Take one such index r with r >= FILTER_TAPS - 1 and suppose the loop had
// already overwritten it, that is r < i. The lower bound with
// MODEM_RESAMPLE_RATIO >= 2 gives r >= 2i - (FILTER_TAPS - 1), and r < i gives
// 2i > 2r, so r > 2r - (FILTER_TAPS - 1), i.e. r < FILTER_TAPS - 1 - which
// contradicts the assumption. So every read that CAN land on an already-written
// slot lies below index FILTER_TAPS - 1, and there are at most FILTER_TAPS - 1
// of them, whatever the filter length.
//
// The filter therefore needs two short runs of history and no full-block copy:
// the previous block's tail (s_resampleTail) and this block's own leading
// FILTER_TAPS - 1 samples. They are staged together in s_resampleHist[] so that
// the tap index k walks the conceptual [ previous tail ][ this block ] sequence
// with a single bound test; everything from index FILTER_TAPS - 1 upwards is
// read straight out of buf[], still raw.
_Static_assert(MODEM_RESAMPLE_RATIO >= 2 || FILTER_TAPS == 1,
               "In-place decimation needs MODEM_RESAMPLE_RATIO >= 2: at ratio 1 a multi-tap filter reads its own output.");
_Static_assert(MODEM_BLOCK_SIZE >= 2 * (FILTER_TAPS - 1), "MODEM_BLOCK_SIZE must hold the leading and trailing history runs without them overlapping.");
_Static_assert((MODEM_BLOCK_SIZE % MODEM_RESAMPLE_RATIO) == 0, "MODEM_BLOCK_SIZE must be a whole number of decimated samples.");

static void resample_audio(float *buf) {
#if FILTER_TAPS > 1
    // [ previous block's tail ][ this block's first FILTER_TAPS - 1 samples ]
    float *hist = s_resampleHist;
    memcpy(hist, s_resampleTail, sizeof(s_resampleTail));
    memcpy(hist + (FILTER_TAPS - 1), buf, (FILTER_TAPS - 1) * sizeof(float));

    // Take this block's own tail now, before the decimation loop runs. The
    // loop only ever writes the first MODEM_BLOCK_SIZE / MODEM_RESAMPLE_RATIO
    // slots and so cannot reach these, but reading them up front means the
    // tail no longer depends on where the write pointer stops.
    for (int t = 0; t < FILTER_TAPS - 1; t++)
        s_resampleTail[t] = buf[MODEM_BLOCK_SIZE - (FILTER_TAPS - 1) + t];
#endif

    for (int i = 0; i < MODEM_BLOCK_SIZE / MODEM_RESAMPLE_RATIO; i++) {
        float sum = 0;
#if FILTER_TAPS > 1
        // k indexes the conceptual [ tail ][ block ] sequence; hist[] holds
        // its first 2 * (FILTER_TAPS - 1) entries.
        const int k0 = i * MODEM_RESAMPLE_RATIO;
        int j = 0;
        for (; (j < FILTER_TAPS) && (k0 + j < 2 * (FILTER_TAPS - 1)); j++)
            sum += hist[k0 + j] * resample_coeffs[j];
        const float *in = &buf[k0 - (FILTER_TAPS - 1)];
        for (; j < FILTER_TAPS; j++)
            sum += in[j] * resample_coeffs[j];
#else
        sum = buf[i] * resample_coeffs[0]; // MODEM_RESAMPLE_RATIO == 1, reads and writes the same slot
#endif
        buf[i] = sum;
    }
}

// ------------------------------------------------------------------
// LEDs / PTT
// ------------------------------------------------------------------

static uint8_t r_old = 0, g_old = 0, b_old = 0;
static int64_t rgbTimeout = 0;

// PTT pin is a fixed compile-time constant (::MODEM_PTT_GPIO, an internal
// radiomodem feature - like ::MODEM_ADC_GPIO / ::MODEM_DAC_GPIO it is not
// runtime/web-admin selectable). Its active level is likewise fixed at
// compile time (::MODEM_PTT_ACTIVE_HIGH) and is not a user-facing polarity
// toggle - AFSK_setPttActiveHigh() is only ever called with that same
// compile-time value, from modem_init()/modem_set_modem(), including once
// live per Radio-page Save (aprs_service_apply_modem_config()) as part of
// re-applying the whole modem config.
//
// s_pttActiveHigh is read from setPtt(), which runs from the DAC timer ISR
// (IRAM_ATTR, fires continuously during TX) - so any change to it from task
// context must be made atomic with respect to that ISR. s_pttMux guards
// exactly that variable; it must never be held around gpio_set_level(), which
// is not guaranteed ISR-safe on this target.
//
// DRAM_ATTR: setPtt() reads s_pttGpio from the cache-safe DAC ISR. A plain
// static const lands in flash .rodata, and although the optimizer usually
// folds the value into the code, nothing guarantees it at -Og; kept in DRAM,
// the load stays valid while the flash cache is disabled.
static const DRAM_ATTR int8_t s_pttGpio = MODEM_PTT_GPIO;
static bool s_pttActiveHigh = MODEM_PTT_ACTIVE_HIGH ? true : false;
// When set, setPtt() drives the idle level whatever it is asked for (see
// afskSetPttInhibit()). Guarded by s_pttMux together with s_pttActiveHigh, so
// setPtt() snapshots both in one critical section.
static bool s_pttInhibit = false;
static portMUX_TYPE s_pttMux = portMUX_INITIALIZER_UNLOCKED;

bool afsk_gpio_is_output_capable(int8_t gpio) {
    if (gpio == -1)
        return true; // "disabled" is always accepted
    if (gpio < 0 || gpio > 39)
        return false;
    if (gpio >= 34 && gpio <= 39)
        return false; // input-only, cannot drive an output
    if (gpio >= 6 && gpio <= 11)
        return false; // internal SPI flash/PSRAM, not brought out
    return true;
}

bool afsk_ptt_gpio_is_valid(int8_t gpio) {
    if (gpio == -1)
        return true; // "disabled" is always accepted
    if (!afsk_gpio_is_output_capable(gpio))
        return false;
    if (gpio == MODEM_ADC_GPIO || gpio == MODEM_DAC_GPIO)
        return false; // already used by the audio front end
    return true;
}

void AFSK_setPttActiveHigh(bool active_high) {
    // setPtt() (IRAM ISR, driven by the DAC timer during TX) reads
    // s_pttActiveHigh on every bit and calls gpio_set_level() on the fixed
    // s_pttGpio pin - it does not know a Save is in progress. The pin itself
    // never changes (it is the compile-time ::MODEM_PTT_GPIO constant), so
    // there is no pin swap to sequence here: only the polarity is updated,
    // under the same spinlock setPtt() uses.
    //
    // The idle level is re-driven here only when nothing is transmitting. The
    // DAC-timer ISR already owns the pin throughout TX and re-asserts the
    // correct level (active or idle, per the current s_pttActiveHigh) on every
    // sample via setPtt(), so while TX is active the write is skipped and any
    // change is applied by setPtt() itself on the very next bit.
    portENTER_CRITICAL(&s_pttMux);
    s_pttActiveHigh = active_high;
    portEXIT_CRITICAL(&s_pttMux);

    if (s_inited && s_pttGpio >= 0 && !getTransmit())
        gpio_set_level((gpio_num_t)s_pttGpio, active_high ? 0 : 1);
}

void afskSetPttInhibit(bool inhibit) {
    bool activeHigh;

    portENTER_CRITICAL(&s_pttMux);
    s_pttInhibit = inhibit;
    activeHigh = s_pttActiveHigh;
    portEXIT_CRITICAL(&s_pttMux);

    // Setting the inhibit releases a line that is keyed right now. The DAC
    // ISR only drives the pin at key-up and key-down, so without this write a
    // transmission already under way would stay on the air until it ended.
    // Clearing it writes nothing: the next key-up drives the line itself.
    if (inhibit && s_inited && s_pttGpio >= 0)
        gpio_set_level((gpio_num_t)s_pttGpio, activeHigh ? 0 : 1);
}

// IRAM_ATTR: reachable from dac_timer_isr() (IRAM ISR) via setPtt(), which
// runs setPtt(false) directly from Ax25GetTxBit() at key-down. If this ever
// executes while a concurrent flash op (e.g. LittleFS reading bulletins.json)
// has cache disabled, a flash-resident function here panics with
// "Cache disabled but cached memory region accessed".
void IRAM_ATTR LED_Status2(uint8_t r, uint8_t g, uint8_t b) {
    int64_t now = esp_timer_get_time() / 1000;

    if (r == r_old && g == g_old && b == b_old) {
        // Same state as last time: nothing to drive, just keep pushing the
        // "quiet" window out so a burst of identical calls (e.g. once per
        // transmitted bit) does not repeatedly touch the GPIOs. This must
        // NOT gate genuine transitions below - see the note there.
        rgbTimeout = now + 100;
        return;
    }

    // A genuine state change (this is what setPtt() uses to reflect PTT
    // on/off). A real transition is always applied: packets are transmitted
    // one at a time with a real PTT-off in between (see Ax25TransmitCheck()),
    // and back-to-back packets in a burst can toggle PTT on/off/on again well
    // within 100 ms, so this LED (and anything wired the same way, e.g. a PTT
    // relay) must follow the real GPIO, which is driven separately by
    // setPtt(). Only the 100 ms window before the NEXT transition is rate-
    // limited, and only for repeats of this same new state.
    rgbTimeout = now + 100;
    r_old = r;
    g_old = g;
    b_old = b;

#if MODEM_LED_TX_GPIO >= 0
    gpio_ll_set_level(&GPIO, (uint32_t)MODEM_LED_TX_GPIO, r > 0);
#endif
#if MODEM_LED_RX_GPIO >= 0
    gpio_ll_set_level(&GPIO, (uint32_t)MODEM_LED_RX_GPIO, g > 0);
#endif
}

// IRAM_ATTR: called from dac_timer_isr() -> MODEM_BAUDRATE_TIMER_HANDLER() ->
// Ax25GetTxBit() at key-down (setPtt(false)), same ISR context as the rest of
// the TX path. Must stay flash-cache-safe for the same reason as
// LED_Status2() above.
void IRAM_ATTR setPtt(bool state) {
    // s_pttGpio is a compile-time constant (::MODEM_PTT_GPIO), so only the
    // polarity and the inhibit need to be snapshotted under the spinlock
    // AFSK_setPttActiveHigh() and afskSetPttInhibit() use - short enough to be
    // fine from IRAM/ISR context, and it can never observe a half-applied
    // change. The TX LED follows the line as actually driven.
    portENTER_CRITICAL_ISR(&s_pttMux);
    bool activeHigh = s_pttActiveHigh;
    bool keyed = state && !s_pttInhibit;
    portEXIT_CRITICAL_ISR(&s_pttMux);

    if (s_pttGpio >= 0)
        gpio_ll_set_level(&GPIO, (uint32_t)s_pttGpio, activeHigh ? keyed : !keyed);
    if (keyed)
        LED_Status2(255, 0, 0);
    else
        LED_Status2(0, 0, 0);
}

bool IRAM_ATTR getTransmit(void) {
    return __atomic_load_n(&s_txActive, __ATOMIC_ACQUIRE);
}

bool AFSK_TxTeardownPending(void) {
    return __atomic_load_n(&s_txStopPending, __ATOMIC_ACQUIRE);
}

// @brief Key up / key down.
//
// setTransmit(true) is only ever reached from ModemTransmitStart(), i.e. task
// context, so the timer may be started here. setTransmit(false) is reached from
// the DAC ISR via Ax25GetTxBit() -> ModemTransmitStop(), so it must do nothing
// more than lower a flag; AFSK_ServiceTx() finishes the job from a task.
void IRAM_ATTR setTransmit(bool val) {
    if (val) {
        if (!getTransmit()) {
            __atomic_store_n(&s_txStopPending, false, __ATOMIC_RELEASE);
            // Release: the transmit state the caller prepared (stage, first
            // byte, CRC seed) is visible to the DAC ISR before it sees the
            // transmitter active.
            __atomic_store_n(&s_txActive, true, __ATOMIC_RELEASE);
            if (s_dacTimer && !s_dacTimerRunning) {
                gptimer_start(s_dacTimer);
                s_dacTimerRunning = true;
            }
        }
    } else {
        // The pending teardown is raised before the transmitting flag is
        // cleared, never after. Whoever sees the transmitter idle therefore
        // also sees the teardown it still owes, so Ax25TransmitCheck() cannot
        // take the gap between the two for a finished key-down and key up a
        // new frame whose setTransmit(true) this call would then undo.
        __atomic_store_n(&s_txStopPending, true, __ATOMIC_RELEASE);
        __atomic_store_n(&s_txActive, false, __ATOMIC_RELEASE);
        // Drop the PTT GPIO right here, at key-down. This is the only teardown
        // step that is safe to run from the DAC ISR: setPtt() is IRAM_ATTR and
        // does nothing heavier than a spinlock-guarded gpio_set_level() (the
        // status LED it also touches is compiled out when MODEM_LED_*_GPIO are
        // -1). The rest of the teardown - stopping the DAC sample timer,
        // parking the DAC, flushing the RX FIFO - is NOT ISR-safe and stays
        // deferred to AFSK_ServiceTx() via s_txStopPending above.
        //
        // The pin drop must NOT be deferred with it: AFSK_ServiceTx() runs at
        // most once per service-task period (>= 1 tick) and behind an unbounded
        // RX-drain loop, so deferring the pin would leave the PTT line
        // physically asserted for up to a whole tick after the transmitter had
        // already stopped modulating (s_txActive == false), letting "PTT OFF
        // (unkeyed)" be reached while the pin was still keyed. Releasing it
        // here keeps the physical PTT in lock-step with key-down. The
        // idempotent setPtt(false) in AFSK_ServiceTx() re-asserts the idle
        // level as a belt-and-suspenders measure.
        setPtt(false);
    }
}

void afskSetFullDuplex(bool enable) {
    s_fullDuplex = enable;
    Ax25Config.fullDuplex = enable ? 1 : 0;
}

bool afskGetFullDuplex(void) {
    return s_fullDuplex;
}

void afskSetRxFrontEnd(uint16_t gateMv, uint16_t hpfHz, bool agcFixed, int8_t fixedGainDb, bool impulseBlank) {
    s_pendBlank = impulseBlank;
    s_pendGateMv = gateMv;
    s_pendHpfHz = hpfHz;
    s_pendAgcFixed = agcFixed;
    s_pendFixedGainDb = fixedGainDb;
}

uint32_t afskGetFifoDrops(void) {
    return s_fifoDrops;
}

uint32_t afskGetPoolOverflows(void) {
    return s_poolOvf;
}

void afskResetRxCounters(void) {
    s_fifoDrops = 0;
    s_poolOvf = 0;
    s_dspMaxUs = 0;
    s_blanker.repaired = 0;
}

uint32_t afskGetImpulsesRepaired(void) {
    return s_blanker.repaired;
}

// @brief Busy time of one block, in microseconds, as thousandths of the
//        block's audio duration, saturated to the uint16_t range.
static uint16_t dsp_permille(uint32_t busyUs) {
    uint64_t v = ((uint64_t)busyUs * 1000u) / DSP_BLOCK_US;
    return (uint16_t)((v > UINT16_MAX) ? UINT16_MAX : v);
}

void afskGetDspLoad(uint16_t *meanPermille, uint16_t *peakPermille, uint16_t *maxPermille) {
    uint32_t blocks = s_dspBlocks;
    uint32_t sum = s_dspBusySumUs;
    uint32_t peak = s_dspPeakUs;
    uint32_t max = s_dspMaxUs;

    s_dspWindowReset = true;

    // A block held up by a reconfiguration of the modem can read far above
    // real time; the figures saturate rather than wrap.
    if (meanPermille)
        *meanPermille = dsp_permille((blocks > 0) ? sum / blocks : 0);
    if (peakPermille)
        *peakPermille = dsp_permille(peak);
    if (maxPermille)
        *maxPermille = dsp_permille(max);
}

esp_err_t afskSetDacSampleRate(uint32_t rate) {
    if (s_inited)
        return ESP_ERR_INVALID_STATE;

    // The modulator puts one symbol edge on a whole number of DAC samples at
    // every supported baud rate, and ModemInit() derives the divider by integer
    // division, so a rate that is not a multiple of 9600 desynchronizes the
    // 9600 Bd profile and a rate that is not a multiple of 1200 desynchronizes
    // the AFSK ones.
    if ((rate == 0) || ((rate % 9600) != 0) || ((rate % 1200) != 0))
        return ESP_ERR_INVALID_ARG;

    s_dacRate = rate;
    return ESP_OK;
}

uint32_t afskGetDacSampleRate(void) {
    return s_dacRate;
}

void afskSetDacAmplitude(uint8_t pct) {
    if (pct < 1)
        pct = 1;
    else if (pct > 100)
        pct = 100;

    s_dacAmplitudePct = pct;
}

uint8_t afskGetDacAmplitude(void) {
    return s_dacAmplitudePct;
}

esp_err_t afskSetAdcSelfBias(bool enable) {
#if (MODEM_ADC_GPIO == 32) || (MODEM_ADC_GPIO == 33)
    esp_err_t err;

    if (enable) {
        err = rtc_gpio_pullup_en((gpio_num_t)MODEM_ADC_GPIO);
        if (err == ESP_OK)
            err = rtc_gpio_pulldown_en((gpio_num_t)MODEM_ADC_GPIO);
    } else {
        err = rtc_gpio_pullup_dis((gpio_num_t)MODEM_ADC_GPIO);
        if (err == ESP_OK)
            err = rtc_gpio_pulldown_dis((gpio_num_t)MODEM_ADC_GPIO);
    }

    if (err != ESP_OK) {
        ESP_LOGE(TAG, "ADC input self-bias on GPIO%d: %s", MODEM_ADC_GPIO, esp_err_to_name(err));
        return err;
    }

    s_adcSelfBias = enable;
    ESP_LOGI(TAG, "ADC input self-bias %s on GPIO%d", enable ? "enabled" : "disabled", MODEM_ADC_GPIO);
    return ESP_OK;
#else
    // GPIO34-39 are input-only pads and carry no pull resistors at all, so an
    // AC-coupled input on one of them can only be biased externally.
    if (!enable) {
        s_adcSelfBias = false;
        return ESP_OK;
    }

    ESP_LOGE(TAG, "ADC input self-bias is not available on GPIO%d: that pad has no internal pull resistors", MODEM_ADC_GPIO);
    return ESP_ERR_NOT_SUPPORTED;
#endif
}

bool afskGetAdcSelfBias(void) {
    return s_adcSelfBias;
}

void afskSetClipWarn(bool enable) {
    s_clipWarn = enable;
}

void afskGetRawMinMax(int16_t *min, int16_t *max) {
    if (min)
        *min = s_rawMin;
    if (max)
        *max = s_rawMax;
}

uint16_t afskGetRms(void) {
    return (uint16_t)s_mVrms;
}

uint16_t afskGetBandRms(void) {
    return (uint16_t)s_bandMvRms;
}

uint32_t afskGetAdcSampleCount(void) {
    return s_adcSamples;
}

int afskGetDcOffset(void) {
    return s_offset;
}

float afskGetAgcGain(void) {
    return s_agcGain;
}

float afskGetDacAlarmRate(void) {
    return s_dacAlarmRateHz;
}

int afskDiagCaptureRaw(int16_t *dst, int n, uint32_t timeout_ms) {
    if ((dst == NULL) || (n <= 0))
        return 0;
    if (n > AFSK_DIAG_CAP_SAMPLES)
        n = AFSK_DIAG_CAP_SAMPLES;

    s_capRawIdx = 0;
    s_capRawLen = n; // arms the tap

    uint32_t waited = 0;
    while ((s_capRawIdx < n) && (waited < timeout_ms)) {
        vTaskDelay(pdMS_TO_TICKS(5) ? pdMS_TO_TICKS(5) : 1);
        waited += 5;
    }

    // Disarm first, then let one FIFO drain pass go by before reading the
    // sample count, so a producer already past its bounds test has finished
    // its store and the copy below sees a settled buffer.
    s_capRawLen = 0;
    vTaskDelay(pdMS_TO_TICKS(5) ? pdMS_TO_TICKS(5) : 1);

    int got = s_capRawIdx;
    if (got > n)
        got = n;
    if (got > 0)
        memcpy(dst, s_capBuf, (size_t)got * sizeof(s_capBuf[0]));
    return got;
}

// ------------------------------------------------------------------
// DAC timer ISR
// ------------------------------------------------------------------

// Why the sample ISR writes the DAC register directly.
//
// dac_oneshot_output_voltage() is ISR safe in the sense that matters for
// correctness - a NULL check and one register write inside
// DAC_RTC_ENTER_CRITICAL_SAFE(), no logging - but it lives in FLASH. Every call
// from this ISR is a potential instruction-cache miss, and an XIP fetch off the
// SPI flash costs tens of microseconds. That is not a rate error: the GPTimer
// alarm is scheduled on an absolute count, so a late ISR emits one sample late
// and the next is back on schedule. It is pure jitter on the transmitted edge,
// which is why stage 2 reports "missed alarms +0.00 %" while also reporting a
// 38 us worst-case gap against a 26.0 us period - about 12 us of excess.
//
// 12 us is 1.4 % of a Bell202 symbol and the AFSK profiles never notice it. It
// is 12 % of a G3RUH symbol (104 us, four DAC samples), and a symbol edge that
// moves by 12 % of a symbol is a bit error waiting for the descrambler to
// triple it. Host simulation puts the cost at roughly one frame in eight at 12
// us, against zero for every AFSK profile.
//
// dac_ll_update_output_value() is a static inline in a HAL header, so it
// compiles into this IRAM_ATTR ISR and the flash round trip disappears. Only
// this ISR touches the DAC while the timer is running - AFSK_ServiceTx() writes
// the idle code only after TX has stopped - so dropping the driver's critical
// section here does not race anything.
#if CONFIG_IDF_TARGET_ESP32
#include "hal/dac_ll.h"
static inline void IRAM_ATTR dac_write_isr(uint8_t code) {
    dac_ll_update_output_value(MODEM_DAC_CHANNEL, code);
}
#else
static inline void dac_write_isr(uint8_t code) {
    dac_oneshot_output_voltage(s_dac, code);
}
#endif

static bool IRAM_ATTR dac_timer_isr(gptimer_handle_t timer, const gptimer_alarm_event_data_t *edata, void *user_ctx) {
    (void)timer;
    (void)edata;
    (void)user_ctx;

    if (getTransmit()) {
        uint8_t sinwave = MODEM_BAUDRATE_TIMER_HANDLER();
        // The key-down happens inside the handler. From then on the DAC
        // belongs to AFSK_ServiceTx(), which parks it at mid-scale, so the
        // sample computed on the way out is not written.
        if (getTransmit())
            dac_write_isr(dac_scale(sinwave));
    }
    return false;
}

// @brief Deferred TX teardown. Must run in task context.
void AFSK_ServiceTx(void) {
    if (!AFSK_TxTeardownPending())
        return;

    // The teardown is raised before the transmitting flag is cleared, so on
    // the other core the DAC ISR may still be finishing the key-down. It is
    // left to complete; the next service tick carries out the teardown.
    if (getTransmit())
        return;

    // s_txStopPending is cleared only after the teardown work below (and
    // setPtt(false) in particular) has run. Every reader of "is teardown
    // done" - ModemTxTeardownPending() / AFSK_TxTeardownPending(), which gate
    // the next key-up in Ax25TransmitCheck() - takes s_txStopPending == false
    // as proof that the sample clock is stopped and the PTT GPIO released.
    // Clearing the flag last means nothing can observe "teardown done" before
    // that is true.

    if (s_dacTimer && s_dacTimerRunning) {
        gptimer_stop(s_dacTimer);
        s_dacTimerRunning = false;
    }
    if (s_dac)
        dac_oneshot_output_voltage(s_dac, DAC_MID); // park the output at mid-scale

    // Half duplex only: the samples captured while we were keyed up are our own
    // transmission leaking back in, so throw them away. In full duplex the tail
    // of our own frame is still in the FIFO and must be demodulated - that is
    // exactly what the GPIO ADC -> GPIO DAC loopback test relies on.
    //
    // The carrier detect is cleared with it for the same reason: adc_ingest()
    // kept every sample of the key-up away from the demodulators, so their DCD
    // still describes the channel as it was before this station keyed up. In
    // full duplex the demodulators heard the whole transmission and their DCD
    // is current, and resetting it would disturb the frame still being
    // decoded from the FIFO.
    if (!s_fullDuplex) {
        AFSK_FlushFifo();
        s_dcdResetReq = true;
    }

    setPtt(false);
    __atomic_store_n(&s_txStopPending, false, __ATOMIC_RELEASE); // only now is teardown actually complete
    ESP_LOGD(TAG, "TX stopped");
}

// ------------------------------------------------------------------
// ADC
// ------------------------------------------------------------------

// @brief ADC conversion-done callback.
//
// This runs in interrupt context and is therefore allowed to do exactly one
// thing: count. Every microsecond spent here is a microsecond the DAC timer may
// not get, and the modulator cannot survive a blackout longer than about 100 us
// (see the ring buffer notes at the top of this file). Copying the samples out
// is left to afsk_rx_task, which runs at task level.
//
// The count is kept here rather than in adc_ingest() on purpose: it must report
// the true hardware rate to modem_measure_adc_rate() even if the DSP task
// falls behind and the driver drops a frame from the pool.
static bool IRAM_ATTR adc_conv_done_cb(adc_continuous_handle_t handle, const adc_continuous_evt_data_t *edata, void *user_data) {
    (void)handle;
    (void)user_data;
    s_adcSamples += edata->size / SOC_ADC_DIGI_RESULT_BYTES;
    return false;
}

// @brief ADC pool-overflow callback: the driver discarded conversion frames
//        because afsk_rx_task did not read them in time. Counted only.
static bool IRAM_ATTR adc_pool_ovf_cb(adc_continuous_handle_t handle, const adc_continuous_evt_data_t *edata, void *user_data) {
    (void)handle;
    (void)edata;
    (void)user_data;
    s_poolOvf++;
    return false;
}

// The ESP32 hands back the two results in each 32-bit DMA word in the wrong
// order, and the FIFO must undo it.
//
// On this chip the ADC is clocked through I2S0, which packs two 16-bit results
// into one 32-bit DMA word and writes them out low half last. The sample stream
// therefore arrives with every adjacent PAIR exchanged: t1 t0 t3 t2 t5 t4. It is
// a fixed, known reordering, not a rate error.
//
// The three AFSK profiles are immune to it. They are demodulated at 9600 Hz, so
// the MODEM_ADC_SAMPLERATE -> 9600 decimation FIR averages each swapped pair
// back together before the correlator ever sees it: exchanging two samples
// inside a filter window does not change the window's output by anything the
// correlator can measure.
//
// G3RUH is not decimated - it cannot be, its own bandwidth IS the anti-alias
// cutoff - so it is handed the raw stream, MODEM_ADC_SAMPLERATE / 9600 samples
// per symbol, with nothing in between to average the swap away. Whether that is survivable
// depends on where the DMA word boundary happens to fall relative to the symbol
// boundary:
//
//   pairs inside a symbol   [t0 t1][t2 t3]  -> harmless, both samples belong
//                                              to the same symbol
//   pairs across a symbol   t0[t1 t2][t3 t4] -> fatal: the last sample of one
//                                              symbol and the first of the next
//                                              trade places, so every symbol
//                                              edge moves by +/-1 sample = +/-90
//                                              degrees of symbol clock, and the
//                                              DPLL is chasing an edge that
//                                              zig-zags either side of where the
//                                              symbol actually changed
//
// Nothing aligns those two boundaries. The DMA frame start bears no relation to
// the transmitter's symbol phase, and the ADC and DAC timers are independent
// and differ by a few hundredths of a percent, so the alignment slips one
// sample every few tens of milliseconds and walks through the fatal phase
// several times during a single frame.
// One burst of bad bits is enough to fail the FCS, so without the un-swap the
// G3RUH profile decodes nothing while the AFSK profiles are unaffected.
//
// Un-swap here, at ingest, so everything downstream - every demodulator, the
// AGC, the DC tracker and afskDiagCaptureRaw() - sees samples in true time
// order. Doing it here rather than in the G3RUH branch keeps stage 3 of the
// diagnostics honest: it measures this FIFO's output, so if the un-swap is ever
// wrong or is skipped on a future target, stage 3 reports "pair-swapped"
// instead of leaving G3RUH to fail silently.
//
// ESP32 only. The S2/S3 ADC does not go through I2S and returns 4-byte results
// in order.
#if CONFIG_IDF_TARGET_ESP32
#define MODEM_ADC_DMA_PAIR_SWAP 1
#else
#define MODEM_ADC_DMA_PAIR_SWAP 0
#endif

// @brief Parse one conversion frame into the sample FIFO. Task context.
#if MODEM_ADC_DMA_PAIR_SWAP
// adc_continuous_read() may hand back a partial frame (see the reassembly
// note above afsk_rx_task), which can make `entries` below odd. A leftover
// last entry is not passed through on its own: its real word partner is the
// FIRST entry of the NEXT call, which has not arrived yet. It is held in
// s_pendingSwap and paired with that entry when the next read comes in, so
// the un-swap always follows the true DMA word boundary across reads instead
// of slipping by one sample on an odd-length read.
static bool s_havePendingSwap = false;
static adc_digi_output_data_t s_pendingSwap;
#endif

// Feed one raw sample to the diagnostic tap. The index is read once into a
// local so the bounds test and the store use the same value, and the bound is
// s_capRawLen, which never exceeds AFSK_DIAG_CAP_SAMPLES: the store is in range
// even if the consumer disarms the tap in between.
static inline void diag_capture_push(int16_t raw) {
    int idx = s_capRawIdx;

    if (idx < s_capRawLen) {
        s_capBuf[idx] = raw;
        s_capRawIdx = idx + 1;
    }
}

static void adc_ingest(const uint8_t *buf, uint32_t size) {
    // Half duplex: do not fill the FIFO while transmitting, otherwise the
    // garbage captured during TX corrupts the demodulator state when drained.
    if (!s_fullDuplex && getTransmit())
        return;

    uint32_t head = s_fifo.head;
    const uint32_t entries = size / SOC_ADC_DIGI_RESULT_BYTES;
    uint32_t start = 0;

#if MODEM_ADC_DMA_PAIR_SWAP
    if (s_havePendingSwap) {
        // s_pendingSwap is the LATER sample of a word whose EARLIER sample
        // is the first entry of this call (if any arrived at all). Emit
        // them in true chronological order: earlier, then later.
        if (entries > 0) {
            adc_digi_output_data_t *earlier = (adc_digi_output_data_t *)&buf[0];

            if (earlier->type1.channel == MODEM_ADC_CHANNEL) {
                if ((head - s_fifo.tail) < MODEM_RX_FIFO_SIZE) {
                    int16_t raw = (int16_t)earlier->type1.data;
                    s_fifo.buffer[head & RB_MASK] = raw;
                    s_fifo.head = ++head;
                    diag_capture_push(raw);
                } else {
                    s_fifoDrops++;
                }
            }
            if (s_pendingSwap.type1.channel == MODEM_ADC_CHANNEL) {
                if ((head - s_fifo.tail) < MODEM_RX_FIFO_SIZE) {
                    int16_t raw = (int16_t)s_pendingSwap.type1.data;
                    s_fifo.buffer[head & RB_MASK] = raw;
                    s_fifo.head = ++head;
                    diag_capture_push(raw);
                } else {
                    s_fifoDrops++;
                }
            }
            start = 1; // buf[0] already consumed above
        }
        // If entries == 0 the pending entry simply waits for the next call;
        // it is not dropped.
        s_havePendingSwap = false;
    }
#endif

    for (uint32_t i = start; i < entries; i++) {
        uint32_t n = i;

#if MODEM_ADC_DMA_PAIR_SWAP
        // rel is this entry's position measured from the last confirmed
        // word boundary (start), not from the start of the raw buffer, so
        // a partial previous call can never desync the pairing.
        uint32_t rel = i - start;

        if ((rel & 1u) == 0u) {
            if (i + 1 < entries) {
                n = i + 1;
            } else {
                // Genuinely unpaired tail: hold it for the next call rather
                // than emitting it unswapped.
                s_pendingSwap = *(const adc_digi_output_data_t *)&buf[i * SOC_ADC_DIGI_RESULT_BYTES];
                s_havePendingSwap = true;
                continue;
            }
        } else {
            n = i - 1;
        }
#endif

        adc_digi_output_data_t *p = (adc_digi_output_data_t *)&buf[n * SOC_ADC_DIGI_RESULT_BYTES];

        if (p->type1.channel != MODEM_ADC_CHANNEL)
            continue;

        if ((head - s_fifo.tail) >= MODEM_RX_FIFO_SIZE) {
            s_fifoDrops++; // overrun: drop rather than corrupt
            continue;
        }

        int16_t raw = (int16_t)p->type1.data;
        s_fifo.buffer[head & RB_MASK] = raw;
        s_fifo.head = ++head;

        diag_capture_push(raw);
    }
}

static esp_err_t adc_start_continuous(void) {
    // conv_frame_size is NOT MODEM_BLOCK_SIZE, on purpose. It is the length
    // of the memcpy the IDF's ADC ISR performs inside portENTER_CRITICAL_ISR(),
    // and therefore the length of time the DAC sample clock is masked on that
    // core - see the ring buffer notes at the top of this file. Small frames,
    // deep pool; AFSK_Poll() reassembles MODEM_BLOCK_SIZE blocks from the
    // FIFO downstream.
    uint32_t conv_frame_size = (uint32_t)MODEM_ADC_CONV_FRAME_BYTES;

    adc_continuous_handle_cfg_t handleCfg = {
        .max_store_buf_size = conv_frame_size * MODEM_ADC_POOL_FRAMES,
        .conv_frame_size = conv_frame_size,
    };
#if ESP_IDF_VERSION >= ESP_IDF_VERSION_VAL(5, 2, 0)
    handleCfg.flags.flush_pool = true;
#endif

    esp_err_t err = adc_continuous_new_handle(&handleCfg, &s_adc);
    if (err != ESP_OK) {
        ESP_LOGE(TAG, "adc_continuous_new_handle: %s", esp_err_to_name(err));
        return err;
    }

    adc_digi_pattern_config_t pattern = {
        .atten = MODEM_ADC_ATTEN,
        .channel = MODEM_ADC_CHANNEL,
        .unit = ADC_UNIT_1,
        .bit_width = SOC_ADC_DIGI_MAX_BITWIDTH,
    };

    adc_continuous_config_t cfg = {
        .sample_freq_hz = (uint32_t)MODEM_ADC_SAMPLERATE * MODEM_ADC_RATE_NUM / MODEM_ADC_RATE_DEN,
        .conv_mode = ADC_CONV_SINGLE_UNIT_1,
        .format = ADC_DIGI_OUTPUT_FORMAT_TYPE1,
        .pattern_num = 1,
        .adc_pattern = &pattern,
    };

    err = adc_continuous_config(s_adc, &cfg);
    if (err != ESP_OK) {
        ESP_LOGE(TAG, "adc_continuous_config: %s", esp_err_to_name(err));
        return err;
    }
    ESP_LOGI(TAG, "ADC1 CH%d (GPIO%d) requested %" PRIu32 " Hz -> nominal %d Hz", (int)MODEM_ADC_CHANNEL, MODEM_ADC_GPIO, cfg.sample_freq_hz,
             MODEM_ADC_SAMPLERATE);
    // Print the frame size in the unit that matters. The driver's ISR copies
    // this many bytes with interrupts masked to level 3; if the DAC clock ever
    // shares this core again, that is its worst-case freeze.
    ESP_LOGI(TAG, "ADC DMA: %d samples/frame (%d B, %.2f ms), pool %d frames (%.1f ms), ISR on core %d", MODEM_ADC_CONV_FRAME, MODEM_ADC_CONV_FRAME_BYTES,
             1000.0 * MODEM_ADC_CONV_FRAME / (double)MODEM_ADC_SAMPLERATE, MODEM_ADC_POOL_FRAMES,
             1000.0 * MODEM_ADC_CONV_FRAME * MODEM_ADC_POOL_FRAMES / (double)MODEM_ADC_SAMPLERATE, MODEM_ADC_ISR_CORE);

    adc_continuous_evt_cbs_t cbs = { .on_conv_done = adc_conv_done_cb, .on_pool_ovf = adc_pool_ovf_cb };
    err = adc_continuous_register_event_callbacks(s_adc, &cbs, NULL);
    if (err != ESP_OK) {
        ESP_LOGE(TAG, "adc_continuous_register_event_callbacks: %s", esp_err_to_name(err));
        return err;
    }

    adc_cali_line_fitting_config_t caliCfg = {
        .unit_id = ADC_UNIT_1,
        .atten = MODEM_ADC_ATTEN,
        .bitwidth = ADC_BITWIDTH_12,
    };
    err = adc_cali_create_scheme_line_fitting(&caliCfg, &s_cali);
    if (err != ESP_OK) {
        ESP_LOGE(TAG, "adc_cali_create_scheme_line_fitting: %s", esp_err_to_name(err));
        return err;
    }

    // Slope of the calibration line, for the tone-band meter, which works in
    // ADC counts. Measured between two codes well inside the linear part of
    // the range.
    int mvLo = 0, mvHi = 0;
    if ((adc_cali_raw_to_voltage(s_cali, 1000, &mvLo) == ESP_OK) && (adc_cali_raw_to_voltage(s_cali, 3000, &mvHi) == ESP_OK) && (mvHi > mvLo))
        s_mvPerCount = (float)(mvHi - mvLo) / 2000.0f;

    return adc_continuous_start(s_adc);
}

// ------------------------------------------------------------------
// RX DSP
// ------------------------------------------------------------------

void AFSK_Poll(void) {
    int16_t adc = 0;
    int mV = 0;
    long mVsum = 0;
    int mVsumCount = 0;

    for (;;) {
        // Only the consumer may move tail, so a flush requested by another task
        // is executed here, between blocks.
        if (s_flushReq) {
            s_flushReq = false;
            s_fifo.tail = s_fifo.head;
        }
        if (s_dcdResetReq) {
            s_dcdResetReq = false;
            ModemResetDcd();
        }

        if (rb_size(&s_fifo) < (uint32_t)MODEM_BLOCK_SIZE)
            break;

        const int64_t blockStartUs = esp_timer_get_time();

        mVsum = 0;
        mVsumCount = 0;

        int16_t rawMin = INT16_MAX;
        int16_t rawMax = INT16_MIN;

        // The blanker only runs for the decimated profiles: G3RUH's baseband
        // changes too fast between conversions for a glitch to stand out.
        const bool blank = s_blankOn && (ModemConfig.modem != MODEM_MODEM_G3RUH) && (MODEM_RESAMPLE_RATIO > 1);
        const uint32_t repairedBefore = s_blanker.repaired;

        // The RMS/level measurement only needs a fraction of the samples.
        int m = ((MODEM_RESAMPLE_RATIO > 1) || (ModemConfig.modem == MODEM_MODEM_G3RUH)) ? 4 : 1;

        for (int x = 0; x < MODEM_BLOCK_SIZE; x++) {
            if (!rb_pop(&s_fifo, &adc))
                break;

            // Glitches are removed before anything else sees the sample: the
            // DC tracker, the level and headroom figures, and the decimator
            // that would spread a glitch over the whole tone band.
            adc = impulse_blanker_step(&s_blanker, adc, blank);

            if (adc < rawMin)
                rawMin = adc;
            if (adc > rawMax)
                rawMax = adc;

            const float adcVal = rx_dc_block_step(&s_dcBlock, adc);

            if (x % m == 0) {
                adc_cali_raw_to_voltage(s_cali, adc, &mV);
                mV -= s_offset;
                mVsum += (long)mV * mV; // Vrms = sqrt(1/n * sum(Vi^2))
                mVsumCount++;
            }

            s_audio[x] = adcVal / 2048.0f;
        }

        adc_cali_raw_to_voltage(s_cali, rx_dc_block_level(&s_dcBlock), &s_offset);

        if (rawMin <= rawMax) {
            s_rawMin = rawMin;
            s_rawMax = rawMax;

            if (s_clipWarn && ((rawMax >= AFSK_RAW_CLIP_HIGH) || (rawMin <= AFSK_RAW_CLIP_LOW))) {
                uint32_t now = (uint32_t)(esp_timer_get_time() / 1000);

                // Signed difference against a deadline, so the hold survives the
                // wrap of the millisecond counter.
                if ((int32_t)(s_clipNextWarnMs - now) <= 0) {
                    s_clipNextWarnMs = now + CLIP_WARN_HOLD_MS;
                    ESP_LOGW(TAG, "RX audio is over-range (raw %d..%d of 0..4095) - lower the receive level trimmer or the transceiver volume", rawMin, rawMax);
                }
            }
        }

        if (mVsumCount > 0)
            s_mVrms = (int)sqrtf((float)(mVsum / mVsumCount));

        // G3RUH is the one profile that is NOT decimated.
        //
        // The AFSK profiles are demodulated at MODEM_DEMOD_SAMPLERATE (9600 Hz),
        // so the MODEM_ADC_SAMPLERATE stream is low-pass filtered and decimated
        // by MODEM_RESAMPLE_RATIO first. G3RUH runs at 9600 Bd: decimating to
        // 9600 Hz would leave exactly one sample per symbol, which gives the
        // DPLL nothing to recover a clock from and puts the symbol rate at
        // Nyquist. Its demodulator is built for the raw MODEM_ADC_SAMPLERATE
        // stream instead - MODEM_RESAMPLE_RATIO samples per symbol, which is
        // what N9600 and the lpf9600 coefficients in modem.c are cut for.
        //
        // The anti-alias filter and the high-pass are skipped with it,
        // deliberately: the decimator's 3500 Hz cutoff sits well inside
        // G3RUH's own bandwidth, and a baseband NRZ signal carries energy
        // down to DC.
        //
        // The decimator and the high-pass run on every block, gate open or
        // not, so their history is current whenever the gate opens.
        const bool decimate = (ModemConfig.modem != MODEM_MODEM_G3RUH) && (MODEM_RESAMPLE_RATIO > 1);
        const int count = decimate ? RX_DECIM_SAMPLES : MODEM_BLOCK_SIZE;

        if (decimate) {
            resample_audio(s_audio);
            rx_hpf_run(&s_hpf, s_audio, count);
            s_bandMvRms = (int)(band_meter_run(s_audio, count) * s_mvPerCount + 0.5f);
        } else {
            s_bandMvRms = s_mVrms;
        }

        // The gate follows the tone band, so hum or bass alone cannot hold it
        // open and a quiet tone under a loud low end still opens it.
        if (s_gateOnMv > 0) {
            if (s_bandMvRms > (int)s_gateOnMv) {
                if (s_dcdCnt < 100)
                    s_dcdCnt++;
            } else if (s_bandMvRms < (int)s_gateOffMv) {
                if (s_dcdCnt > 0)
                    s_dcdCnt--;
            }
        }

        bool signalPresent = (s_gateOnMv == 0) || (s_dcdCnt > 3) || (ModemConfig.modem == MODEM_MODEM_G3RUH);

        // The demodulators only update their carrier detect on the samples
        // they are fed. Once the gate closes they are fed nothing, so a lock
        // taken on the last blocks before it closed - often the noise that
        // follows a transmission while the gate level decays - would
        // otherwise keep reporting a busy channel for as long as it stays
        // quiet.
        if (s_gateOpen && !signalPresent)
            ModemResetDcd();
        s_gateOpen = signalPresent;

        if (signalPresent) {
            // Track the level only while there is something to track, and
            // before feeding, so the block that opened the gate is already
            // demodulated at the new gain.
            if (!s_agcFixed)
                update_agc(s_audio, (size_t)count);

            if (decimate && (s_holdCount > 0))
                hold_flush(count);
            demod_feed(s_audio, count);
        } else if (decimate) {
            hold_push(s_audio, count);
        }

        if (s_dspWindowReset || (s_dspBlocks >= DSP_WINDOW_MAX_BLOCKS)) {
            s_dspWindowReset = false;
            s_dspBusySumUs = 0;
            s_dspBlocks = 0;
            s_dspPeakUs = 0;
        }
        uint32_t busyUs = (uint32_t)(esp_timer_get_time() - blockStartUs);
        s_dspBusySumUs += busyUs;
        s_dspBlocks++;
        if (busyUs > s_dspPeakUs)
            s_dspPeakUs = busyUs;
        if (busyUs > s_dspMaxUs)
            s_dspMaxUs = busyUs;

        if (decimate)
            capture_block(s_audio, rawMin, rawMax, busyUs, signalPresent, s_blanker.repaired != repairedBefore);
    }
}

esp_err_t afskCaptureStart(uint32_t slots) {
    if ((slots < 4) || (slots > 1000))
        return ESP_ERR_INVALID_ARG;
    if ((s_capRing != NULL) || (ModemConfig.modem == MODEM_MODEM_G3RUH) || (MODEM_RESAMPLE_RATIO <= 1))
        return ESP_ERR_INVALID_STATE;

    afsk_capture_block_t *ring = (afsk_capture_block_t *)malloc(slots * sizeof(afsk_capture_block_t));
    if (ring == NULL)
        return ESP_ERR_NO_MEM;

    s_capSlots = slots;
    s_capHead = 0;
    s_capTail = 0;
    s_capSeq = 0;
    s_capDropped = 0;
    __atomic_store_n(&s_capRing, ring, __ATOMIC_RELEASE);
    return ESP_OK;
}

bool afskCaptureRead(afsk_capture_block_t *out) {
    afsk_capture_block_t *ring = __atomic_load_n(&s_capRing, __ATOMIC_ACQUIRE);
    if (ring == NULL)
        return false;

    uint32_t tail = s_capTail;
    if (__atomic_load_n(&s_capHead, __ATOMIC_ACQUIRE) == tail)
        return false;

    memcpy(out, &ring[tail % s_capSlots], sizeof(*out));
    __atomic_store_n(&s_capTail, tail + 1, __ATOMIC_RELEASE);
    return true;
}

uint32_t afskCaptureStop(void) {
    afsk_capture_block_t *ring = __atomic_exchange_n(&s_capRing, NULL, __ATOMIC_ACQ_REL);
    if (ring != NULL) {
        // One block takes at most a few milliseconds; this covers a block
        // that picked up the pointer just before it was cleared.
        vTaskDelay(pdMS_TO_TICKS(100));
        free(ring);
    }
    return s_capDropped;
}

// @brief Append the block just processed to the receive capture, if one runs.
static void capture_block(const float *audio, int16_t rawMin, int16_t rawMax, uint32_t busyUs, bool gateOpen, bool blanked) {
    afsk_capture_block_t *ring = __atomic_load_n(&s_capRing, __ATOMIC_ACQUIRE);
    if (ring == NULL)
        return;

    uint32_t seq = s_capSeq++;
    uint32_t head = s_capHead;
    if ((head - __atomic_load_n(&s_capTail, __ATOMIC_ACQUIRE)) >= s_capSlots) {
        s_capDropped++;
        return;
    }

    afsk_capture_block_t *rec = &ring[head % s_capSlots];
    rec->seq = seq;
    rec->raw_min = rawMin;
    rec->raw_max = rawMax;
    rec->busy_us = (uint16_t)((busyUs > UINT16_MAX) ? UINT16_MAX : busyUs);
    rec->flags = (uint8_t)((gateOpen ? AFSK_CAPTURE_FLAG_GATE_OPEN : 0) | (blanked ? AFSK_CAPTURE_FLAG_BLANKED : 0) |
                           (((rawMax >= AFSK_RAW_CLIP_HIGH) || (rawMin <= AFSK_RAW_CLIP_LOW)) ? AFSK_CAPTURE_FLAG_CLIP : 0));
    float g = s_agcGain * 16.0f + 0.5f;
    rec->agc_x16 = (uint8_t)((g > 255.0f) ? 255.0f : g);
    for (int i = 0; i < AFSK_CAPTURE_SAMPLES; i++) {
        float v = audio[i] * 16384.0f;
        rec->samples[i] = (int16_t)((v > 32767.0f) ? 32767.0f : ((v < -32768.0f) ? -32768.0f : v));
    }
    __atomic_store_n(&s_capHead, head + 1, __ATOMIC_RELEASE);
}

static void afsk_rx_task(void *arg) {
    (void)arg;

    // One conversion frame - MODEM_ADC_CONV_FRAME samples, not a whole DSP
    // block. adc_continuous_read() hands back at most one frame per call, and
    // AFSK_Poll() below only acts once MODEM_BLOCK_SIZE samples have
    // accumulated in the FIFO, so a short read costs nothing but a loop.
    // Static rather than automatic so that a conversion frame never has to be
    // carried on this task's stack.
    static uint8_t convBuf[MODEM_ADC_CONV_FRAME_BYTES];

    while (!s_rxStop) {
        // Hold point for afskSetModem(): here, between two conversion frames,
        // nothing of the demodulators or of the AX.25 receive ring is in use.
        // Leaving it goes back through the loop head, so a request raised
        // again in the meantime is honoured before any sample is processed.
        if (__atomic_load_n(&s_rxPauseReq, __ATOMIC_ACQUIRE)) {
            __atomic_store_n(&s_rxPaused, true, __ATOMIC_RELEASE);
            while (__atomic_load_n(&s_rxPauseReq, __ATOMIC_ACQUIRE) && !s_rxStop)
                vTaskDelay(1);
            __atomic_store_n(&s_rxPaused, false, __ATOMIC_RELEASE);
            continue;
        }

        uint32_t got = 0;

        // Blocks on the driver's own pool. Its ISR fills that pool with an
        // xRingbufferSendFromISR() whose critical section is bounded by
        // MODEM_ADC_CONV_FRAME rather than by the DSP block size, and runs on
        // MODEM_ADC_ISR_CORE, which is not where the DAC clock lives. Nothing
        // of ours runs at interrupt level, so however long the DSP below takes,
        // the DAC timer keeps its cadence. The 100 ms timeout is both a safety
        // net and what lets s_rxStop be noticed within a bounded time.
        esp_err_t err = adc_continuous_read(s_adc, convBuf, sizeof(convBuf), &got, ADC_READ_TIMEOUT_MS);
        if (err != ESP_OK || got == 0)
            continue;

        adc_ingest(convBuf, got);
        AFSK_Poll();
    }

    // Exit under our own power. This task blocks inside the ADC driver's ring
    // buffer, and vTaskDelete()ing a task that is blocked on a ring buffer
    // leaves that ring buffer's internal lists pointing at freed TCB memory.
    // AFSK_deinit() therefore asks this task to stop and waits, rather than
    // deleting it from the outside.
    s_rxExited = true; // AFSK_deinit() clears s_rxTask; do not race it here
    vTaskDelete(NULL);
}

// ------------------------------------------------------------------
// Modem profile
// ------------------------------------------------------------------

// @brief Hold afsk_rx_task at the top of its loop and wait until it is there.
//
// The wait is bounded by one ADC read timeout plus one DSP block. A task that
// has already left its loop is not waited for.
static void rxPause(void) {
    if (s_rxTask == NULL)
        return;
    __atomic_store_n(&s_rxPauseReq, true, __ATOMIC_RELEASE);
    while (!__atomic_load_n(&s_rxPaused, __ATOMIC_ACQUIRE) && !s_rxExited)
        vTaskDelay(1);
}

// @brief Let afsk_rx_task continue after rxPause().
static void rxResume(void) {
    __atomic_store_n(&s_rxPauseReq, false, __ATOMIC_RELEASE);
}

void afskSetModem(uint8_t val, bool flatAudio, uint16_t timeSlot, uint16_t preamble, uint16_t txTail, uint8_t fx25Mode, uint16_t minUnkeyMs) {
    // afsk_rx_task runs continuously on its own (possibly pinned) core,
    // calling AFSK_Poll() -> MODEM_DECODE() -> demodulate() -> filterRun()
    // on whatever is currently in demodState[], and Ax25BitParse() writes the
    // frames it completes into the AX.25 receive ring. ModemInit() below does
    // a memset() of demodState[] followed by piecemeal reassignment of each
    // filter's coeffs/taps, and Ax25Init() resets the ring indices. A receive
    // task running concurrently could observe a torn DemodState (a stale
    // nonzero `taps` paired with a just-cleared NULL `coeffs` crashes
    // filterRun()) or publish a frame slot computed against the old indices.
    // It is therefore held at the top of its loop, where it is between two
    // conversion frames and touches neither, for the whole rebuild. Stopping
    // it there rather than suspending it wherever it happens to be is what
    // makes the hold point safe.
    rxPause();

    ModemConfig.flatAudioIn = flatAudio ? 1 : 0;
    ModemConfig.usePWM = 1;

    // val is the modem_mode_t selector (0=AFSK300, 1=Bell202, 2=V.23, 3=G3RUH);
    // out-of-range values fall back to standard-APRS Bell202.
    ModemConfig.modem = (val <= MODEM_MODEM_G3RUH) ? (modem_mode_t)val : MODEM_MODEM_BELL202;

    ModemInit();
    Ax25Init(fx25Mode);
    Ax25Config.fullDuplex = s_fullDuplex ? 1 : 0;
#ifdef ENABLE_FX25
    if (fx25Mode > 0)
        Fx25Init();
#endif
    Ax25TimeSlot(timeSlot);
    Ax25TxDelay(preamble);
    Ax25TxTail(txTail);
    Ax25MinUnkeyTime(minUnkeyMs);

    // Reset the RX front-end so a profile change cannot leak old state, and
    // apply the front-end settings stored by afskSetRxFrontEnd().
    rx_dc_block_reset(&s_dcBlock);
    s_dcdCnt = 0;
    s_gateOpen = false;
    s_holdHead = 0;
    s_holdCount = 0;

    s_gateOnMv = s_pendGateMv;
    s_gateOffMv = (uint16_t)(s_pendGateMv / 2);
    s_blankOn = s_pendBlank;
    impulse_blanker_reset(&s_blanker);
    rx_hpf_setup(&s_hpf, s_pendHpfHz, (float)MODEM_DEMOD_SAMPLERATE);
    s_agcFixed = s_pendAgcFixed;
    s_fixedGain = powf(10.0f, (float)s_pendFixedGainDb / 20.0f);
    s_agcGain = s_agcFixed ? s_fixedGain : 1.0f;
    band_meter_setup();
    s_bandMvRms = 0;
    AFSK_FlushFifo();

    rxResume();

    // Logged only once the receive task runs again: the console takes several
    // milliseconds per line, longer in total than the ADC driver's pool can
    // buffer while nothing drains it.
    ESP_LOGI(TAG, "modem=%d adcRate=%d blockSize=%d resample=%d demodRate=%d", (int)ModemConfig.modem, MODEM_ADC_SAMPLERATE, MODEM_BLOCK_SIZE,
             MODEM_RESAMPLE_RATIO, MODEM_DEMOD_SAMPLERATE);
    ModemLogConfig();
    ESP_LOGI(TAG, "RX front end: impulse blanker %s, gate %s%u mV (tone band), high-pass %s%u Hz, gain %s %.2fx", s_blankOn ? "on" : "off",
             s_gateOnMv ? "" : "off/", (unsigned)s_gateOnMv, s_hpf.on ? "" : "off/", (unsigned)s_pendHpfHz, s_agcFixed ? "fixed" : "auto, start",
             (double)s_agcGain);
}

// ------------------------------------------------------------------
// Core-pinned bring-up
// ------------------------------------------------------------------

// esp_intr_alloc() binds an interrupt to whichever core calls it. Both the ADC
// DMA interrupt and the DAC GPTimer interrupt are allocated inside driver calls
// (adc_continuous_new_handle() and gptimer_register_event_callbacks()
// respectively), which put both of them on core 0.
//
// run_on_core() removes the accident. esp_ipc_call_blocking() would be the
// obvious tool, but CONFIG_ESP_IPC_TASK_STACK_SIZE defaults to 1024 bytes and
// these callees allocate, log and touch the interrupt tables; a throwaway
// pinned task with a real stack is both safer and easier to reason about.
//
// Teardown does not need this: esp_intr_free() detects a cross-core call and
// IPCs itself to the right core, and esp_intr_enable()/disable() go through the
// interrupt matrix for peripheral sources, which works from either core.
typedef struct {
    esp_err_t (*fn)(void);
    esp_err_t err;
    TaskHandle_t caller;
} core_call_t;

static void core_call_task(void *arg) {
    core_call_t *c = (core_call_t *)arg;

    c->err = c->fn();
    xTaskNotifyGive(c->caller);
    vTaskDelete(NULL);
}

static esp_err_t run_on_core(int core, esp_err_t (*fn)(void)) {
#if CONFIG_FREERTOS_UNICORE
    (void)core;
    return fn();
#else
    if ((core < 0) || (core >= CONFIG_FREERTOS_NUMBER_OF_CORES) || (core == xPortGetCoreID()))
        return fn(); // already there, or no preference expressed

    core_call_t call = { .fn = fn, .err = ESP_FAIL, .caller = xTaskGetCurrentTaskHandle() };

    if (xTaskCreatePinnedToCore(core_call_task, "modem_init", 4096, &call, configMAX_PRIORITIES - 2, NULL, core) != pdPASS) {
        ESP_LOGE(TAG, "cannot create the bring-up task for core %d", core);
        return ESP_ERR_NO_MEM;
    }

    ulTaskNotifyTake(pdTRUE, portMAX_DELAY);
    return call.err;
#endif
}

// ------------------------------------------------------------------
// Init / deinit
// ------------------------------------------------------------------

// @brief Create, configure and enable the DAC sample clock.
//
// MUST run on MODEM_DAC_TIMER_CORE: gptimer_register_event_callbacks() is
// where the interrupt is actually allocated, and esp_intr_alloc() binds to the
// calling core.
//
// Why the core matters at all, given intr_priority 3 is the highest an IDF C
// handler can have: because portENTER_CRITICAL_ISR() masks to level 3. Level 3
// is not "above" critical sections, it is exactly what they mask. Any driver
// ISR on this core that takes a spinlock silences the modulator for as long as
// it holds it, and the ADC's holds one across a whole conversion frame. A
// spinlock only raises INTLEVEL on its own core, so the cure is separation, not
// priority. Everything else about this handler - IRAM_ATTR, DRAM_ATTR tables,
// the direct dac_ll write - remains necessary; it just was not the last thing
// blocking it.
static esp_err_t dac_timer_create(void) {
    esp_err_t err;

    // The resolution stays at 10 MHz. 10000000 / 38400 = 260.4 truncates to 260
    // ticks, so the timer really runs at 38461.5 Hz, +0.16 % above the rate
    // modem.c derives its steps from. That is deliberate: 38400 Hz cannot be
    // hit exactly from the 80 MHz APB at any divider (80e6 / 38400 = 2083.33),
    // and a uniform rate error of that size is nothing - the demodulator's DPLL
    // tracks a full 1.7 % of it without dropping a frame. It is bursty stalls,
    // not rate error, that this modem dies of.
    gptimer_config_t timerCfg = {
        .clk_src = GPTIMER_CLK_SRC_DEFAULT,
        .direction = GPTIMER_COUNT_UP,
        .resolution_hz = 10 * 1000 * 1000, // 10 MHz, 1 tick = 100 ns
        .intr_priority = MODEM_DAC_TIMER_INTR_PRIO,
    };
    err = gptimer_new_timer(&timerCfg, &s_dacTimer);
    if (err != ESP_OK) {
        ESP_LOGE(TAG, "gptimer_new_timer: %s", esp_err_to_name(err));
        return err;
    }

    // This call allocates the interrupt. Whatever core we are on now is the
    // core the DAC sample clock will live on for the rest of the run.
    gptimer_event_callbacks_t timerCbs = { .on_alarm = dac_timer_isr };
    err = gptimer_register_event_callbacks(s_dacTimer, &timerCbs, NULL);
    if (err != ESP_OK) {
        ESP_LOGE(TAG, "gptimer_register_event_callbacks: %s", esp_err_to_name(err));
        return err;
    }

    err = gptimer_enable(s_dacTimer);
    if (err != ESP_OK) {
        ESP_LOGE(TAG, "gptimer_enable: %s", esp_err_to_name(err));
        return err;
    }

    gptimer_alarm_config_t alarmCfg = {
        .alarm_count = 10000000ULL / (uint64_t)s_dacRate,
        .reload_count = 0,
        .flags.auto_reload_on_alarm = true,
    };
    err = gptimer_set_alarm_action(s_dacTimer, &alarmCfg);
    if (err != ESP_OK) {
        ESP_LOGE(TAG, "gptimer_set_alarm_action: %s", esp_err_to_name(err));
        return err;
    }

    s_dacTimerRunning = false;
    s_dacAlarmRateHz = 10000000.0f / (float)alarmCfg.alarm_count;

    // Print what the timer will REALLY do, not what was asked for. Stage 2 of
    // the characterisation counts ISR invocations and compares them against the
    // nominal rate, so without this line a 2 % shortfall caused by missed alarms
    // is indistinguishable from a 2 % clock error. Any gap between the measured
    // ISR rate and the alarm rate below is the ISR failing to keep up.
    ESP_LOGI(TAG, "DAC timer: %" PRIu32 " Hz nominal -> alarm every %" PRIu64 " ticks = %.1f Hz actual, ISR prio %d on core %d", s_dacRate,
             alarmCfg.alarm_count, 10000000.0 / (double)alarmCfg.alarm_count, MODEM_DAC_TIMER_INTR_PRIO, xPortGetCoreID());
    return ESP_OK;
}

esp_err_t AFSK_init(void) {
    esp_err_t err;

    if (s_inited)
        return ESP_OK;

    rb_init(&s_fifo);

    // s_pttGpio is the fixed ::MODEM_PTT_GPIO compile-time constant.
    //
    // GPIO_MODE_INPUT_OUTPUT, not GPIO_MODE_OUTPUT: on ESP32 the input path
    // (pad input buffer / FUN_IE) is a separate enable from the output
    // driver, and gpio_config(GPIO_MODE_OUTPUT) does not turn it on. With
    // only GPIO_MODE_OUTPUT the pad reads back as 0 no matter what level is
    // actually being driven, so the keying line cannot be observed on-chip at
    // all. INPUT_OUTPUT keeps the pin driven by setPtt() while leaving the
    // real pad voltage readable, which is what makes a keying fault
    // diagnosable from a debugger without a scope on the PTT line.
    if (s_pttGpio >= 0) {
        gpio_config_t pttCfg = {
            .pin_bit_mask = 1ULL << s_pttGpio,
            .mode = GPIO_MODE_INPUT_OUTPUT,
        };

        // The idle level is published before the pad becomes an output. The
        // output register resets to 0, which is the ACTIVE level for an
        // active-low PTT, so a pad that takes its direction first drives the
        // keying line active for the length of the configuration call - and
        // modem_init() goes on to spend about five seconds measuring the ADC
        // clock right after this. Writing the level first sends the pad
        // straight to idle; the write after gpio_config() is what puts it
        // there when the output register was not the path taken.
        gpio_set_level((gpio_num_t)s_pttGpio, s_pttActiveHigh ? 0 : 1);
#ifdef AFSK_HAVE_GPIO_RESERVE
        // Same owner, same pad, same mode: releasing the claim the earlier
        // configuration took is what makes this one a plain reconfiguration.
        esp_gpio_revoke(1ULL << s_pttGpio);
#endif
        gpio_config(&pttCfg);
        gpio_set_level((gpio_num_t)s_pttGpio, s_pttActiveHigh ? 0 : 1);
    }
#if MODEM_LED_TX_GPIO >= 0
    gpio_config_t ledTxCfg = { .pin_bit_mask = 1ULL << MODEM_LED_TX_GPIO, .mode = GPIO_MODE_OUTPUT };
    gpio_config(&ledTxCfg);
#endif
#if MODEM_LED_RX_GPIO >= 0
    gpio_config_t ledRxCfg = { .pin_bit_mask = 1ULL << MODEM_LED_RX_GPIO, .mode = GPIO_MODE_OUTPUT };
    gpio_config(&ledRxCfg);
#endif

    // ---- DAC ----
    dac_oneshot_config_t dacCfg = { .chan_id = MODEM_DAC_CHANNEL };
    err = dac_oneshot_new_channel(&dacCfg, &s_dac);
    if (err != ESP_OK) {
        ESP_LOGE(TAG, "dac_oneshot_new_channel: %s", esp_err_to_name(err));
        return err;
    }
    dac_oneshot_output_voltage(s_dac, DAC_MID);
    ESP_LOGI(TAG, "DAC on GPIO%d (channel %d)", MODEM_DAC_GPIO, (int)MODEM_DAC_CHANNEL);

    // ---- ADC ----
    // Pinned: adc_continuous_new_handle() allocates the DMA interrupt, and
    // esp_intr_alloc() binds it to the calling core. This is the core whose
    // level 3 gets masked across every conversion-frame memcpy, so it must be
    // a core the modulator is not on.
    err = run_on_core(MODEM_ADC_ISR_CORE, adc_start_continuous);
    if (err != ESP_OK)
        return err;

    // After the continuous driver, never before it: bringing the ADC up puts
    // the pad in analog mode and disconnects both of its pull resistors, so the
    // selection is applied once the driver is done with the pin. Nothing else
    // reconfigures the pad afterwards - afskSetModem() only rebuilds the
    // demodulator and AX.25 state - so this holds until AFSK_deinit().
    if (s_adcSelfBias)
        afskSetAdcSelfBias(true);

    // ---- DAC sample clock ----
    // Pinned to the other core. See dac_timer_create().
    err = run_on_core(MODEM_DAC_TIMER_CORE, dac_timer_create);
    if (err != ESP_OK)
        return err;

    // ---- DSP task ----
    BaseType_t ok;
    s_rxStop = false;
    s_rxExited = false;
#if MODEM_RX_TASK_CORE >= 0
    ok = xTaskCreatePinnedToCore(afsk_rx_task, "afsk_rx", MODEM_RX_TASK_STACK, NULL, MODEM_RX_TASK_PRIO, &s_rxTask, MODEM_RX_TASK_CORE);
#else
    ok = xTaskCreate(afsk_rx_task, "afsk_rx", MODEM_RX_TASK_STACK, NULL, MODEM_RX_TASK_PRIO, &s_rxTask);
#endif
    if (ok != pdPASS) {
        ESP_LOGE(TAG, "cannot create the RX task");
        return ESP_ERR_NO_MEM;
    }

    setTransmit(false);
    __atomic_store_n(&s_txStopPending, false, __ATOMIC_RELEASE); // nothing was transmitted, so no teardown is owed
    s_inited = true;
    ESP_LOGI(TAG, "AFSK hardware ready (%s duplex)", s_fullDuplex ? "full" : "half");
    return ESP_OK;
}

void AFSK_deinit(void) {
    if (!s_inited)
        return;

    if (s_rxTask) {
        TaskHandle_t rx = s_rxTask;

        // A task held by afskSetModem() leaves its hold point as soon as it
        // sees s_rxStop, so no separate release is needed.
        s_rxStop = true;
        rxResume();
        for (int i = 0; (i < 40) && !s_rxExited; i++) // the read timeout is 100 ms
            vTaskDelay(pdMS_TO_TICKS(10));
        if (!s_rxExited) {
            ESP_LOGW(TAG, "RX task did not exit in 400 ms, deleting it");
            vTaskDelete(rx);
        }
        s_rxTask = NULL;
    }
    if (s_adc) {
        adc_continuous_stop(s_adc);
        adc_continuous_deinit(s_adc);
        s_adc = NULL;
    }
    if (s_cali) {
        adc_cali_delete_scheme_line_fitting(s_cali);
        s_cali = NULL;
    }
    if (s_dacTimer) {
        // No core juggling needed on the way out, unlike AFSK_init(): the
        // timer's interrupt lives on MODEM_DAC_TIMER_CORE, but esp_intr_free()
        // (reached via gptimer_del_timer) detects a cross-core call and IPCs
        // itself over, and esp_intr_disable() for a peripheral source goes
        // through the interrupt matrix, which either core may write.
        if (s_dacTimerRunning) {
            gptimer_stop(s_dacTimer);
            s_dacTimerRunning = false;
        }
        gptimer_disable(s_dacTimer);
        gptimer_del_timer(s_dacTimer);
        s_dacTimer = NULL;
    }
    if (s_dac) {
        dac_oneshot_del_channel(s_dac);
        s_dac = NULL;
    }
#ifdef AFSK_HAVE_GPIO_RESERVE
    // Hand the pads back, so whoever configures them next - a later
    // AFSK_init(), or the application - starts from an unclaimed pin. The
    // levels are left as they are: the PTT pad stays at its idle level, which
    // is the whole point of driving it.
    if (s_pttGpio >= 0)
        esp_gpio_revoke(1ULL << s_pttGpio);
#if MODEM_LED_TX_GPIO >= 0
    esp_gpio_revoke(1ULL << MODEM_LED_TX_GPIO);
#endif
#if MODEM_LED_RX_GPIO >= 0
    esp_gpio_revoke(1ULL << MODEM_LED_RX_GPIO);
#endif
#endif
    s_inited = false;
    ESP_LOGI(TAG, "AFSK hardware released");
}
