hiperiondev/esp32idf_APRS/components/esp32idf_radioamateur_modem/src/ax25.c

// @file ax25.c
//
// @author Emiliano Augusto Gonzalez ( lu3vea @ gmail . com)
// @date 2026
// @copyright GNU General Public License v3
// @see https://github.com/hiperiondev/esp32idf_APRS
//
// @note
// This is based on other projects:
//     VP-Digi: https://github.com/sq8vps/vp-digi
//     ESP32APRS: https://github.com/nakhonthai/ESP32APRS_Audio
//     LibAPRS: https://github.com/markqvist/LibAPRS
//
//     please contact their authors for more information.
//
// @brief AX.25 frame handling implementation: HDLC bit-level receive and
// transmit state machines, bit stuffing, FCS checking, frame buffering and the
// CSMA/p-persistence channel access logic.

#include <inttypes.h>
#include <stdbool.h>
#include <stdlib.h>
#include <string.h>

#include "esp_attr.h"
#include "esp_log.h"
#include "esp_random.h"
#include "esp_timer.h"

#include "afsk.h" // setPtt()/setTransmit()/AFSK_ServiceTx(): the keying and TX-teardown primitives this file drives
#include "ax25.h"
#include "crc_ccit.h"
#include "esp32idf_radioamateur_modem.h" // modem_format_tnc2() for the readable TX log line
#include "modem.h"

#ifdef ENABLE_FX25
#include "fx25.h"

// Both FX.25 buffers below are handed to a codec that rewrites a full 255-byte
// Reed-Solomon block whatever the mode's payload size K is, so they are sized
// to the block, never to K. Shrinking either one to a per-mode size is caught
// here at compile time instead of by an out-of-bounds write at runtime.
_Static_assert(AX25_FRAME_MAX_SIZE >= FX25_MAX_BLOCK_SIZE, "rx frame buffer must hold a whole FX.25 block");
#endif

static const char *TAG = "ax25";

struct Ax25ProtoConfig Ax25Config;

// One slot is deliberately left unused in each handle ring so that
// head == tail unambiguously means "empty" and head + 1 == tail means "full".
// Fullness is therefore derived from the two indices alone, with no shared
// flag that both cores would have to read-modify-write. Hence one more slot
// than the usable depth.
//
// Sized as AX25_TX_FRAME_RING_MAX+1 (12 slots, 11 usable): during
// digipeating/igating, several RF frames can arrive back-to-back and each
// gets re-queued for TX while the AFSK modem is still keying up and sending
// the previous one (hundreds of ms at 1200 baud), so the ring must hold that
// burst without overrunning and dropping later frames ("TX buffer full, frame
// dropped"). The usable depth matches the Radiomodem page's "TX buffers"
// field, which the user can set 1-11 (RF_TX_BUFFERS_MAX in aprs_service.h).
// FRAME_MAX_COUNT is defined in terms of the same AX25_TX_FRAME_RING_MAX the
// config layer clamps against (see ax25.h), so the reported capacity and the
// ring's real capacity always agree. Each ring slot costs AX25_FRAME_MAX_SIZE
// on the tx/rx byte buffers, which is negligible on ESP32.
#define FRAME_MAX_COUNT   (AX25_TX_FRAME_RING_MAX + 1) // ring slots; usable depth is FRAME_MAX_COUNT-1 == AX25_TX_FRAME_RING_MAX
#define FRAME_BUFFER_SIZE (FRAME_MAX_COUNT * AX25_FRAME_MAX_SIZE)

#define RING_NEXT(i) (((i) + 1u) % FRAME_MAX_COUNT)

// How long a just-accepted frame's CRC is remembered so that the other
// demodulators' copies of the SAME frame are recognised as duplicates and
// dropped.
//
// The counter is bumped once per Ax25BitParse() call, and there is one call
// per active demodulator per bit, so the hold is measured in bit periods
// scaled by ModemGetDemodulatorCount().
//
// The window has to exceed the worst-case inter-demodulator skew - the group
// delay of the longest prefilter is under two bits - and stay below the
// shortest interval at which a station could legitimately repeat a
// byte-identical frame. 32 bit periods is ~27 ms at 1200 Bd and ~107 ms at
// 300 Bd; both sit comfortably in that gap.
#define RX_DEDUP_HOLD_BITS 32

// Residue of the CRC register after running over a frame and its own FCS
// (CRC-16/X.25, reflected, initial value 0xFFFF, no final inversion applied).
#define AX25_CRC_GOOD_RESIDUE 0xF0B8

#define STATIC_HEADER_FLAG_COUNT 4 // flags sent before each frame
// The closing flag of the frame. Any flags after it belong to the TX tail
// (Ax25TxTail()), which keeps the carrier up until the radio's audio chain has
// passed the whole closing flag on to the air.
#define STATIC_FOOTER_FLAG_COUNT 1

#define CSMA_PERSIST_MISS_MAX 8 // consecutive missed persistence rolls on a clear channel before transmitting anyway

#define SYNC_BYTE 0x7E // preamble/postamble octet

static inline uint32_t millis(void) {
    return (uint32_t)(esp_timer_get_time() / 1000);
}

static inline uint32_t randomRange(uint32_t lo, uint32_t hi) {
    return lo + (esp_random() % (hi - lo));
}

struct FrameHandle {
    uint16_t start;
    uint16_t size;
    int8_t peak;
    int8_t valley;
    uint8_t level;
    uint8_t corrected;
    uint16_t mVrms;
    uint8_t demod;
    int8_t twistDb;
    uint8_t repaired;
#ifdef ENABLE_FX25
    // FX.25 coding of the frame, copied by value out of Fx25ModeList when the
    // frame is queued or received. Fx25ModeList lives in flash, and
    // Ax25GetTxBit() runs in the cache-safe DAC ISR, which keeps running while
    // a flash write or an OTA has the cache disabled; with the copy the ISR
    // only reads DRAM. fx25K == 0 marks a plain AX.25 frame.
    uint64_t fx25Tag;
    uint16_t fx25K;
    uint8_t fx25T;
#endif
};

#ifdef ENABLE_FX25
// @brief Record the FX.25 coding of a frame handle; NULL marks plain AX.25.
//
// Task context only: this is where a mode from Fx25ModeList is read on behalf
// of a frame handle, so the ISR can work from the copy alone.
static void frameSetFx25(struct FrameHandle *h, const struct Fx25Mode *mode) {
    if (mode != NULL) {
        h->fx25Tag = mode->tag;
        h->fx25K = mode->K;
        h->fx25T = mode->T;
    } else {
        h->fx25Tag = 0;
        h->fx25K = 0;
        h->fx25T = 0;
    }
}

// @brief true when the frame handle carries an FX.25 block.
//
// IRAM_ATTR: read by Ax25GetTxBit() from the DAC ISR, so it must not be left
// in flash when -Og declines to inline it. It only reads the handle itself.
static inline bool IRAM_ATTR frameIsFx25(const struct FrameHandle *h) {
    return h->fx25K != 0;
}
#endif
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
